djgreeb/XDJ-X/JOG VFL/VFL display description.pdf

### VFL display description

### Part Number: DEL1058-A Manufacturer: FUTABA Heater: V = 2,60-2,70Vrms or VDC Anode: V = 27,0V

### 135 sectors playing (C0-C134) 85 sectors cues (P0-P84) 3 sector vinyl sensor (V, M, S) Total: 223 segments

### 2 grids (left and right)

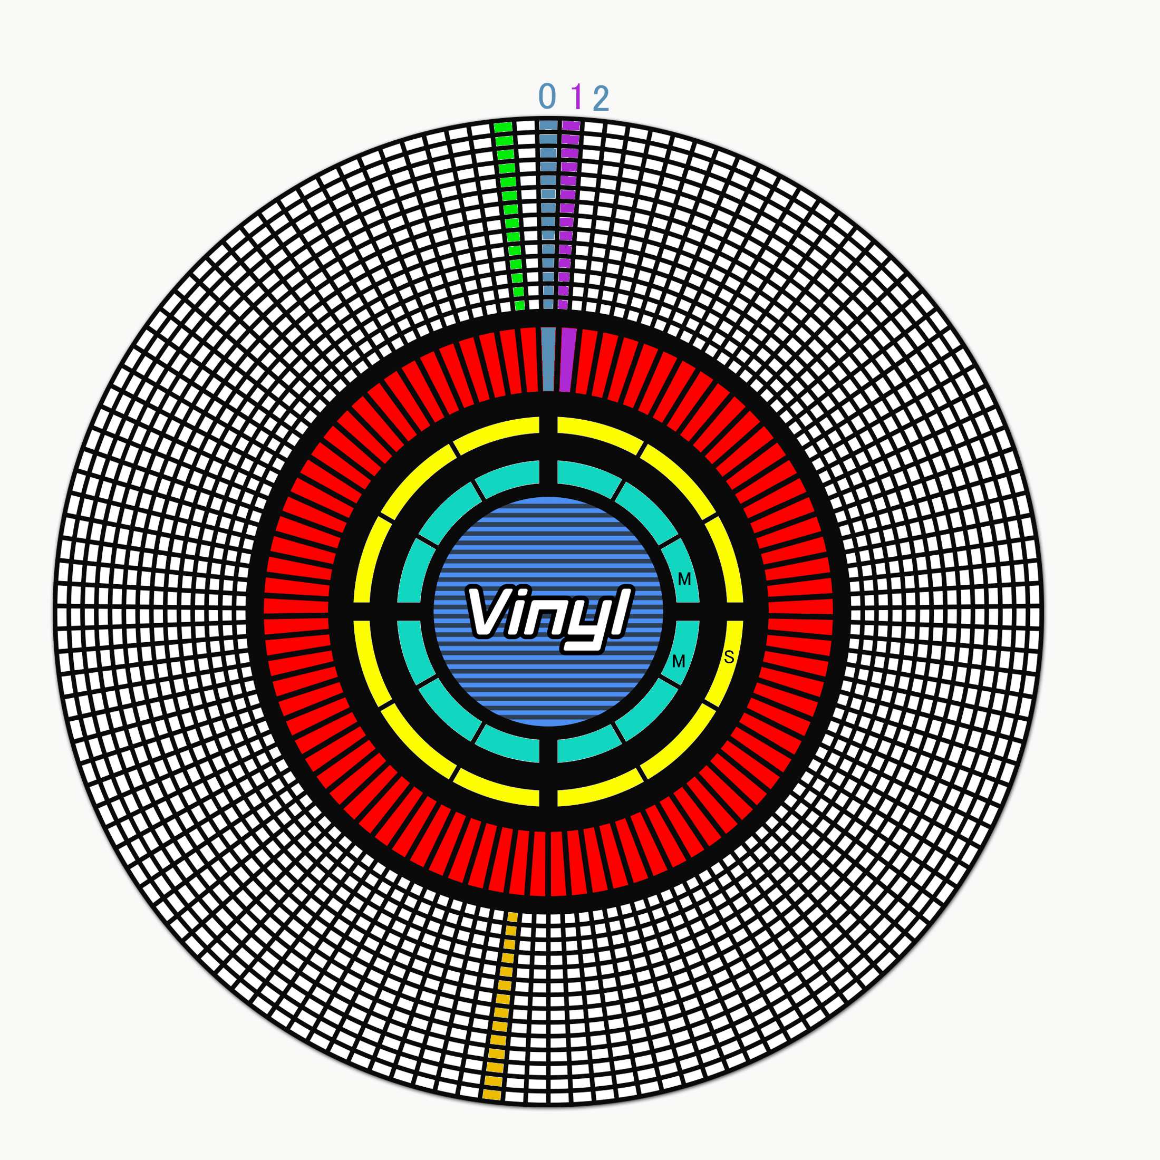
[picture p18: figure]

Num.byte | b7 | b6 | b5 | b4 | b3 | b2 | b1 | b0
0 | NC? | R grid | L grid | NC? | V | M | S | P70
1 | P69 | P68 | P67 | P66 | P65 | P64, P71 | P63, P72 | P62, P73
2 | P61, P74 | P60, P75 | P59, P76 | P58, P77 | P57, P78 | P56, P79 | P55, P80 | P54, P81
3 | C45 | C44 | C43 | P53, P82 | C42 | C41 | C40 | P52, P83
4 | C46, C39 | P51, P84 | C47, C38 | P50, P85 | C48, C37 | P49, P86 | C49, C36 | P48, P87
5 | C50, C35 | P47, P88 | C51, C34 | P46, P89 | C52, C33 | P45, P90 | C53, C32 | P44, P91
6 | C54, C31 | P43, P92 | C55, C30 | P42, P93 | C56, C29 | P41, P94 | C57, C28 | P40, P95
7 | C58, C27 | P39, P96 | C59, C26 | P38, P97 | C60, C25 | P37, P98 | C61, C24 | P36, P99
8 | C62, C23 | P35, P100 | C63, C22 | P34, P101 | C64, C21 | P33, P102 | C65, C20 | P32, P103
9 | C66, C19 | P31, P104 | C67, C18 | P30, P105 | C68, C17 | P29, P106 | C69, C16 | P28, P107
10 | C70, C15 | P27, P108 | C71, C14 | P26, P109 | C72, C13 | P25, P110 | C73, C12 | P24, P111
11 | C74, C11 | P23, P112 | C75, C10 | P22, P113 | C76, C9 | P21, P114 | C77, C8 | P20, P115
12 | C78, C7 | P19, P116 | C79, C6 | P18, P117 | C80, C5 | P17, P118 | C81, C4 | P16, P119
13 | C82, C3 | C2 | P15, P120 | C1 | C0 | P14, P121 | C84 | C83
14 | P13, P122 | P12, P123 | P11, P124 | P10, P125 | P9, P126 | P8, P127 | P7, P128 | P6, P129
15 | P5, P130 | P4, P131 | P3, P132 | P2 | P1 | P0 | P134 | P133

### Double grid

Num.byte | b7 | b6 | b5 | b4 | b3 | b2 | b1 | b0
| 0 | 1 | 2 | 3 | 4 | 5 | 6 | 7 0
| 0 | 1 | 1 | 0 | V | M | S | P70
| 8 | 9 | 10 | 11 | 12 | 13 | 14 | 15 1
| P69 | P68 | P67 | P66 | P65
| 16 | 17 | 18 | 19 | 29 | 21 | 22 | 23 2
24 | 25 | 26 | 27 | 28 | 29 | 30 | 31 3
C45 | C44 | C43 | | C42 | C41 | C40
32 | 33 | 34 | 35 | 36 | 37 | 38 | 39 4
40 | 41 | 42 | 43 | 44 | 45 | 46 | 47 5
48 | 49 | 50 | 51 | 52 | 53 | 54 | 55 6
56 | 57 | 58 | 59 | 60 | 61 | 62 | 63 7
64 | 65 | 66 | 67 | 68 | 69 | 70 | 71 8
72 | 73 | 74 | 75 | 76 | 77 | 78 | 79 9
80 | 81 | 82 | 83 | 84 | 85 | 86 | 87 10
88 | 89 | 90 | 91 | 92 | 93 | 94 | 95 11
96 | 97 | 98 | 99 | 100 | 101 | 102 | 103 12
104 | 105 | 106 | 107 | 108 | 109 | 110 | 111 13
| C2 | | C1 | C0 | | C84 | C83
112 | 113 | 114 | 115 | 116 | 117 | 118 | 119 14
120 | 121 | 122 | 123 | 124 | 125 | 126 | 127 15
| | | P2 | P1 | P0 | P134 | P133

### Left grid

Num.byte | b7 | b6 | b5 | b4 | b3 | b2 | b1 | b0
| 128 | 129 | 130 | 131 | 132 | 133 | 134 | 135 16
| 0 | 0 | 1 | 0
| 136 | 137 | 138 | 139 | 140 | 141 | 142 | 143 17
| | | | | | P71 | P72 | P73
| 144 | 145 | 146 | 147 | 148 | 149 | 150 | 151 18
P74 | P75 | P76 | P77 | P78 | P79 | P80 | P81
| 152 | 153 | 154 | 155 | 156 | 157 | 158 | 159 19
| | | | P82 | | | | P83
| 160 | 161 | 162 | 163 | 164 | 165 | 166 | 167 20
| C46 | P84 | C47 | P85 | C48 | P86 | C49 | P87
| 168 | 169 | 170 | 171 | 172 | 173 | 174 | 175 21
| C50 | P88 | C51 | P89 | C52 | P90 | C53 | P91
| 176 | 177 | 178 | 179 | 180 | 181 | 182 | 183 22
| C54 | P92 | C55 | P93 | C56 | P94 | C57 | P95
| 184 | 185 | 186 | 187 | 188 | 189 | 190 | 191 23
| C58 | P96 | C59 | P97 | C60 | P98 | C61 | P99
| 192 | 193 | 194 | 195 | 196 | 197 | 198 | 199 24
| C62 | P100 | C63 | P101 | C64 | P102 | C65 | P103
| 200 | 201 | 202 | 203 | 204 | 205 | 206 | 207 25
| C66 | P104 | C67 | P105 | C68 | P106 | C69 | P107
| 208 | 209 | 210 | 211 | 212 | 213 | 214 | 215 26
| C70 | P108 | C71 | P109 | C72 | P110 | C73 | P111
| 216 | 217 | 218 | 219 | 220 | 221 | 222 | 223 27
| C74 | P112 | C75 | P113 | C76 | P114 | C77 | P115
| 224 | 225 | 226 | 227 | 228 | 229 | 230 | 231 28
C78 | P116 | C79 | P117 | C80 | P118 | C81 | P119
| 232 | 233 | 234 | 235 | 236 | 237 | 238 | 239 29
| C82 | | P120 | | | P121
| 240 | 241 | 242 | 243 | 244 | 245 | 246 | 247 30
| P122 | P123 | P124 | P125 | P126 | P127 | P128 | P129
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
| 360 | 361 | 362 | 363 | 364 | 365 | 366 | 367 45
| C3 | | P15 | | | P14
| 368 | 369 | 370 | 371 | 372 | 373 | 374 | 375 46
P13 | P12 | P11 | P10 | P9 | P8 | P7 | P6
| 376 | 377 | 378 | 379 | 380 | 381 | 382 | 383 47
| P5 | P4 | P3

### Author: Andrei Anatska
