djgreeb/XDJ-X/Bluetooth/Ugreen TX/IMG_7054.JPG

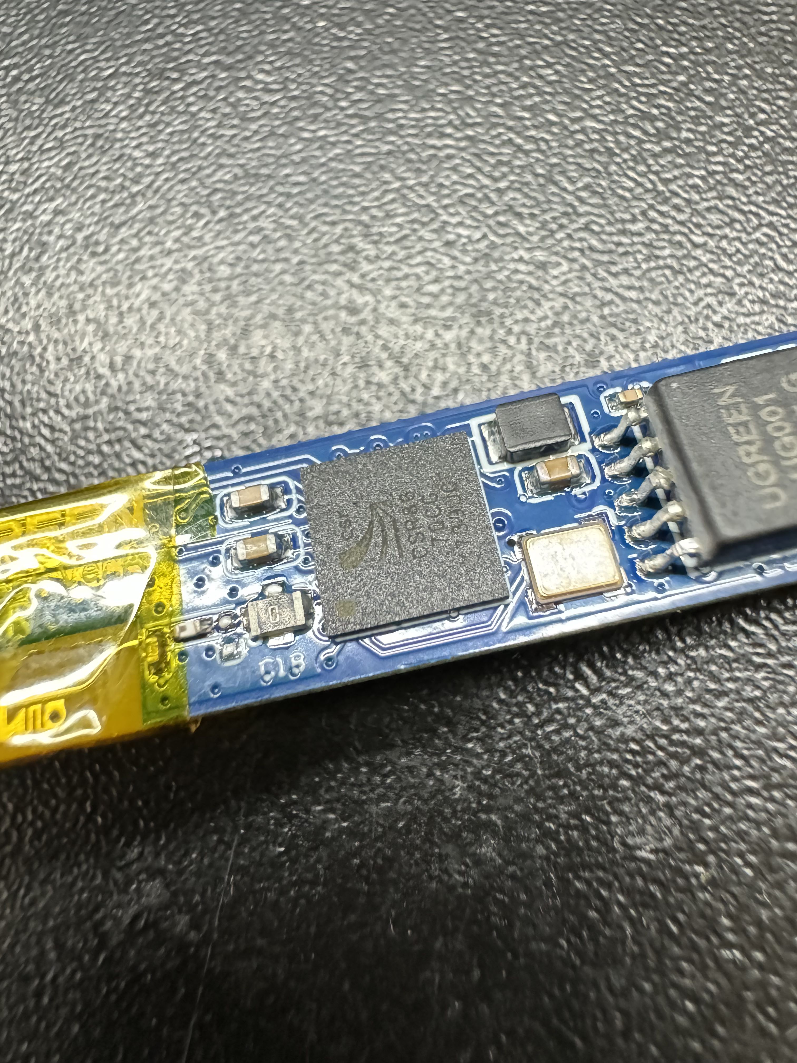
Bluetooth/Ugreen TX/IMG_7054.JPG
