djgreeb/XDJ-X/Bluetooth/Ugreen TX/IMG_7055.JPG

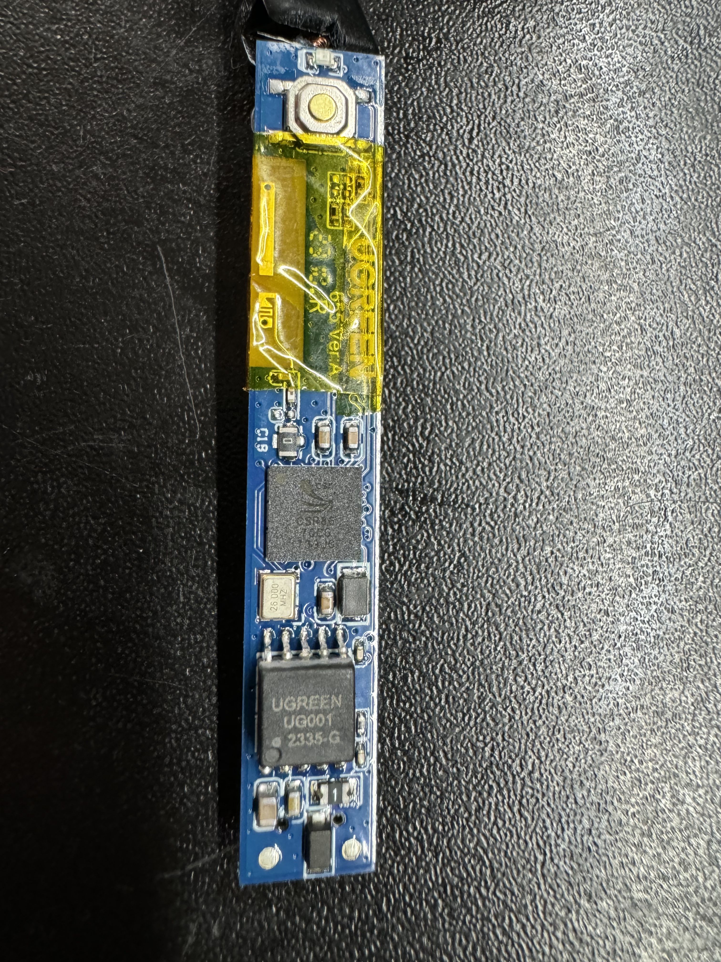
Bluetooth/Ugreen TX/IMG_7055.JPG
