djgreeb/XDJ-X/DECK_ASSY/FW_BACKUP/PINS sockets.png

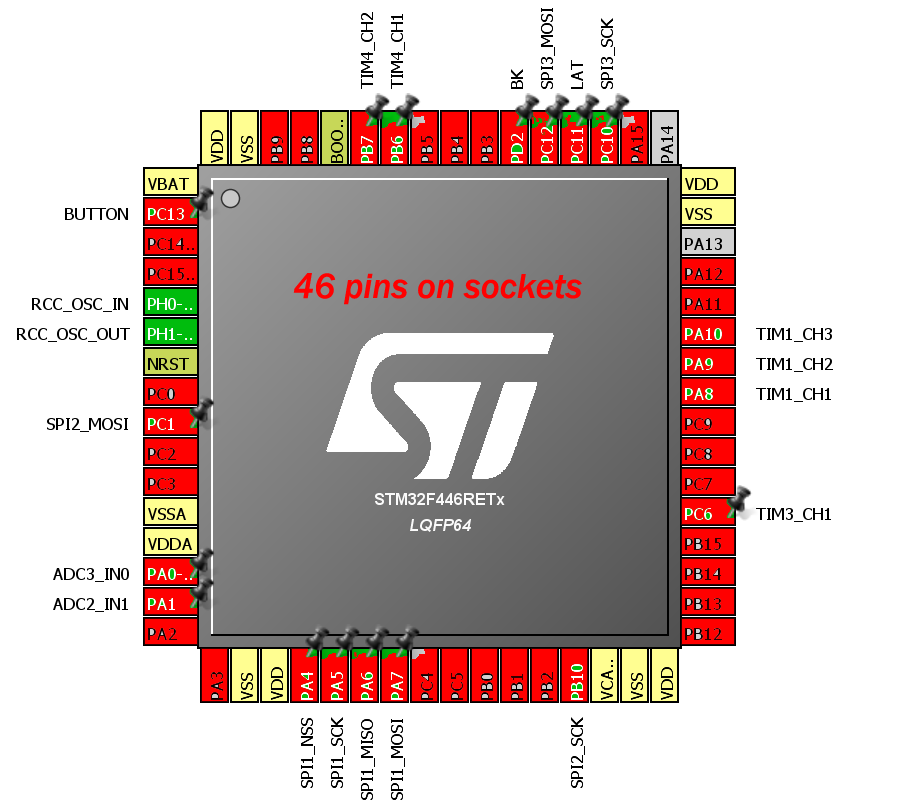
DECK_ASSY/FW_BACKUP/PINS sockets.png
