djgreeb/XDJ-X/DECK_ASSY/IMG_7581.JPG

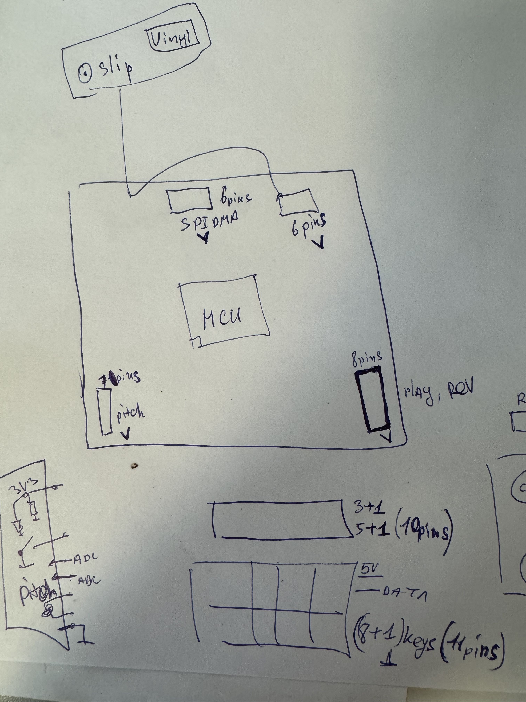
DECK_ASSY/IMG_7581.JPG
