djgreeb/XDJ-X/DECK_ASSY/IMG_7596.JPG

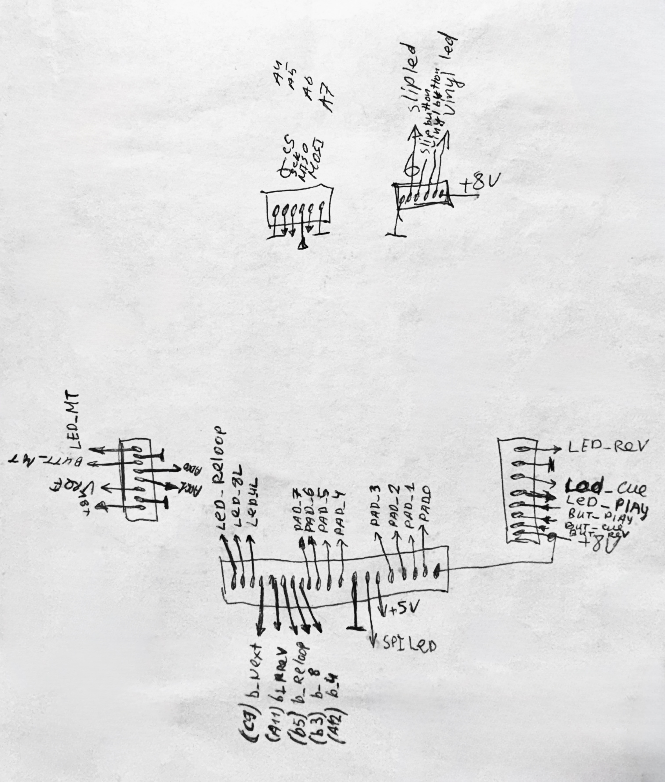
DECK_ASSY/IMG_7596.JPG
