djgreeb/XDJ-X/JOG VFL/CDJ-2000nxs/F1.png

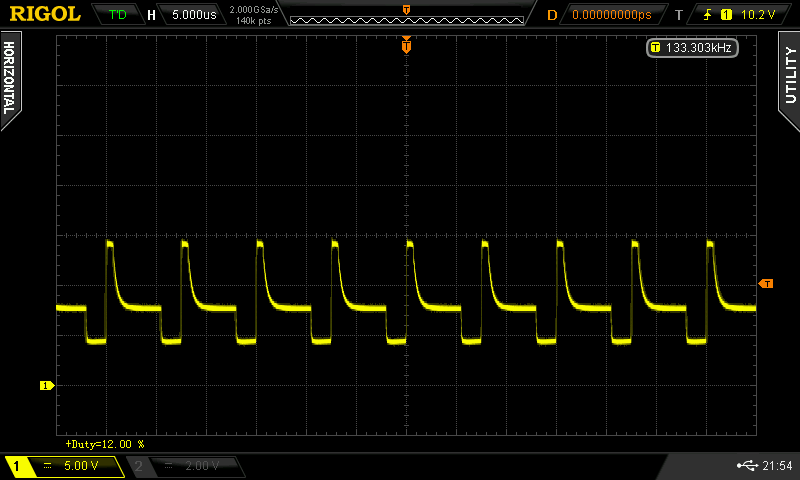
JOG VFL/CDJ-2000nxs/F1.png
