djgreeb/XDJ-X/JOG VFL/CDJ-2000nxs/F2.png

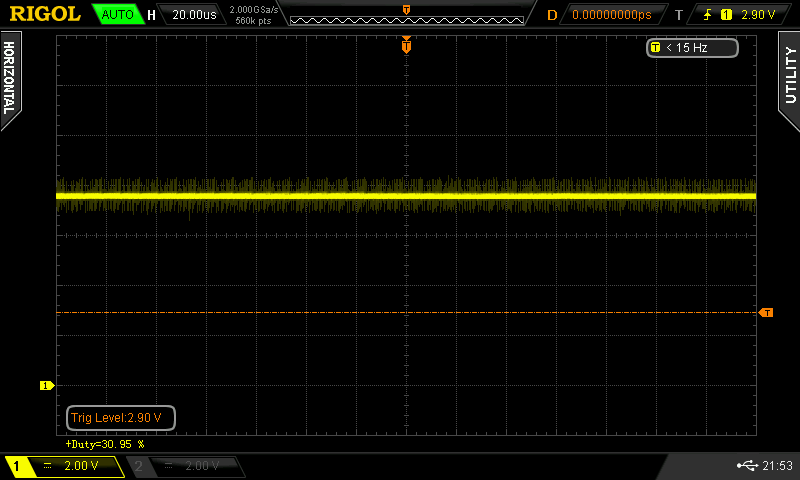
JOG VFL/CDJ-2000nxs/F2.png
