djgreeb/XDJ-X/JOG VFL/CDJ-2000nxs/tft spi clk.png

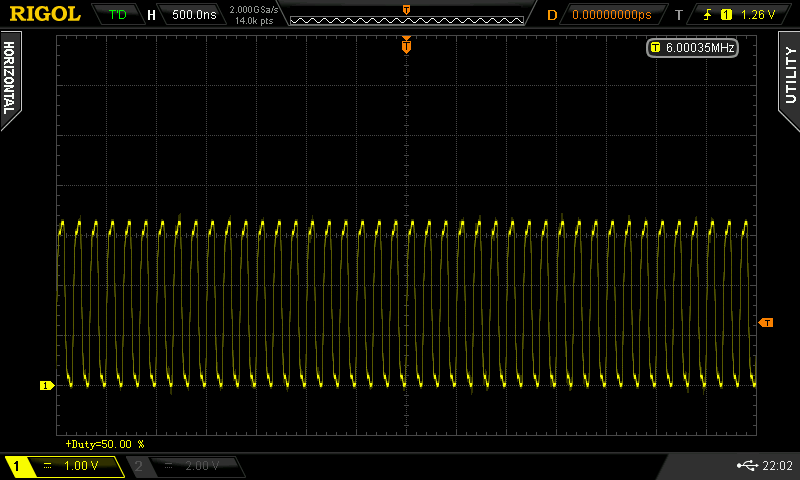
JOG VFL/CDJ-2000nxs/tft spi clk.png
