djgreeb/XDJ-X/JOG VFL/CDJ-2000nxs/tft spi cs.png

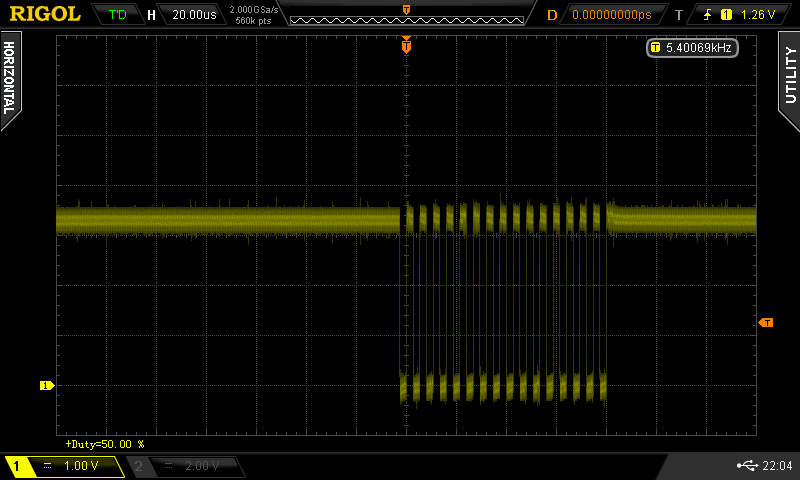
JOG VFL/CDJ-2000nxs/tft spi cs.png
