djgreeb/XDJ-X/JOG VFL/CDJ-2000nxs/tft spi data(1).png

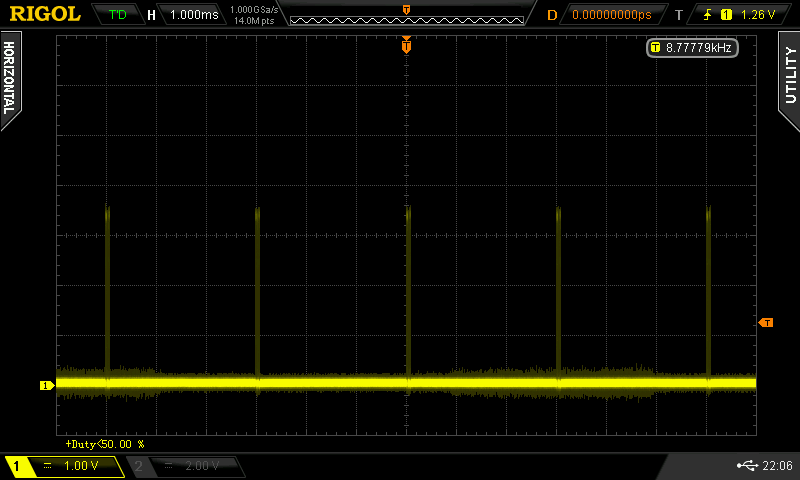
JOG VFL/CDJ-2000nxs/tft spi data(1).png
