djgreeb/XDJ-X/JOG VFL/CDJ-2000nxs/tft spi data.png

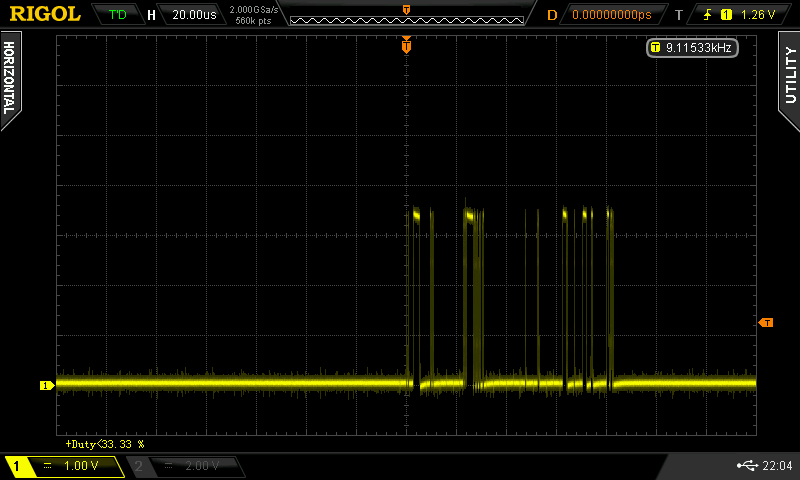
JOG VFL/CDJ-2000nxs/tft spi data.png
