djgreeb/XDJ-X/JOG VFL/CDJ-2000nxs/Transformer diode.png

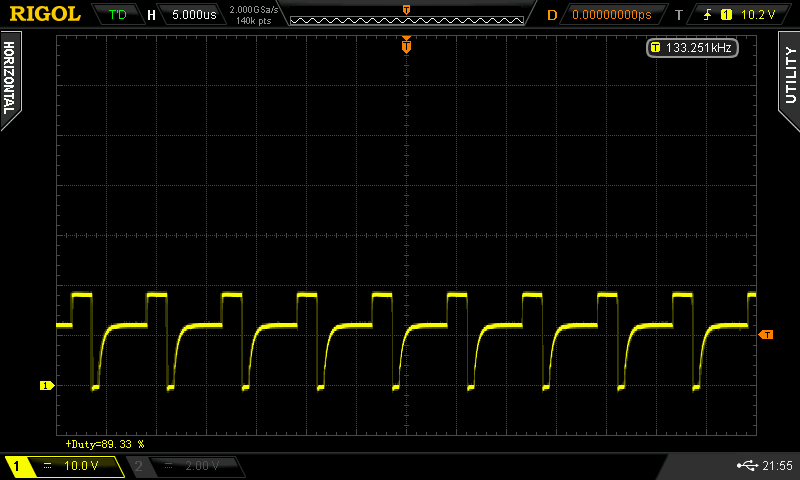
JOG VFL/CDJ-2000nxs/Transformer diode.png
