djgreeb/XDJ-X/JOG VFL/CDJ-2000nxs/Transformer input.png

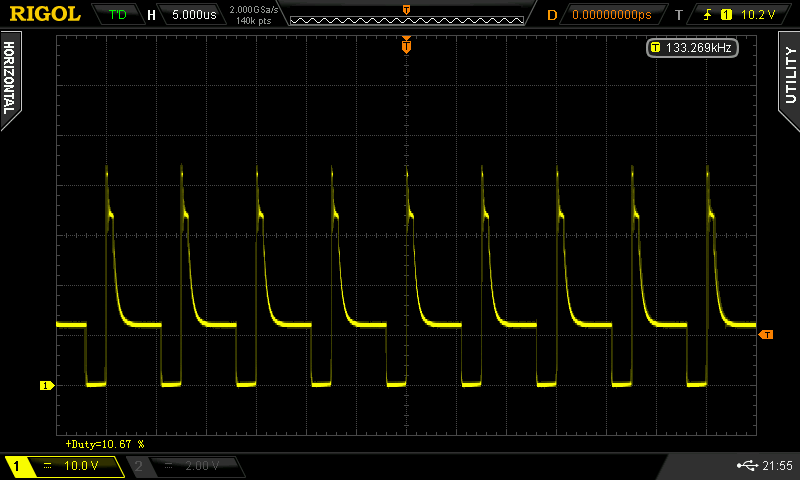
JOG VFL/CDJ-2000nxs/Transformer input.png
