djgreeb/XDJ-X/JOG VFL/Transformer charasteristics.JPG

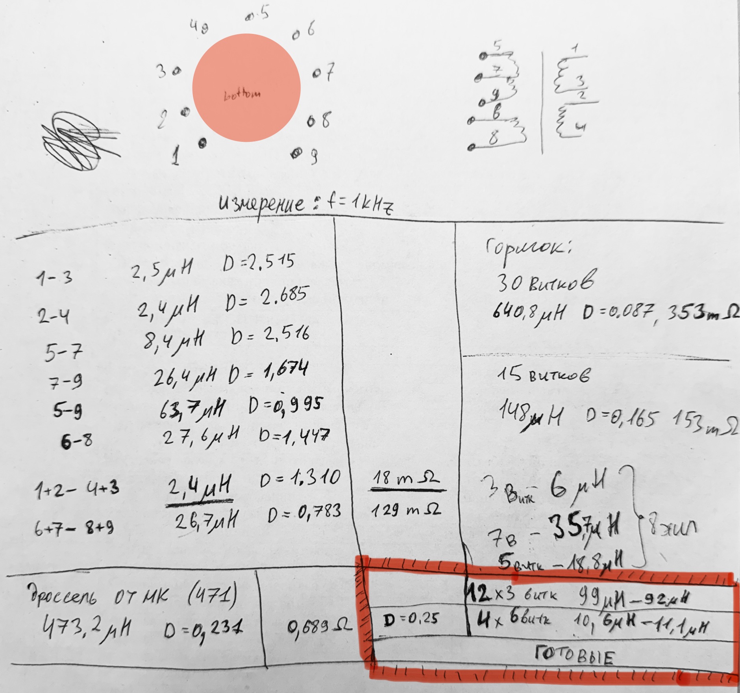
JOG VFL/Transformer charasteristics.JPG
