djgreeb/XDJ-X/Mixer assy/DSP block diagram.png

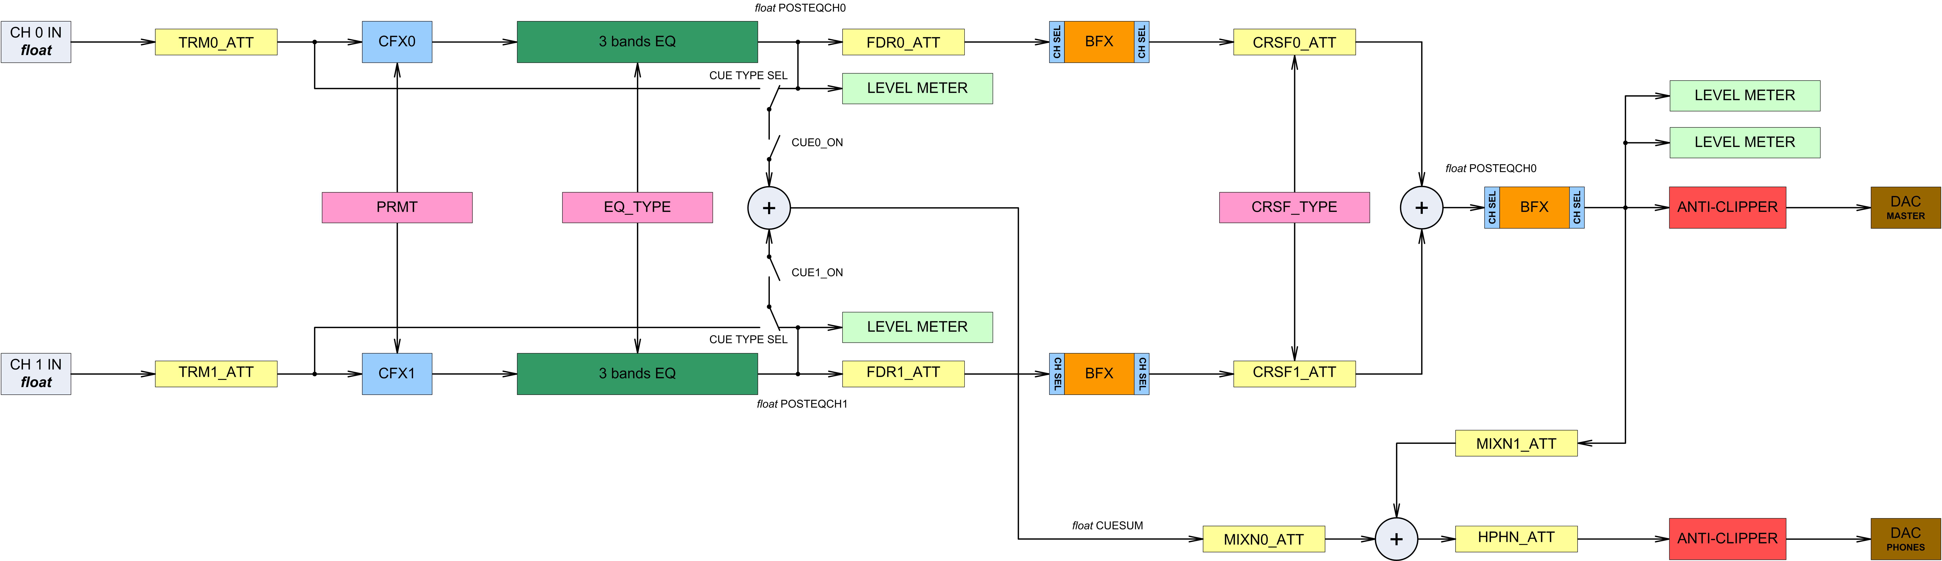
Mixer assy/DSP block diagram.png
