djgreeb/XDJ-X/Mixer assy/FX_display.bmp

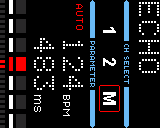
Mixer assy/FX_display.bmp
