djgreeb/XDJ-X/Mixer assy/Mixer assy laser.png

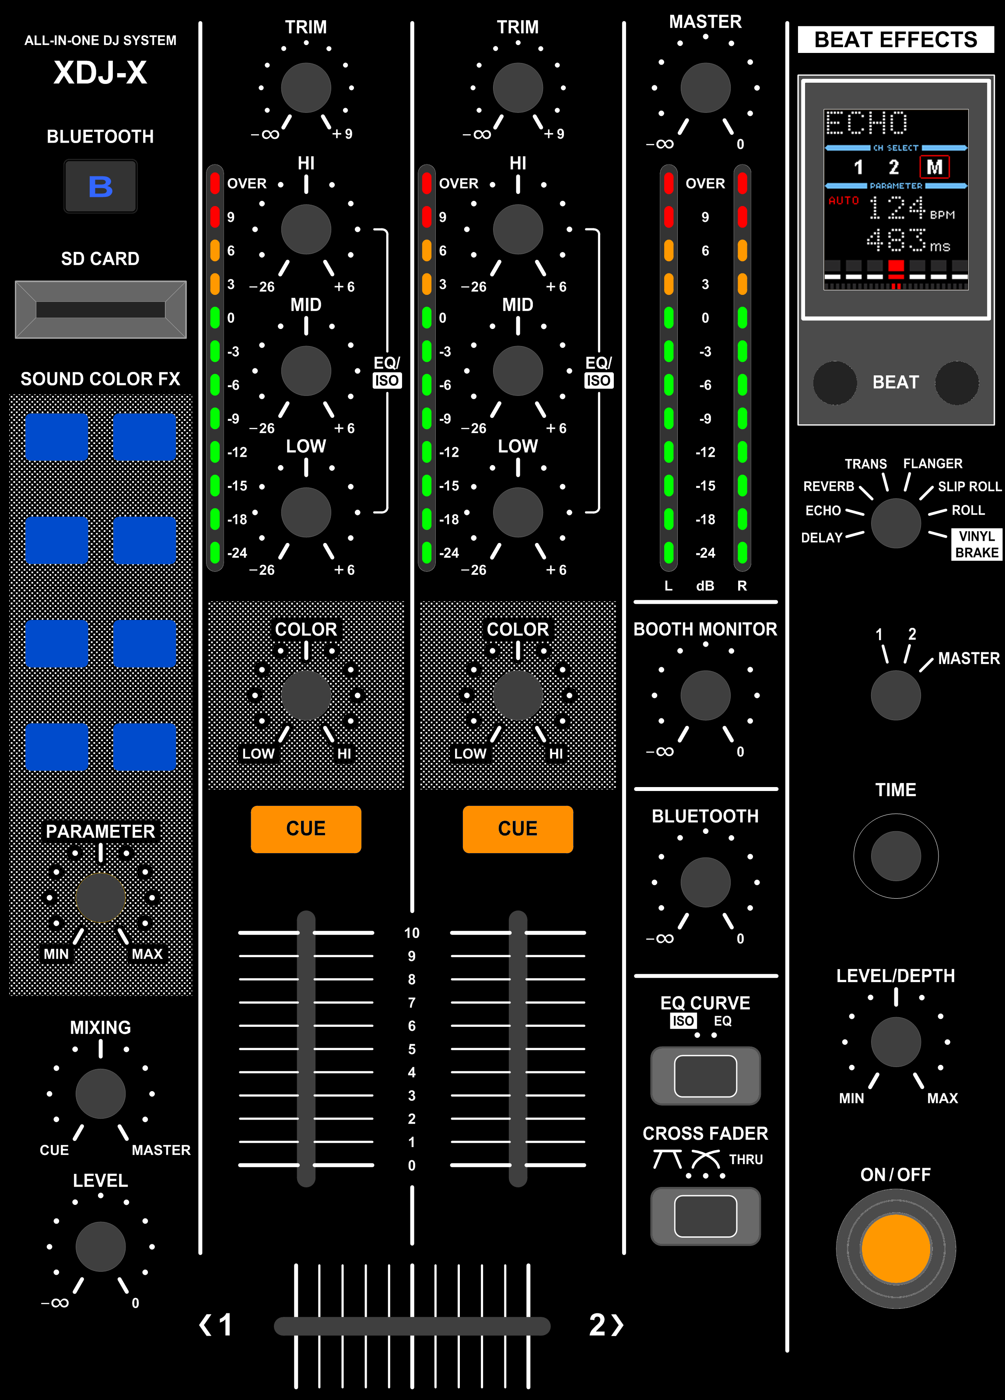
Mixer assy/Mixer assy laser.png
