djgreeb/XDJ-X/OVERALL BLOCK DIAGRAM.png

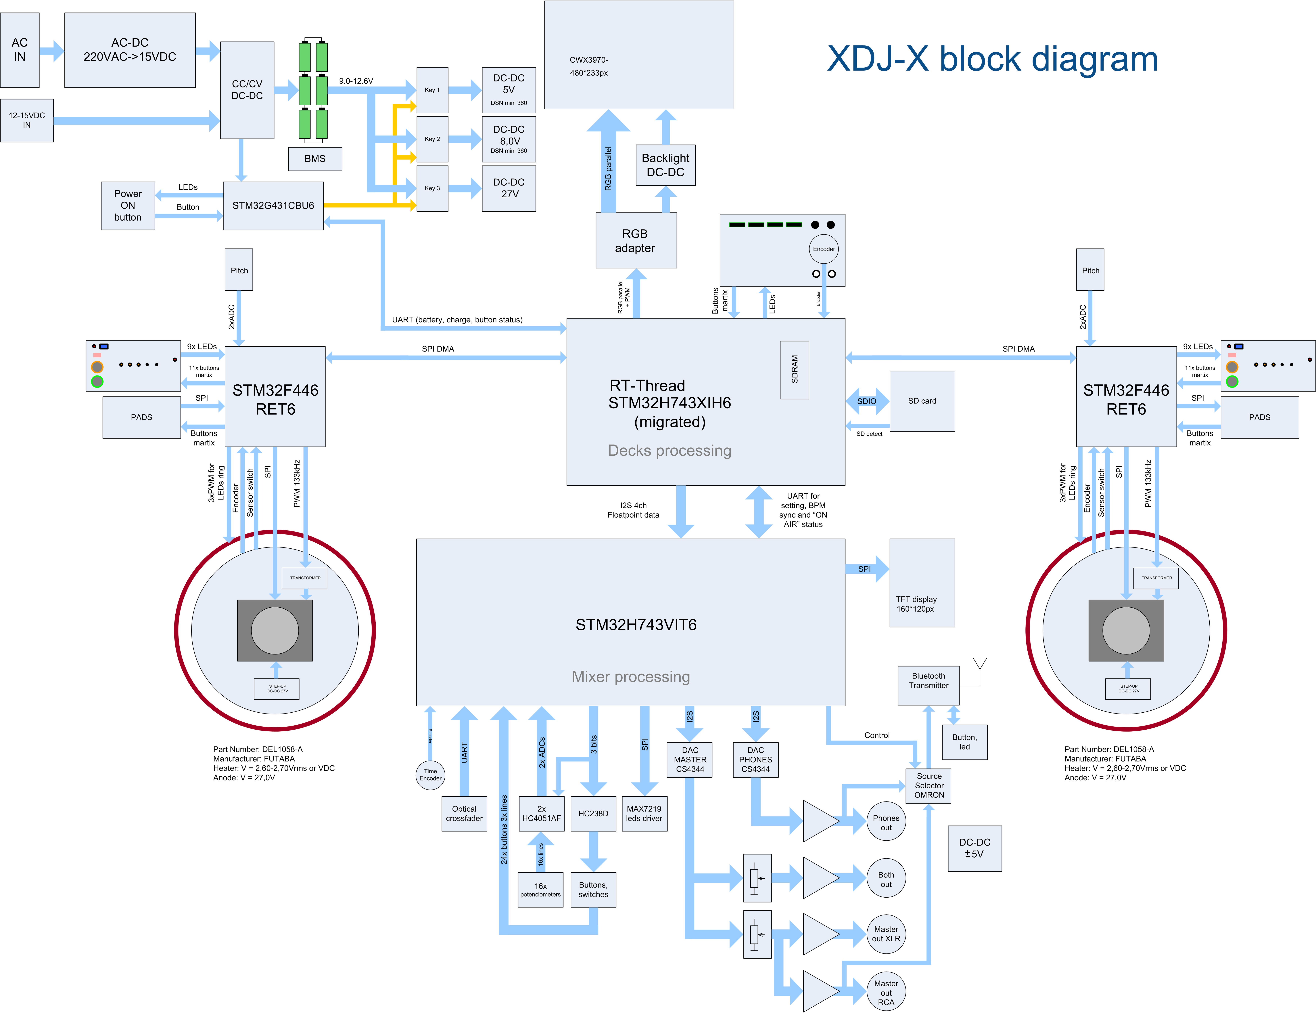
OVERALL BLOCK DIAGRAM.png
