djgreeb/XDJ-X/Photo/01.jpg

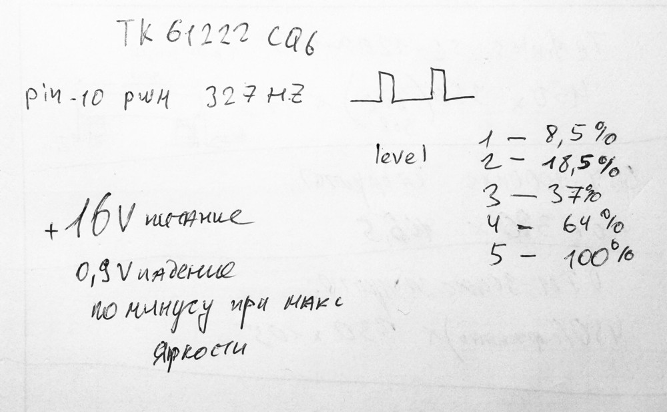
Photo/01.jpg
