djgreeb/XDJ-X/Photo/02.jpg

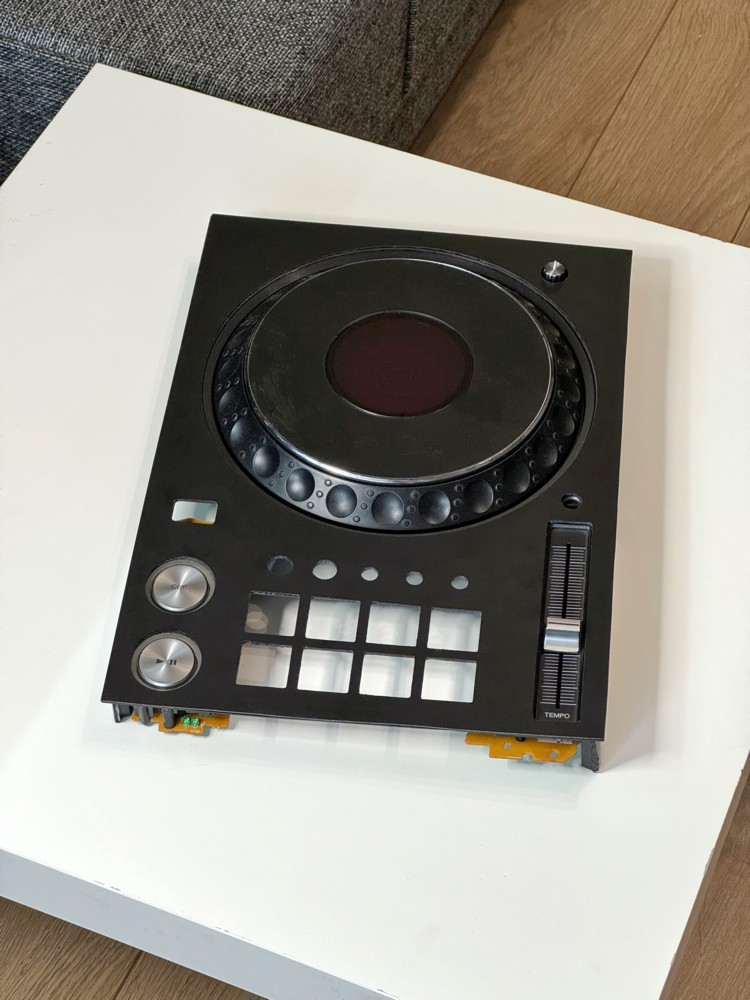
Photo/02.jpg
