djgreeb/XDJ-X/Photo/03.jpg

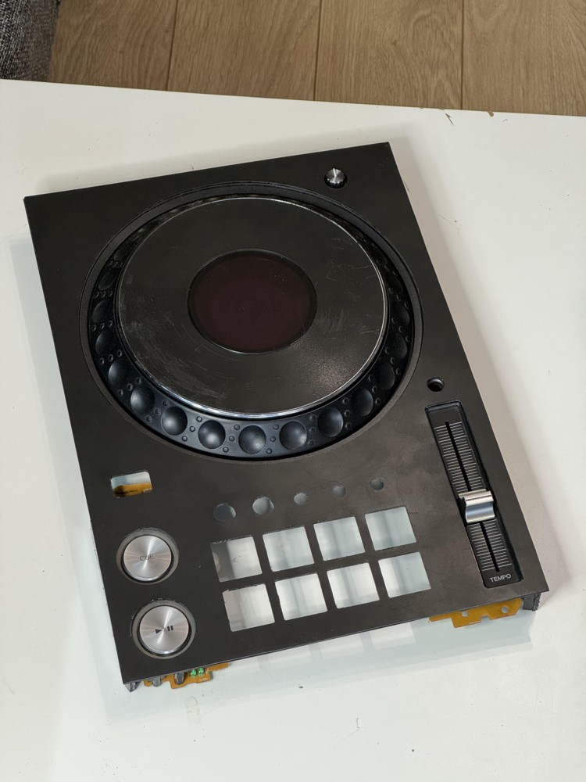
Photo/03.jpg
