djgreeb/XDJ-X/Photo/04.jpg

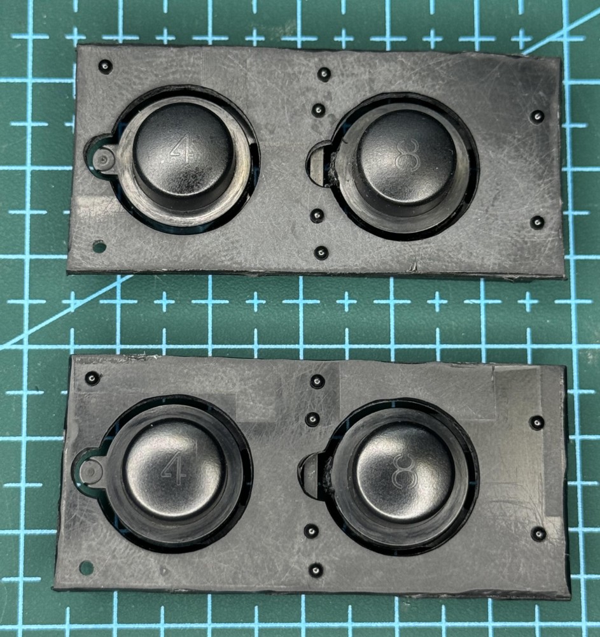
Photo/04.jpg
