djgreeb/XDJ-X/Photo/05.jpg

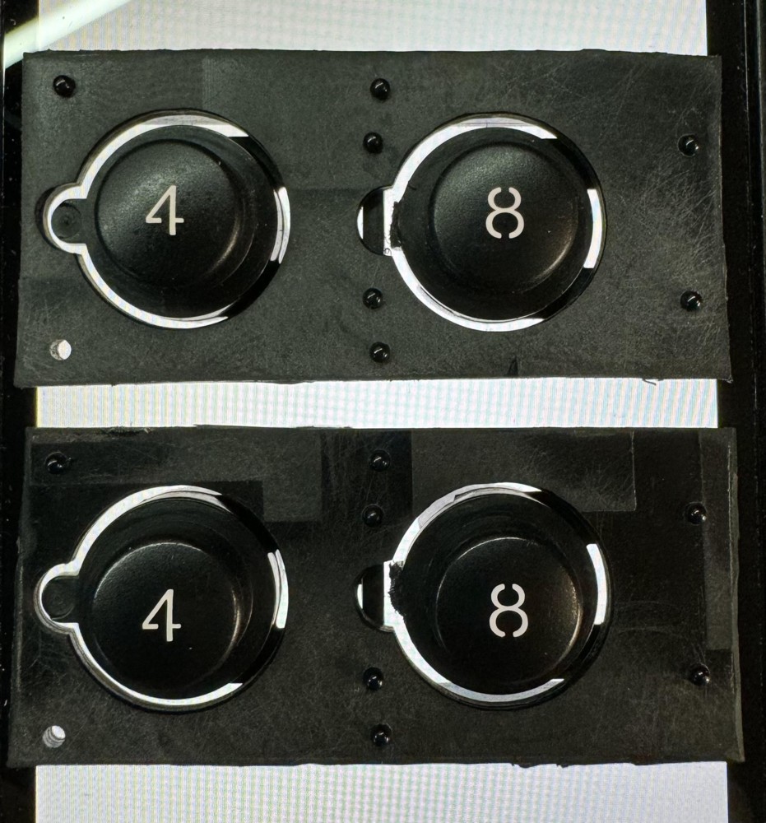
Photo/05.jpg
