djgreeb/XDJ-X/Photo/06.jpg

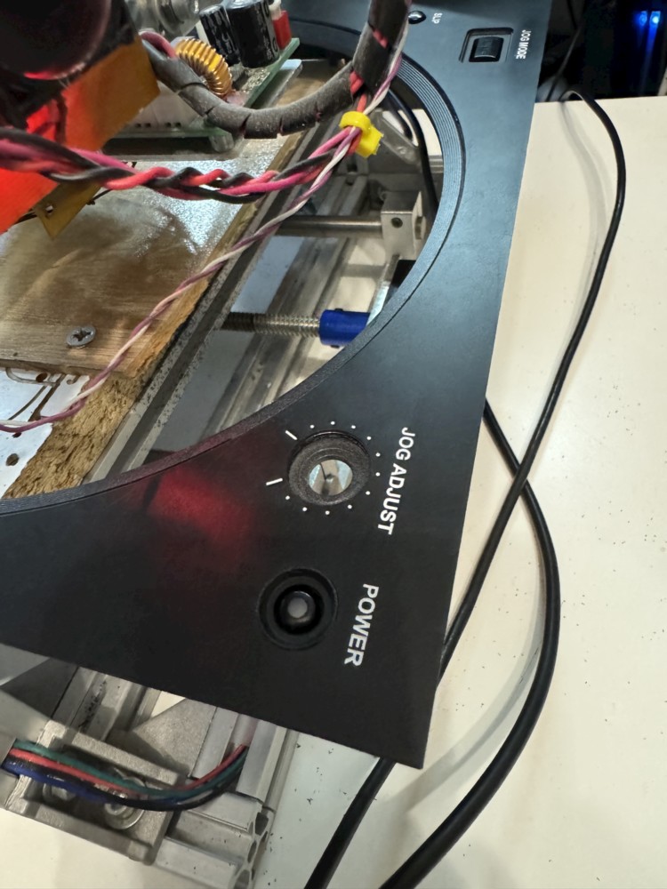
Photo/06.jpg
