djgreeb/XDJ-X/Photo/07.jpg

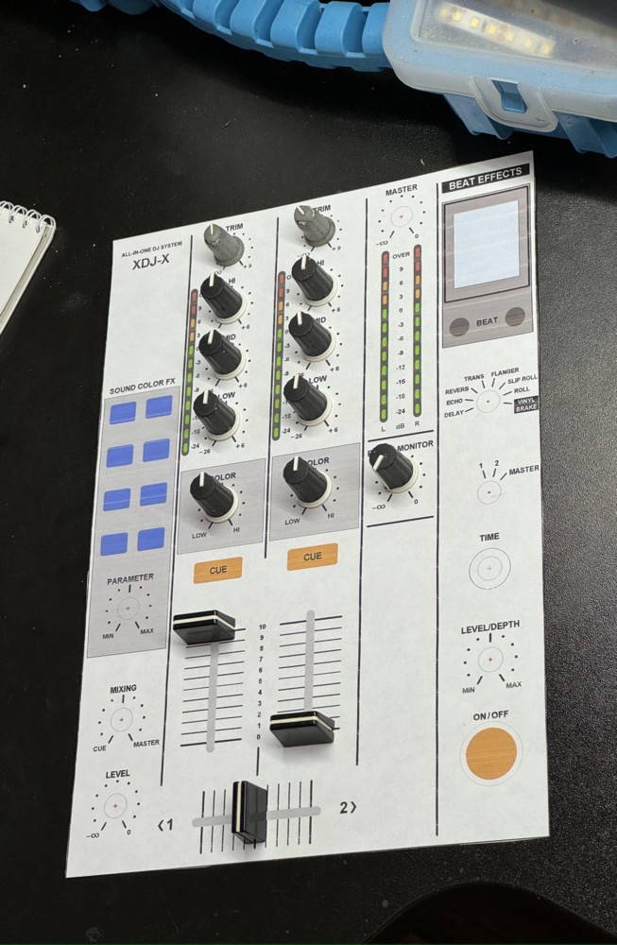
Photo/07.jpg
