djgreeb/XDJ-X/Photo/08.jpg

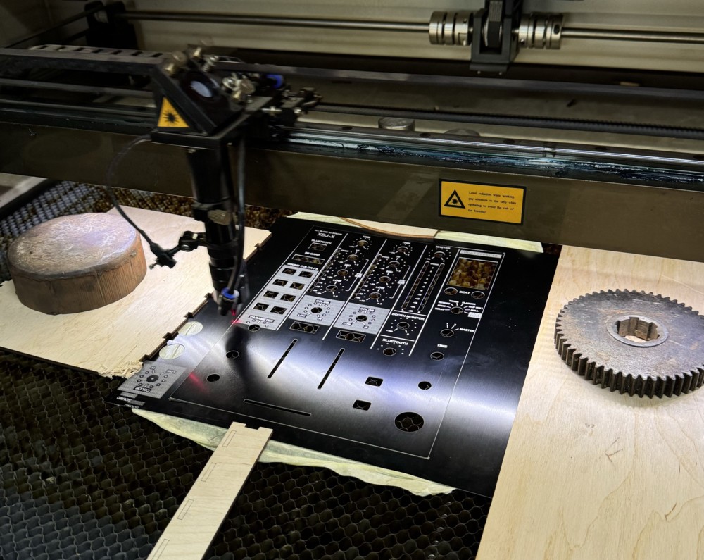
Photo/08.jpg
