djgreeb/XDJ-X/Photo/09.jpg

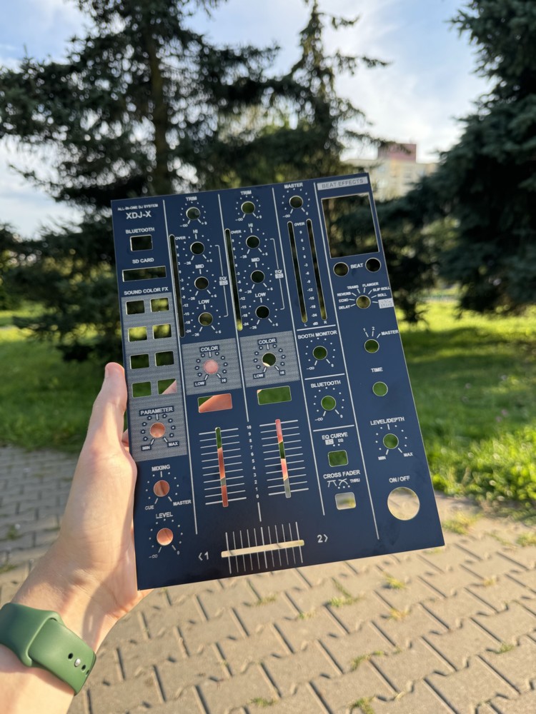
Photo/09.jpg
