djgreeb/XDJ-X/Photo/10.jpg

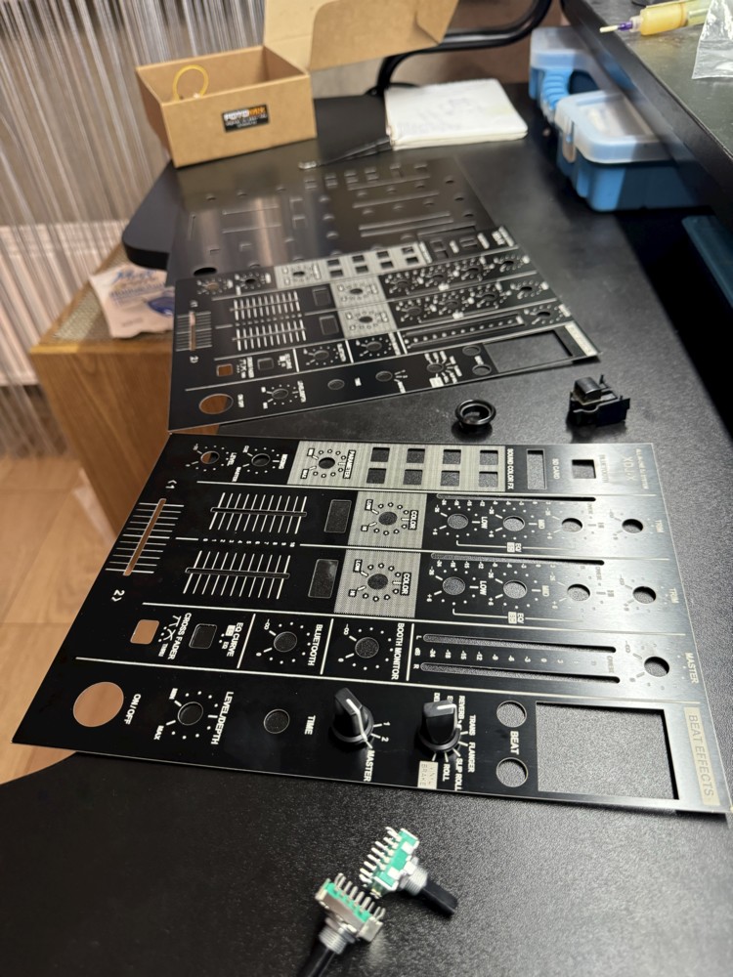
Photo/10.jpg
