djgreeb/XDJ-X/Photo/11.jpg

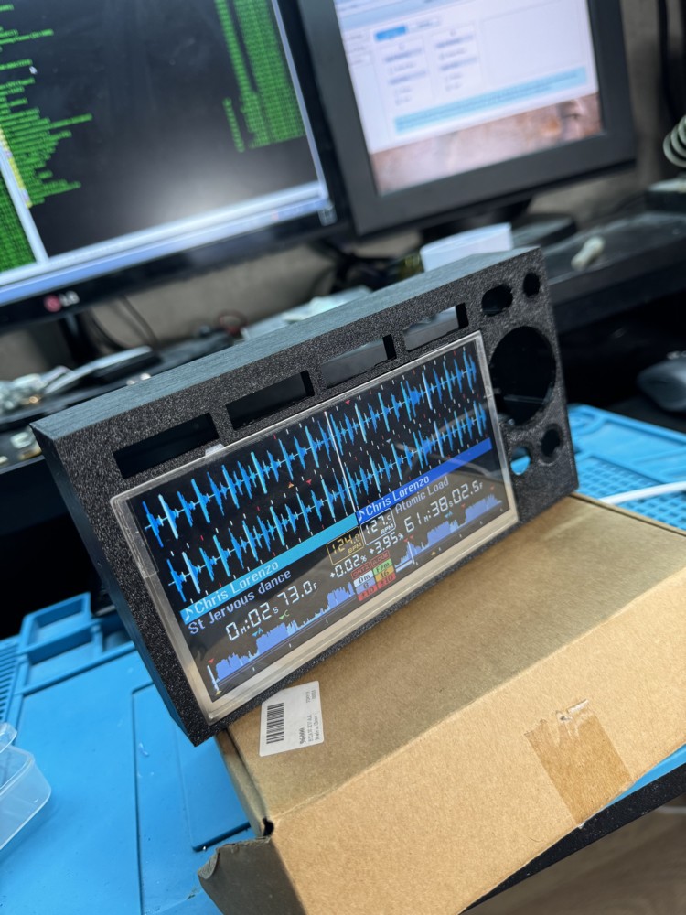
Photo/11.jpg
