djgreeb/XDJ-X/Photo/12.jpg

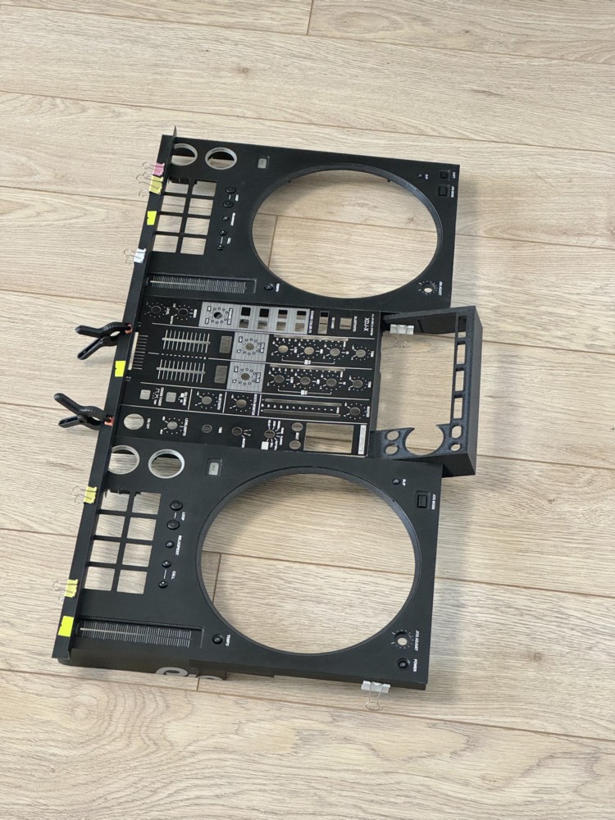
Photo/12.jpg
