djgreeb/XDJ-X/Photo/13.jpg

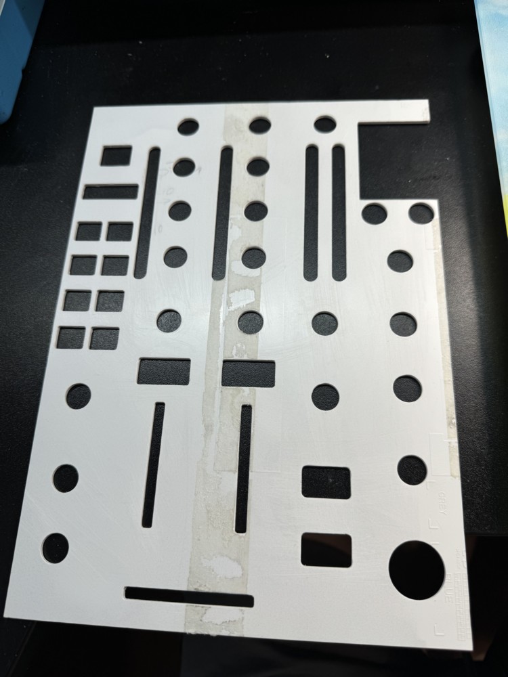
Photo/13.jpg
