djgreeb/XDJ-X/Photo/14.jpg

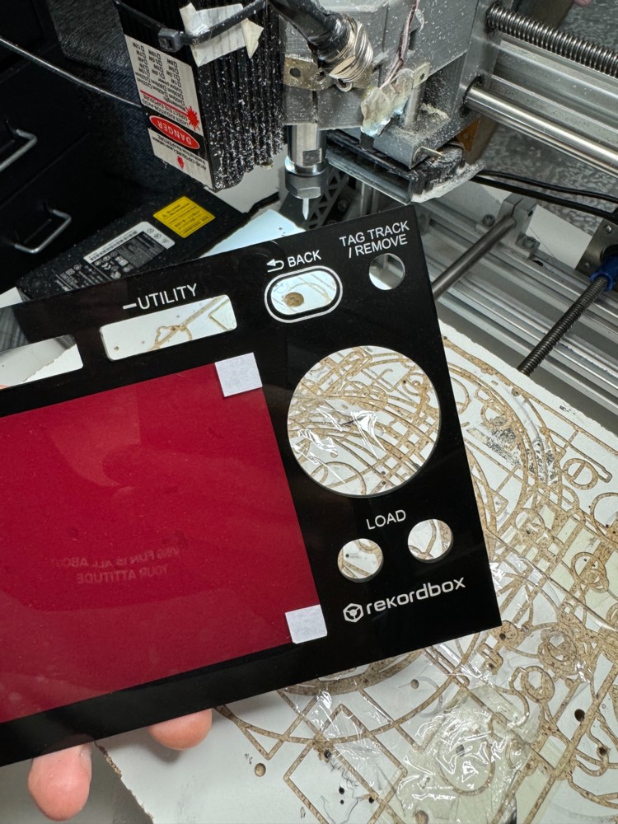
Photo/14.jpg
