djgreeb/XDJ-X/Photo/15.jpg

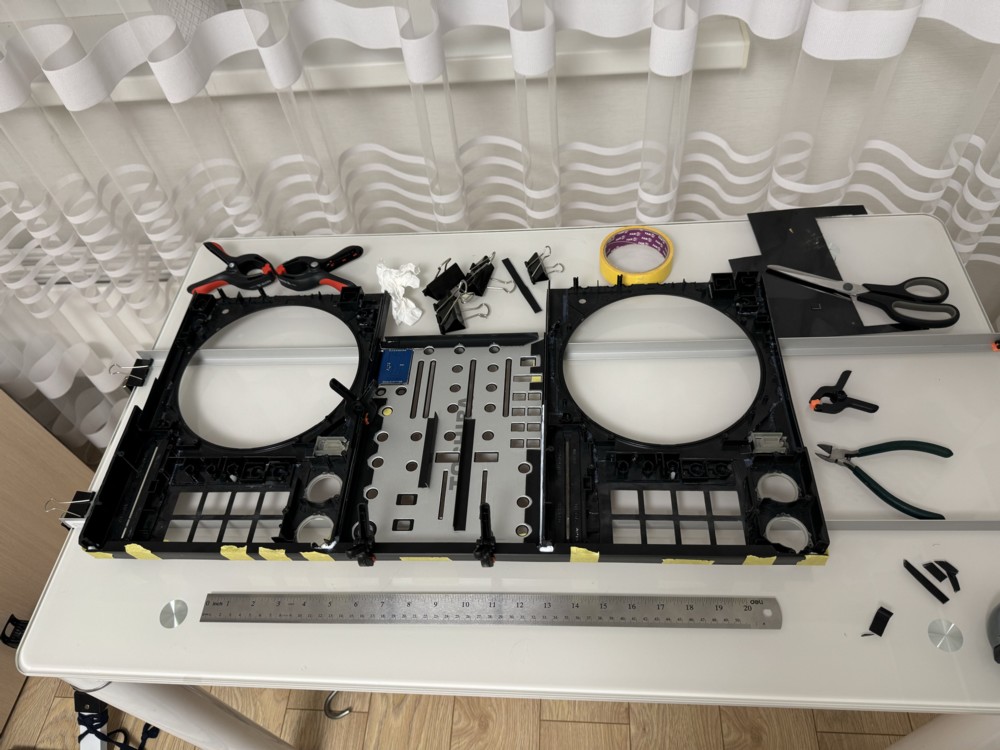
Photo/15.jpg
