djgreeb/XDJ-X/Photo/16.jpg

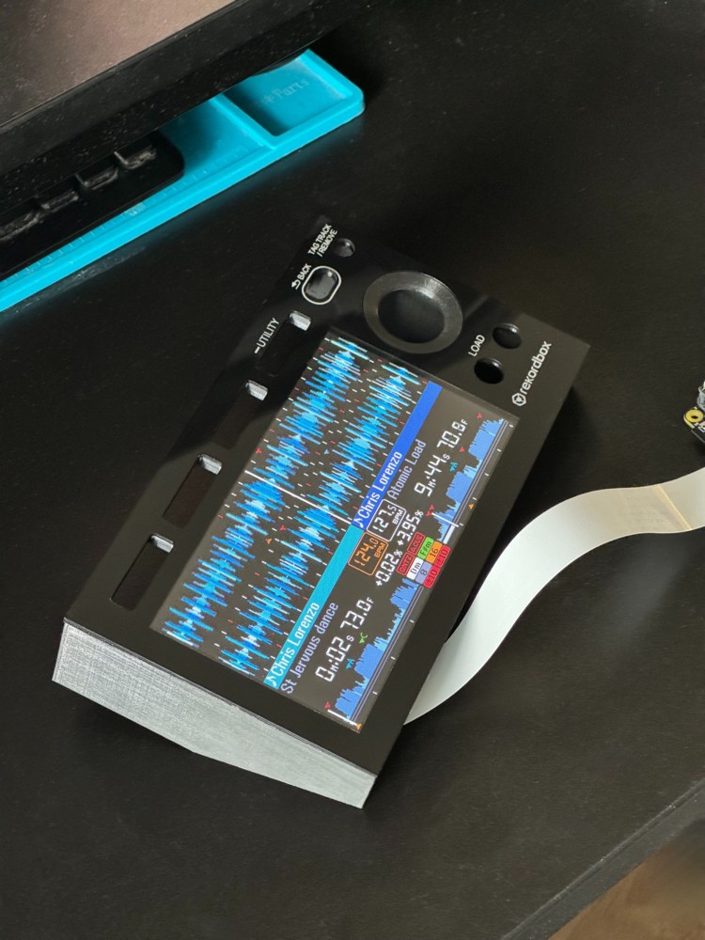
Photo/16.jpg
