djgreeb/XDJ-X/Photo/17.jpg

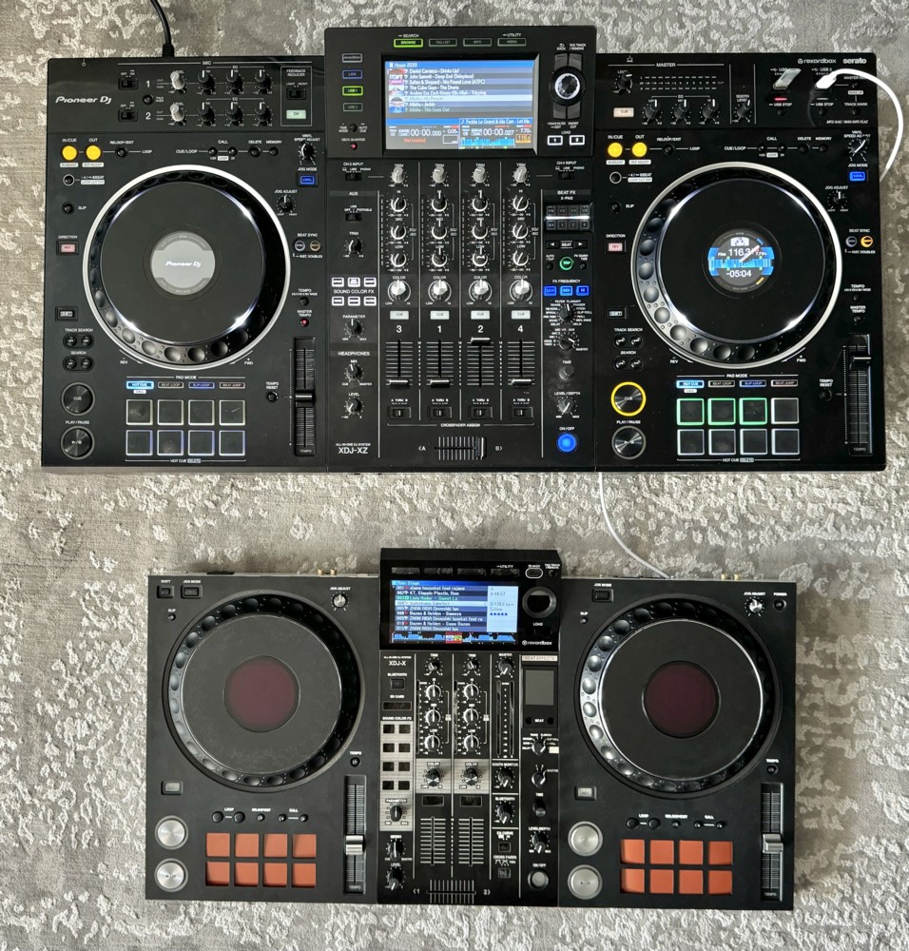
Photo/17.jpg
