djgreeb/XDJ-X/Photo/18.jpg

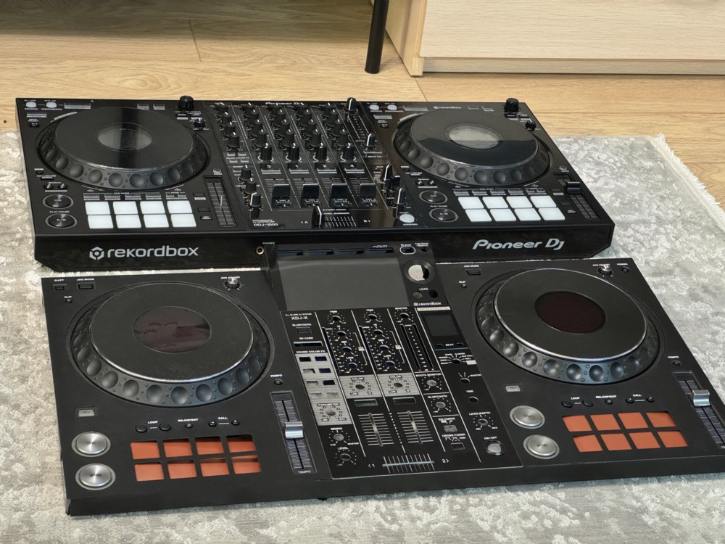
Photo/18.jpg
