djgreeb/XDJ-X/Photo/19.jpg

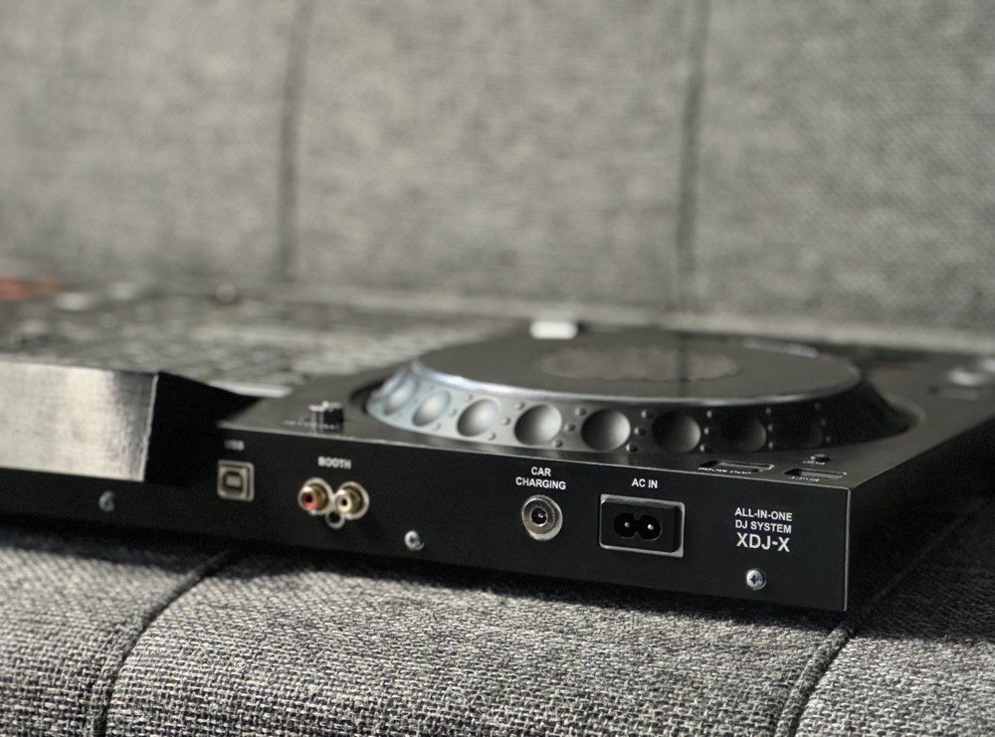
Photo/19.jpg
