djgreeb/XDJ-X/Photo/20.jpg

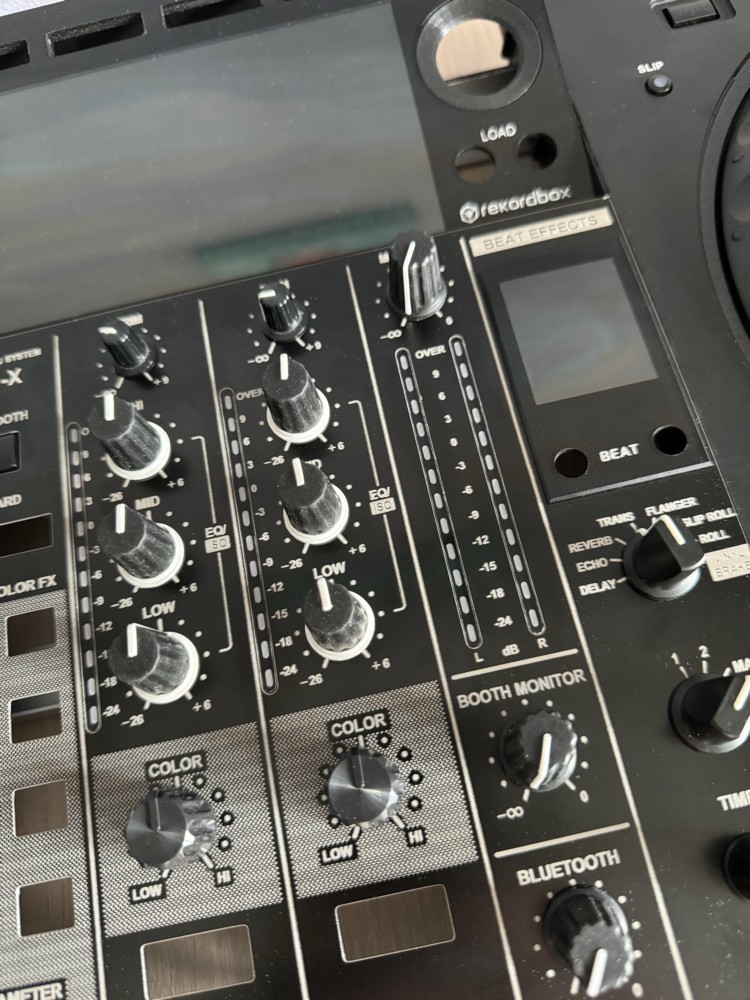
Photo/20.jpg
