djgreeb/XDJ-X/Photo/21.jpg

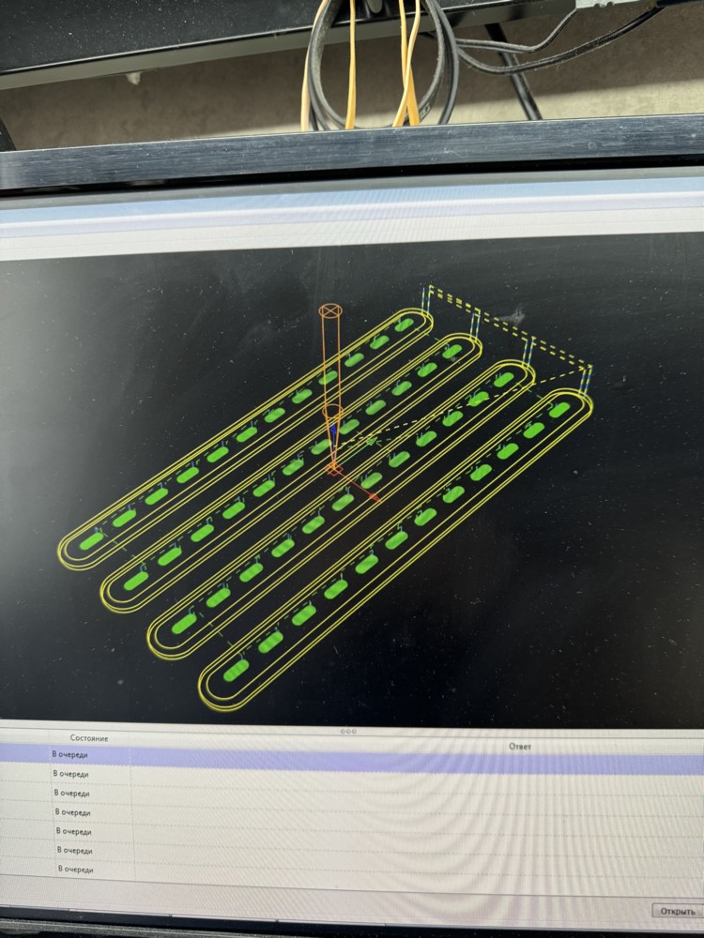
Photo/21.jpg
