djgreeb/XDJ-X/Photo/22.jpg

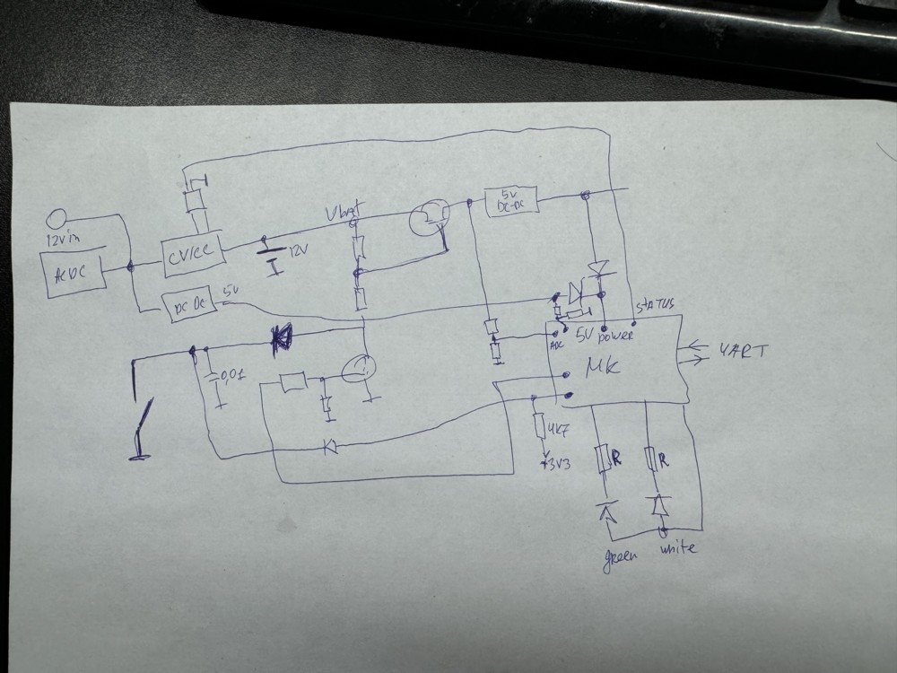
Photo/22.jpg
