djgreeb/XDJ-X/Photo/23.jpg

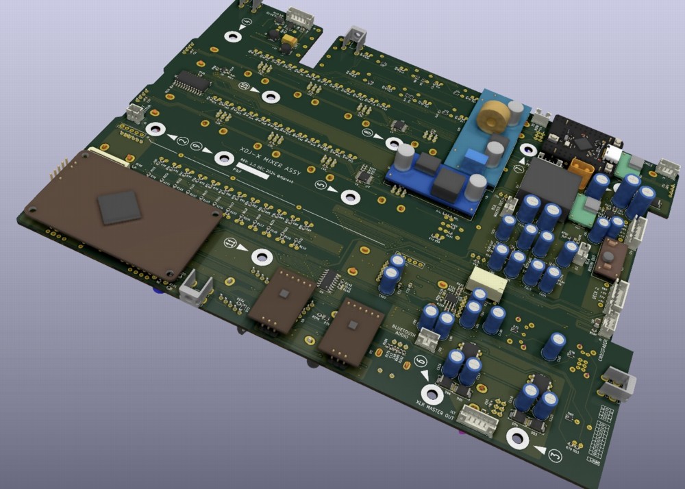
Photo/23.jpg
