djgreeb/XDJ-X/Photo/24.jpg

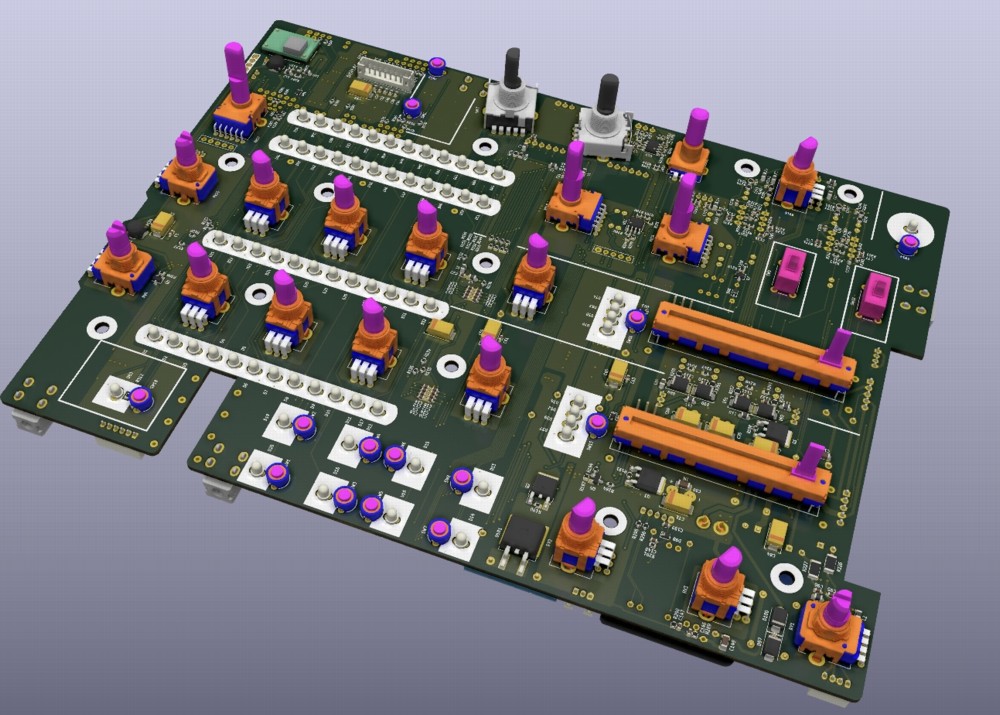
Photo/24.jpg
