djgreeb/XDJ-X/Photo/25.jpg

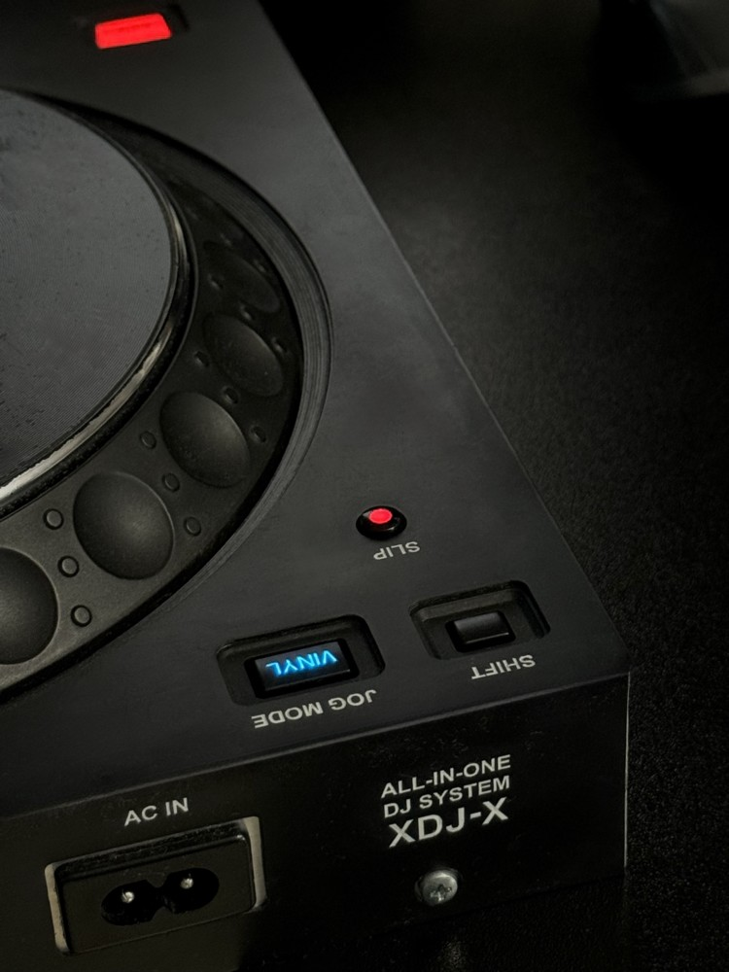
Photo/25.jpg
