djgreeb/XDJ-X/Photo/26.jpg

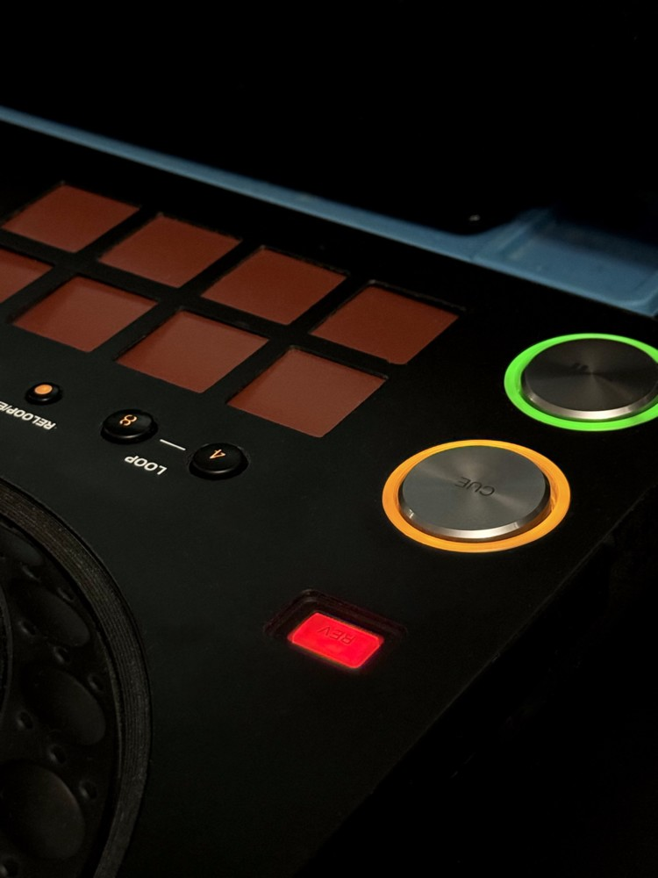
Photo/26.jpg
