djgreeb/XDJ-X/Photo/27.jpg

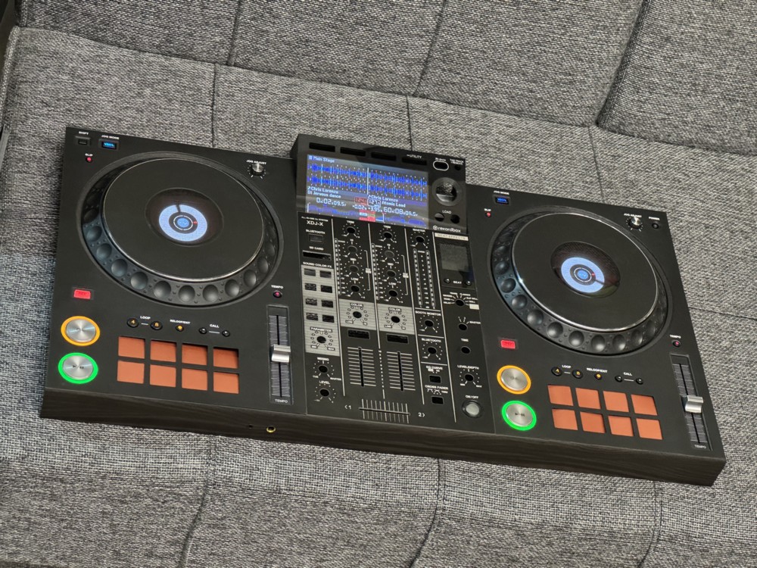
Photo/27.jpg
