djgreeb/XDJ-X/Photo/28.jpg

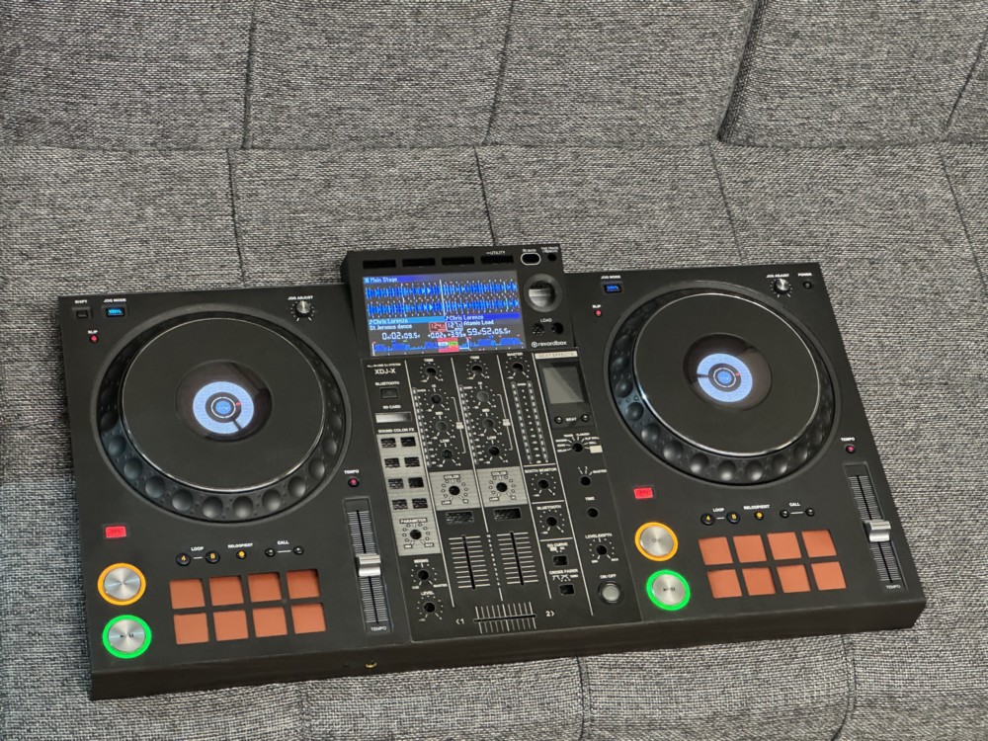
Photo/28.jpg
