djgreeb/XDJ-X/Photo/29.jpg

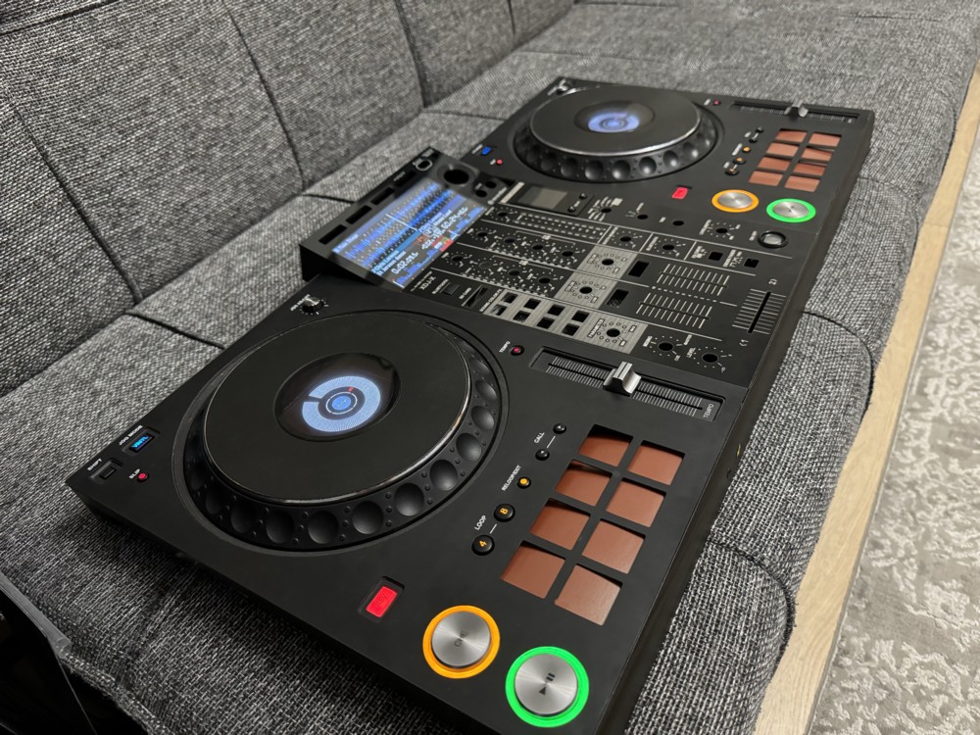
Photo/29.jpg
