djgreeb/XDJ-X/Photo/30.jpg

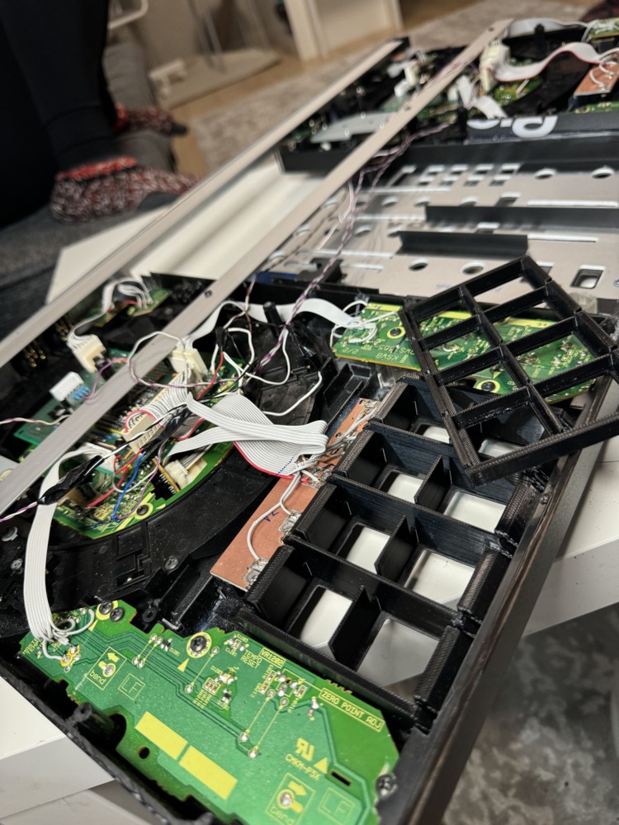
Photo/30.jpg
