djgreeb/XDJ-X/Photo/31.jpg

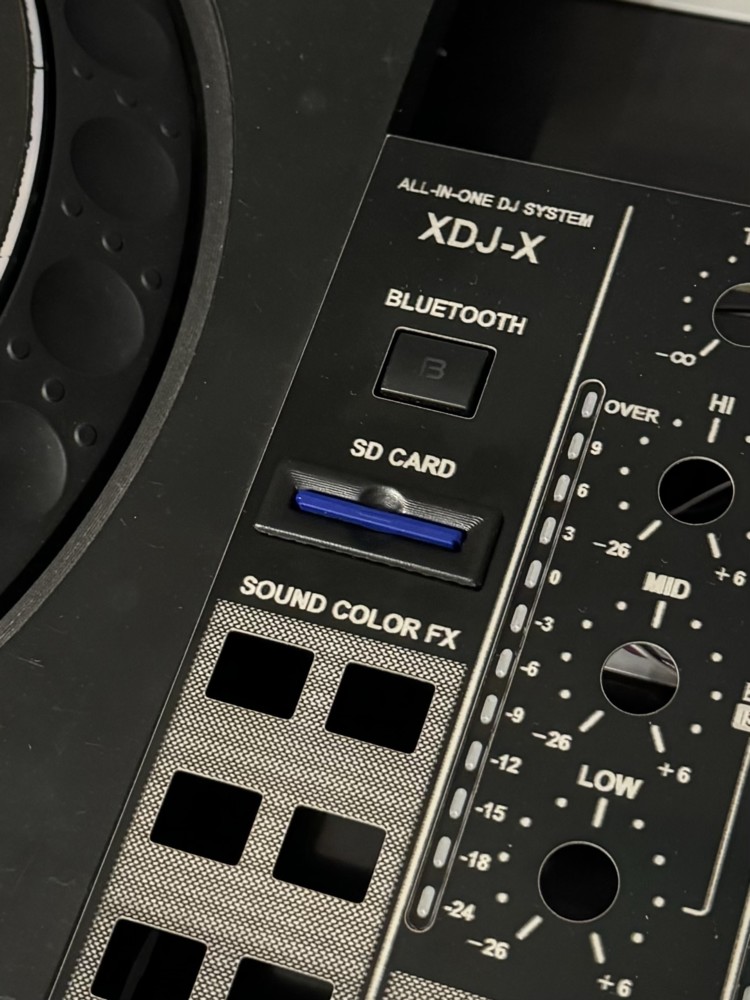
Photo/31.jpg
