djgreeb/XDJ-X/Photo/32.jpg

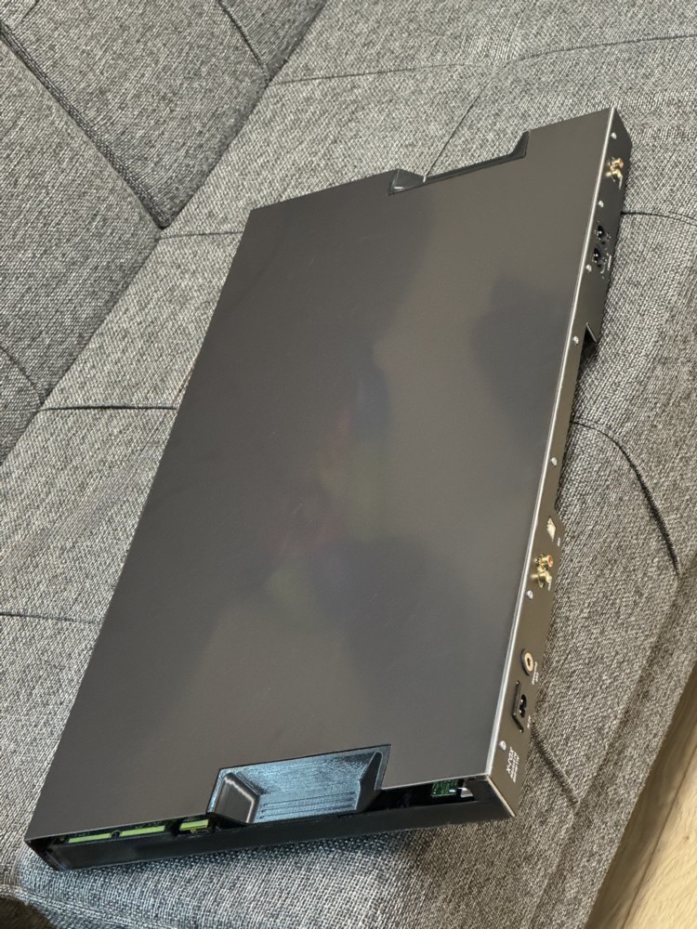
Photo/32.jpg
