djgreeb/XDJ-X/Photo/33.jpg

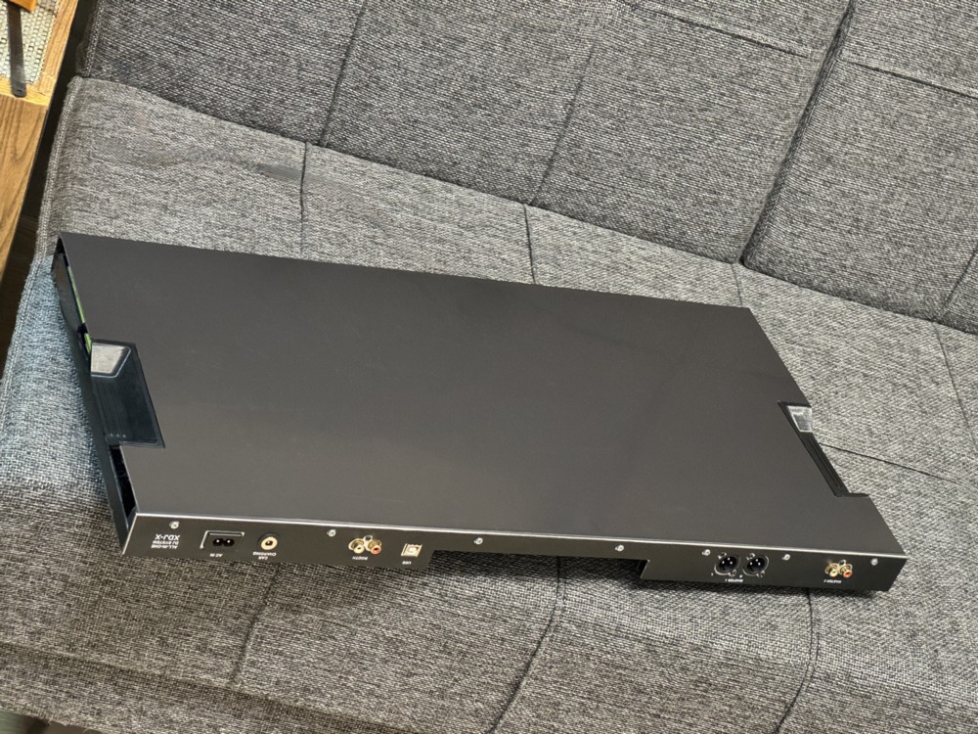
Photo/33.jpg
