djgreeb/XDJ-X/Photo/34.jpg

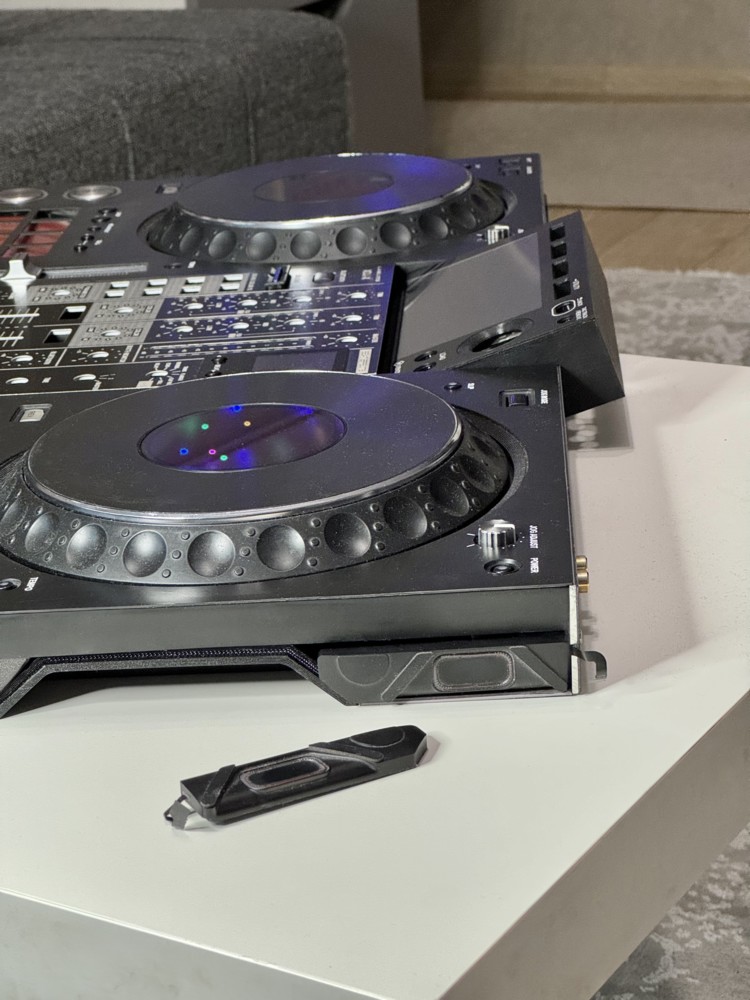
Photo/34.jpg
