djgreeb/XDJ-X/Photo/35.jpg

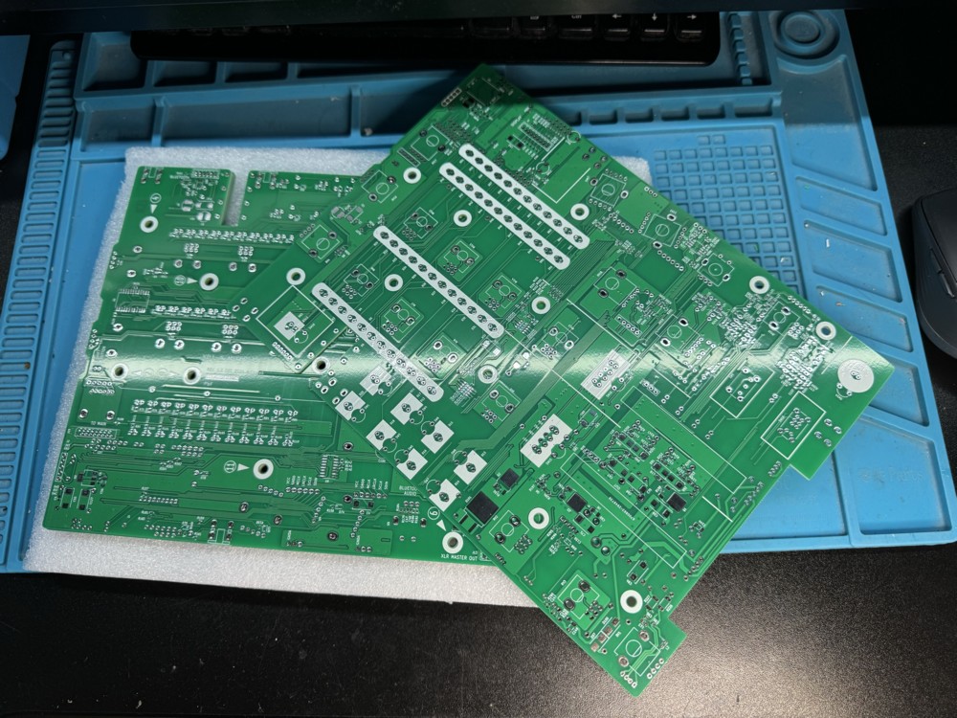
Photo/35.jpg
