djgreeb/XDJ-X/Photo/36.jpg

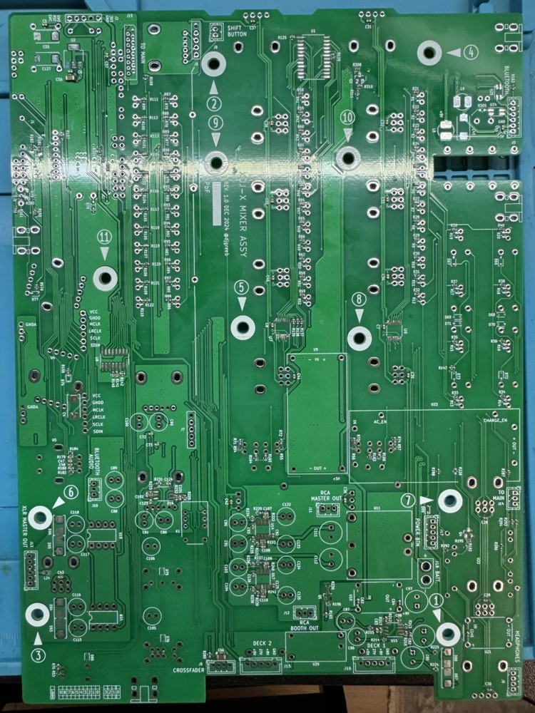
Photo/36.jpg
