djgreeb/XDJ-X/Photo/37.jpg

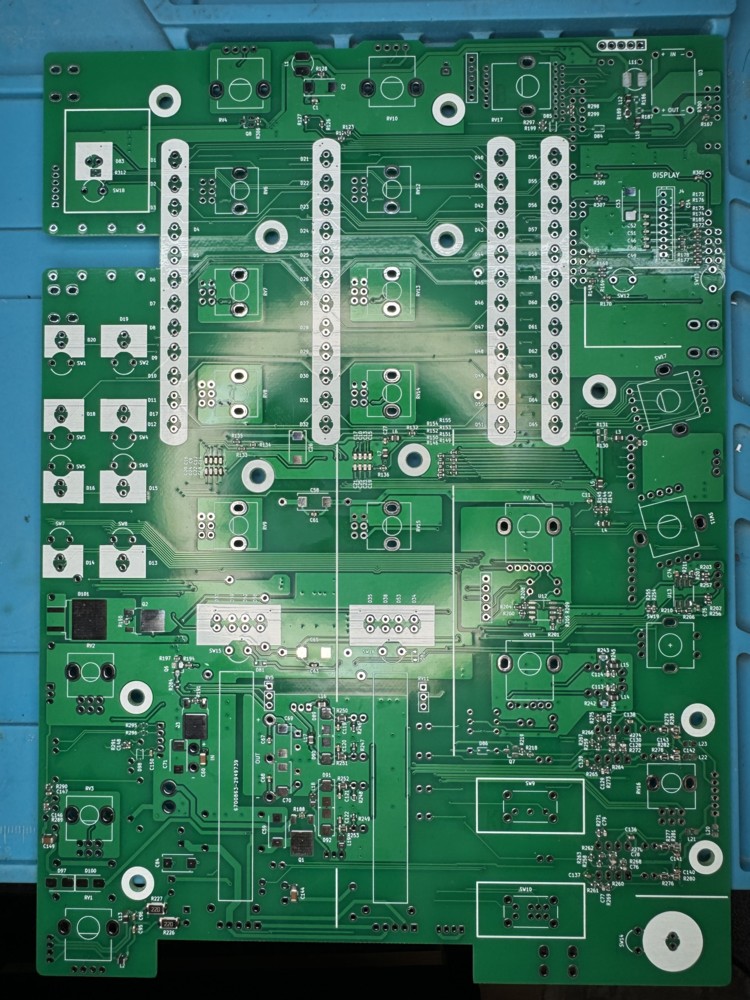
Photo/37.jpg
