djgreeb/XDJ-X/Photo/38.jpg

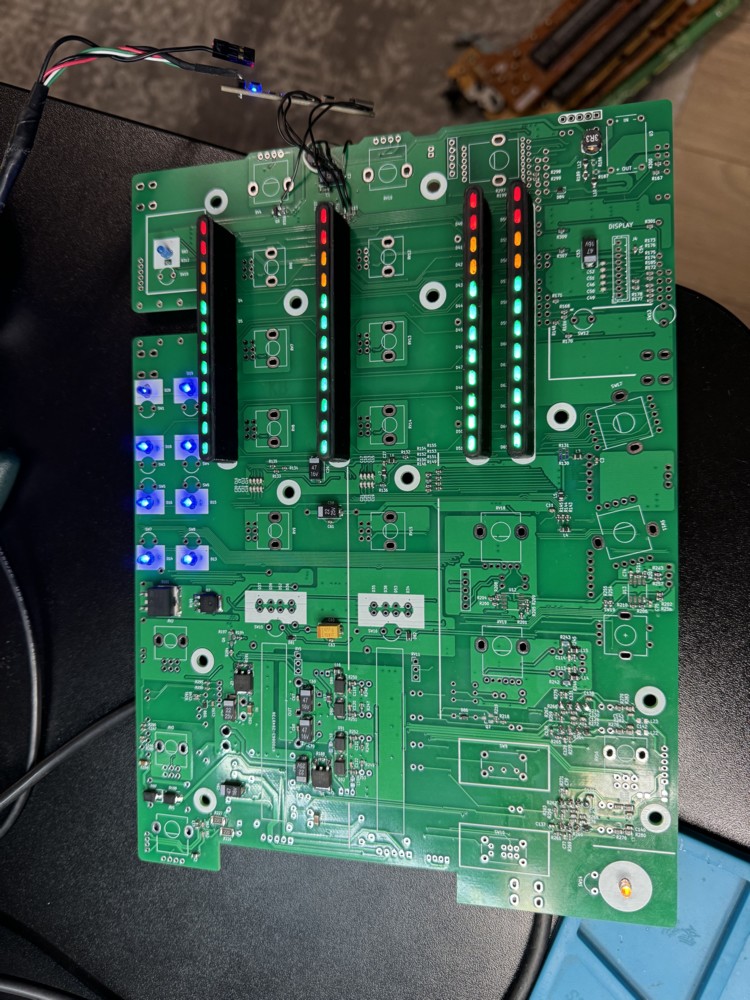
Photo/38.jpg
