djgreeb/XDJ-X/Photo/40.jpg

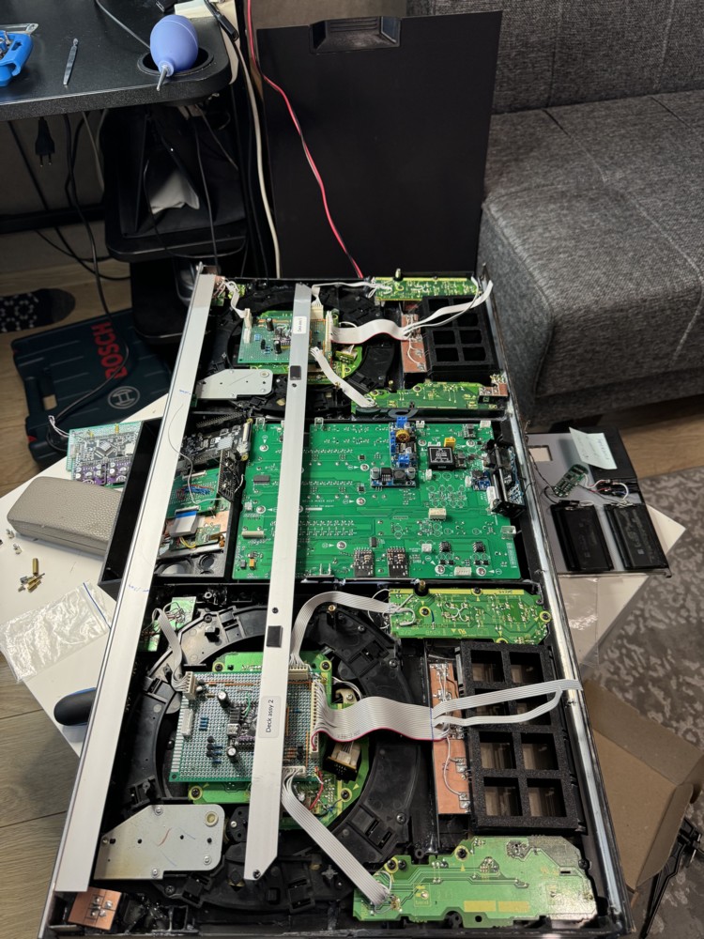
Photo/40.jpg
