djgreeb/XDJ-X/Photo/41.jpg

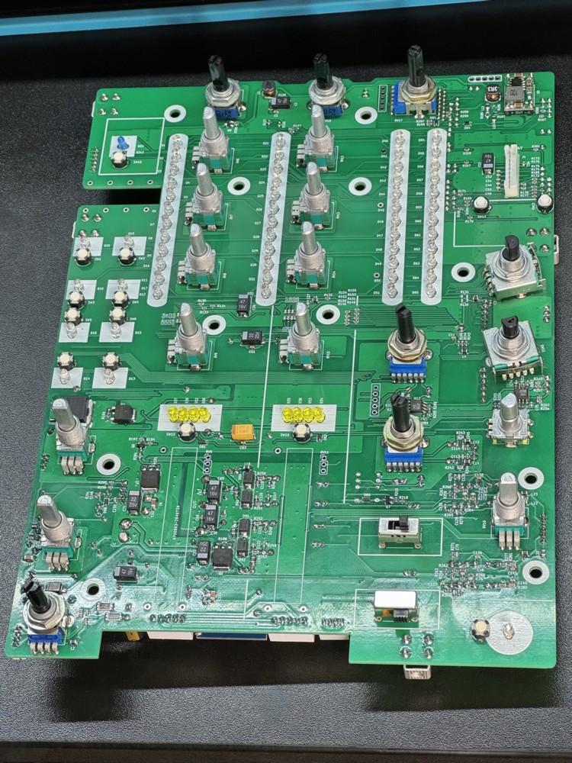
Photo/41.jpg
