djgreeb/XDJ-X/Photo/42.jpg

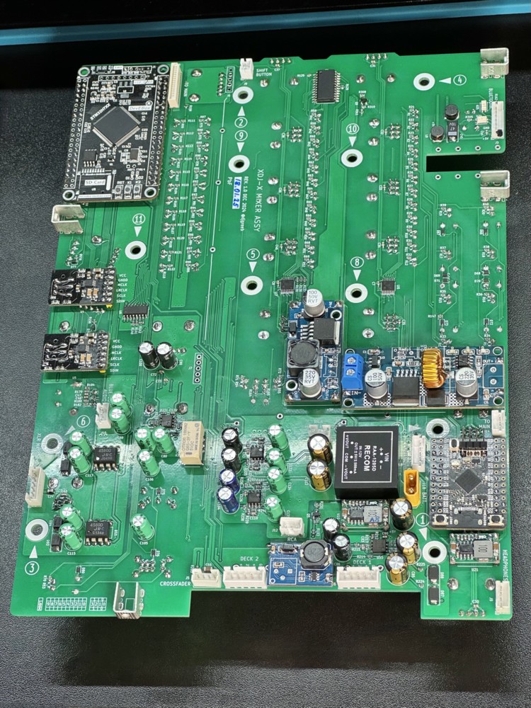
Photo/42.jpg
