djgreeb/XDJ-X/Photo/43.jpg

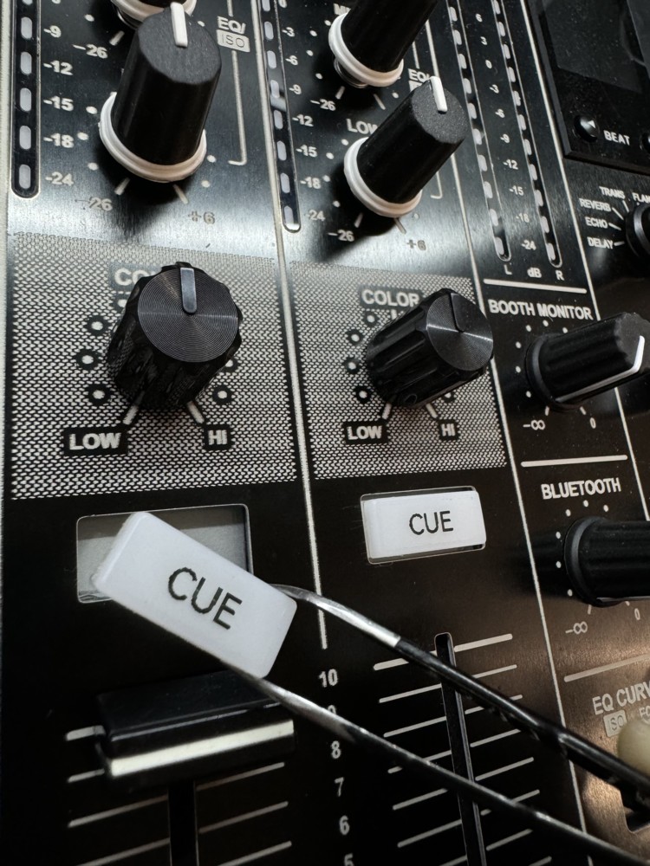
Photo/43.jpg
