djgreeb/XDJ-X/Photo/44.jpg

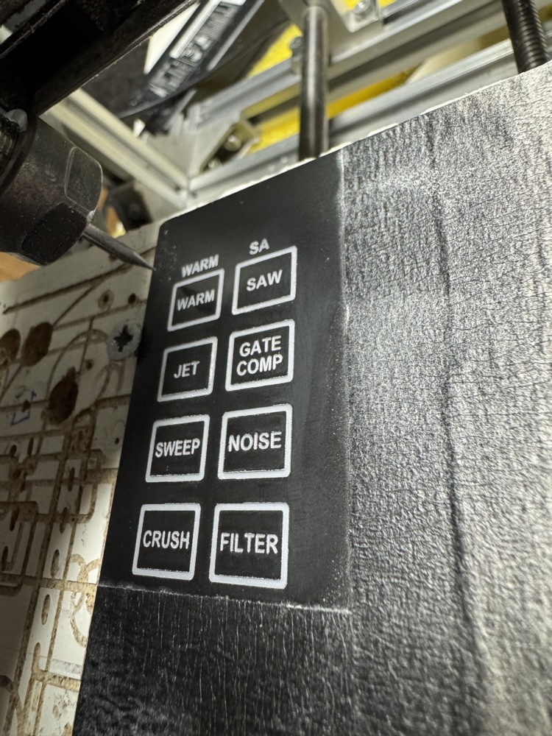
Photo/44.jpg
