djgreeb/XDJ-X/Photo/45.jpg

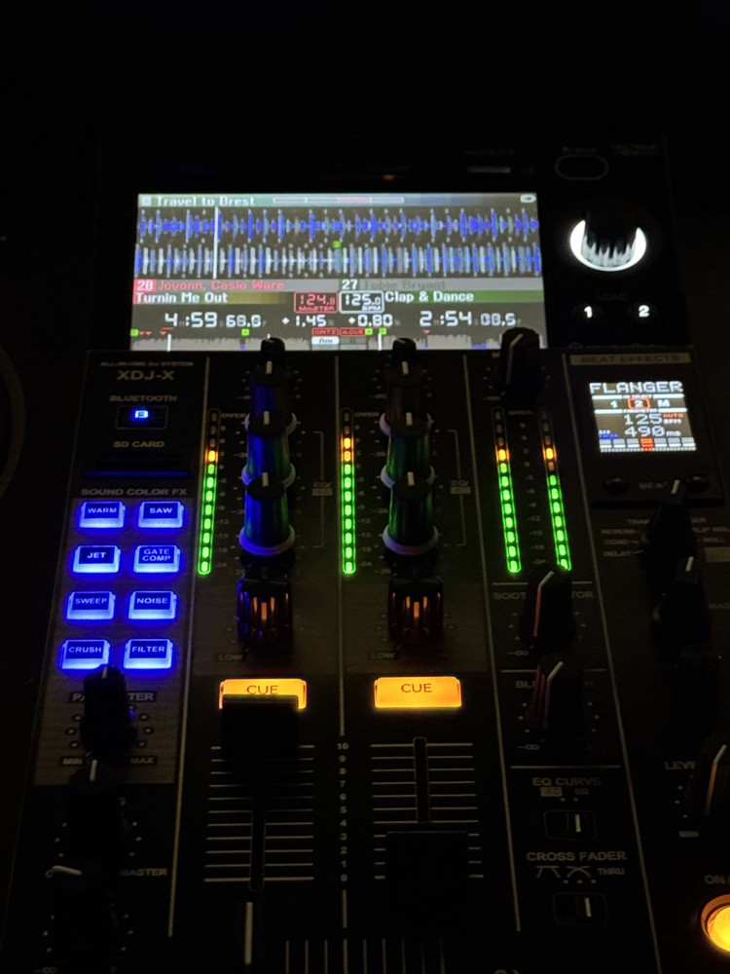
Photo/45.jpg
