djgreeb/XDJ-X/Photo/46.jpg

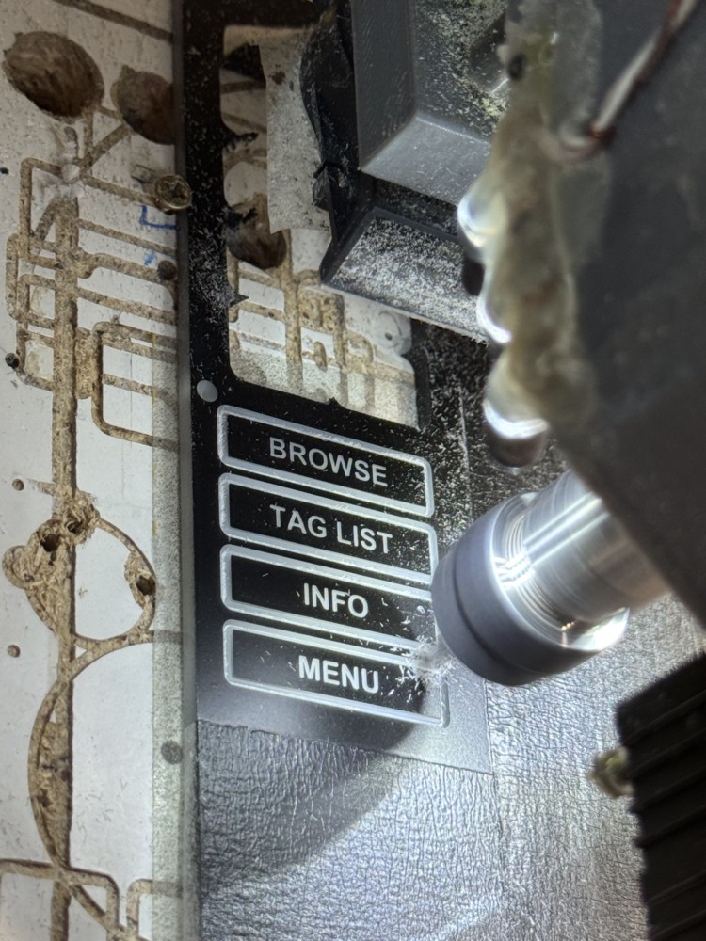
Photo/46.jpg
