djgreeb/XDJ-X/Photo/48.jpg

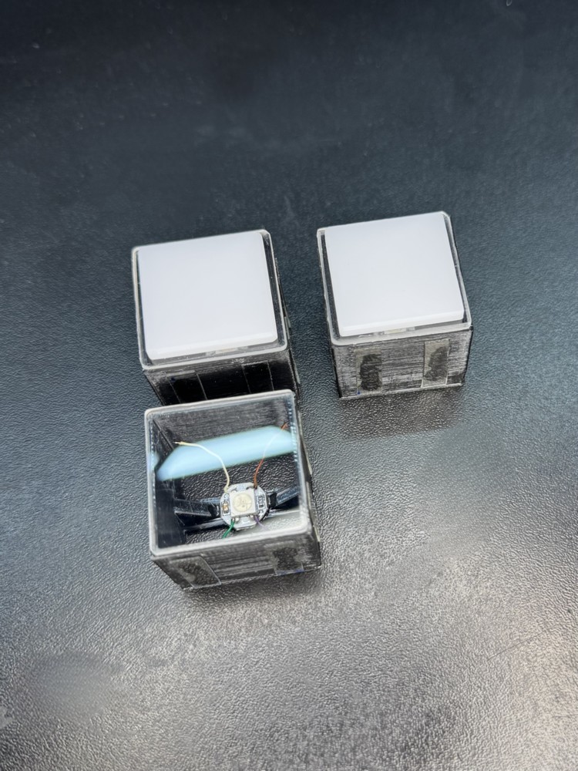
Photo/48.jpg
