djgreeb/XDJ-X/Photo/49.jpg

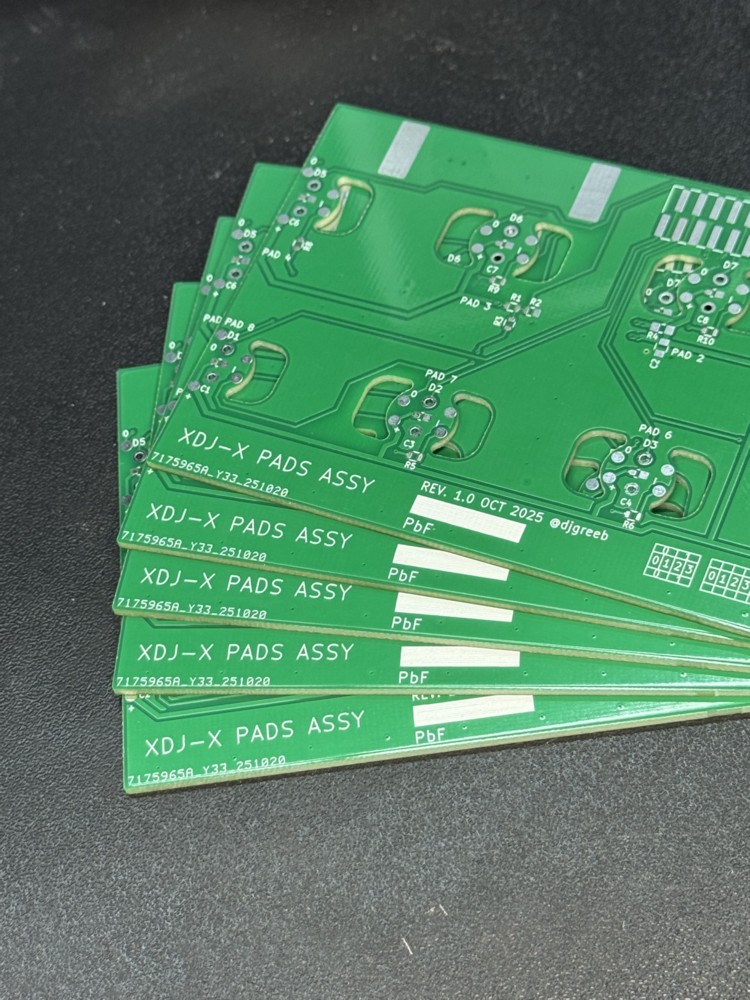
Photo/49.jpg
