djgreeb/XDJ-X/Photo/50.jpg

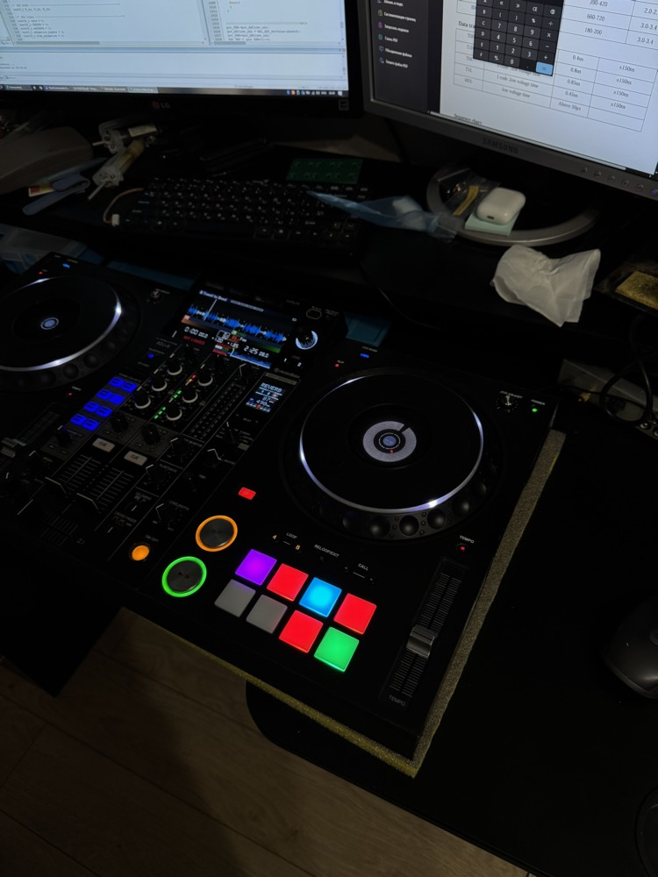
Photo/50.jpg
