djgreeb/XDJ-X/Photo/51.jpg

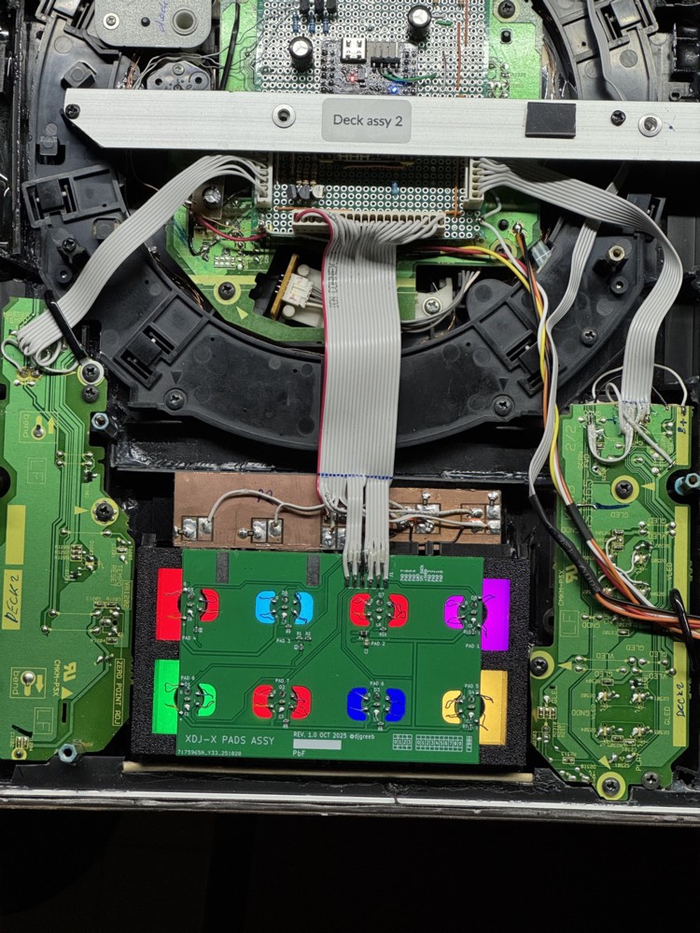
Photo/51.jpg
