djgreeb/XDJ-X/Photo/52.jpg

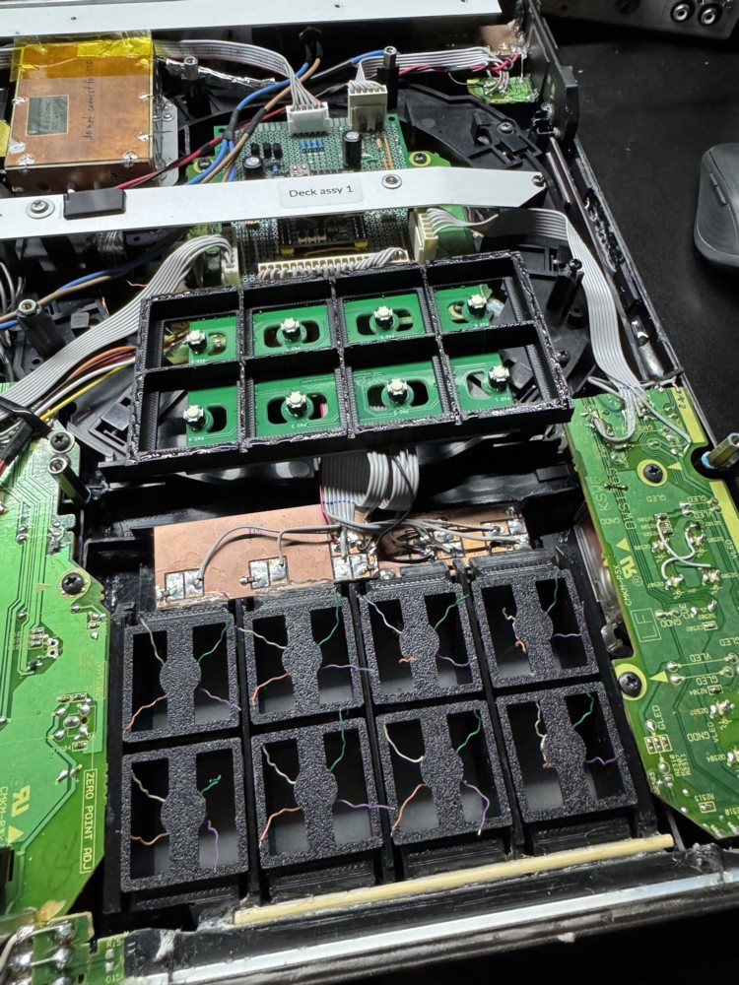
Photo/52.jpg
