djgreeb/XDJ-X/Photo/53.jpg

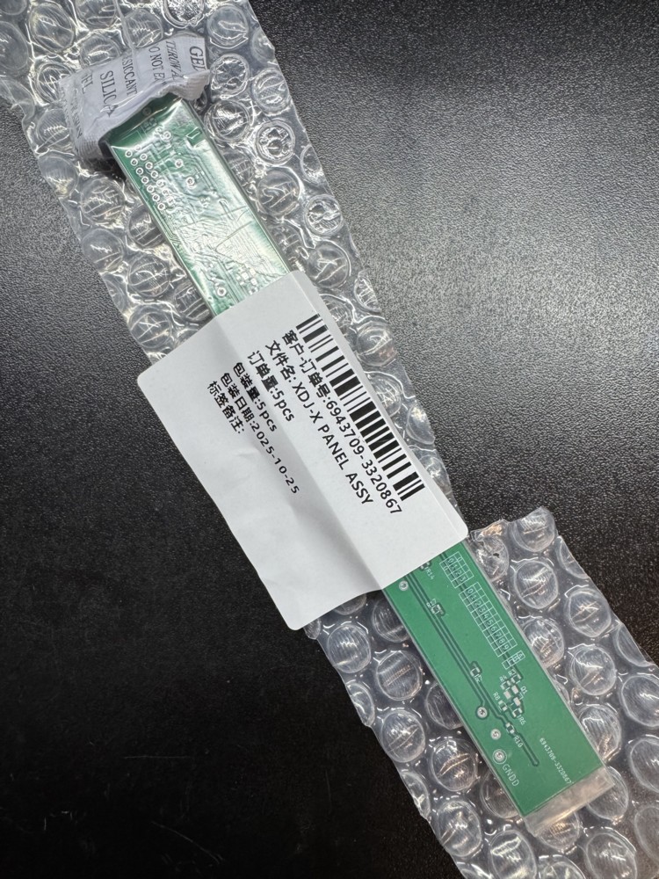
Photo/53.jpg
