djgreeb/XDJ-X/Photo/54.jpg

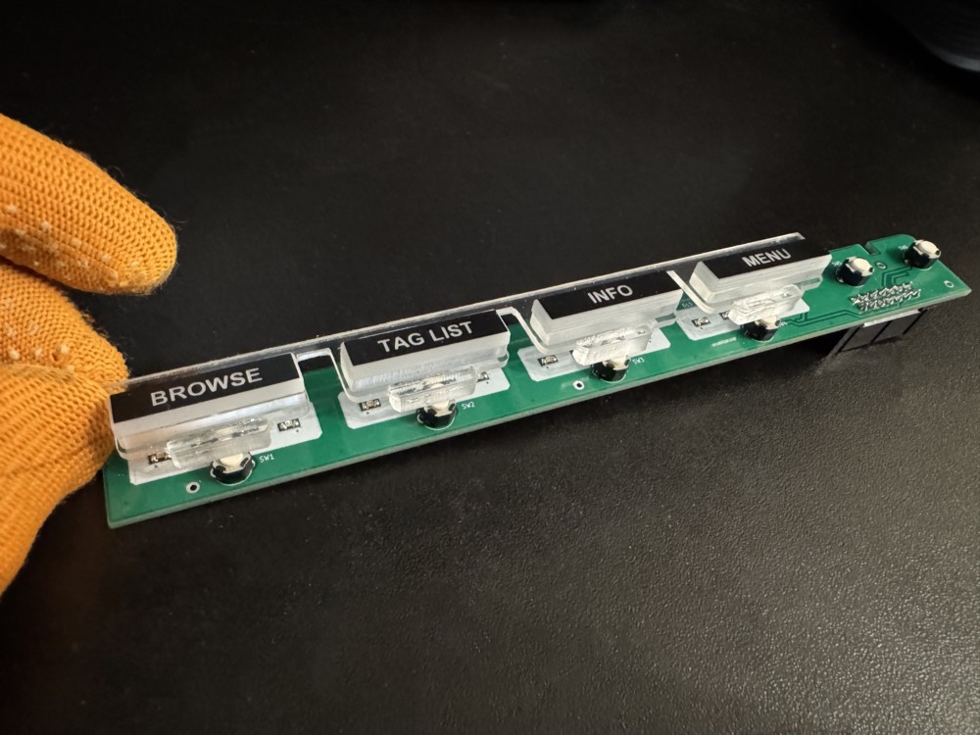
Photo/54.jpg
