djgreeb/XDJ-X/Photo/55.jpg

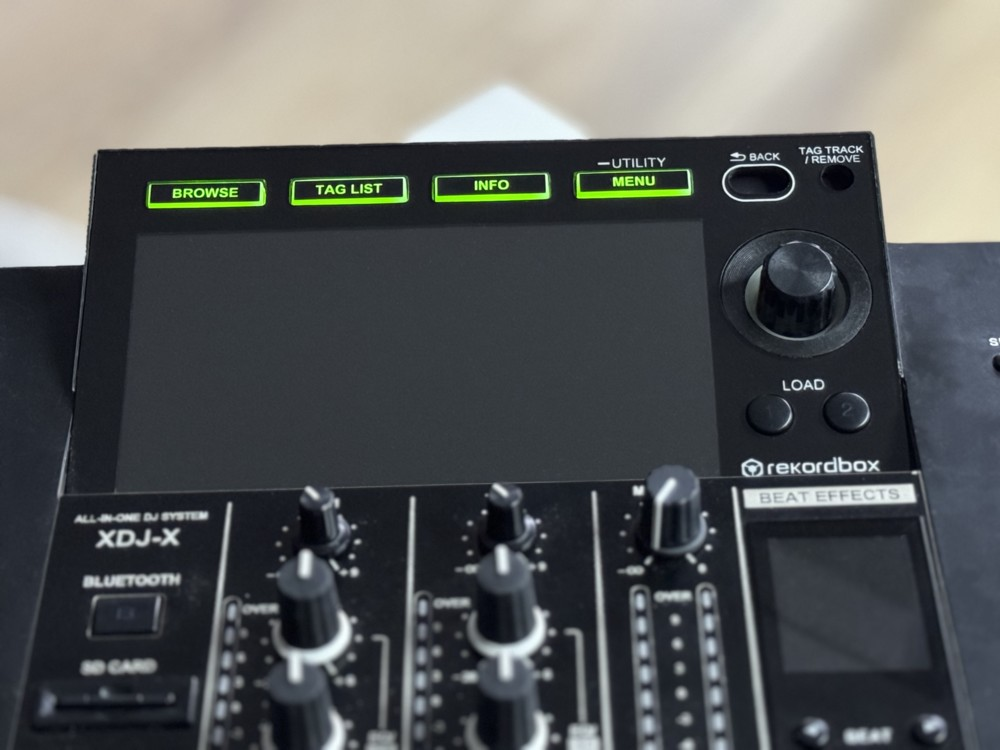
Photo/55.jpg
