djgreeb/XDJ-X/XDJ-X view.png

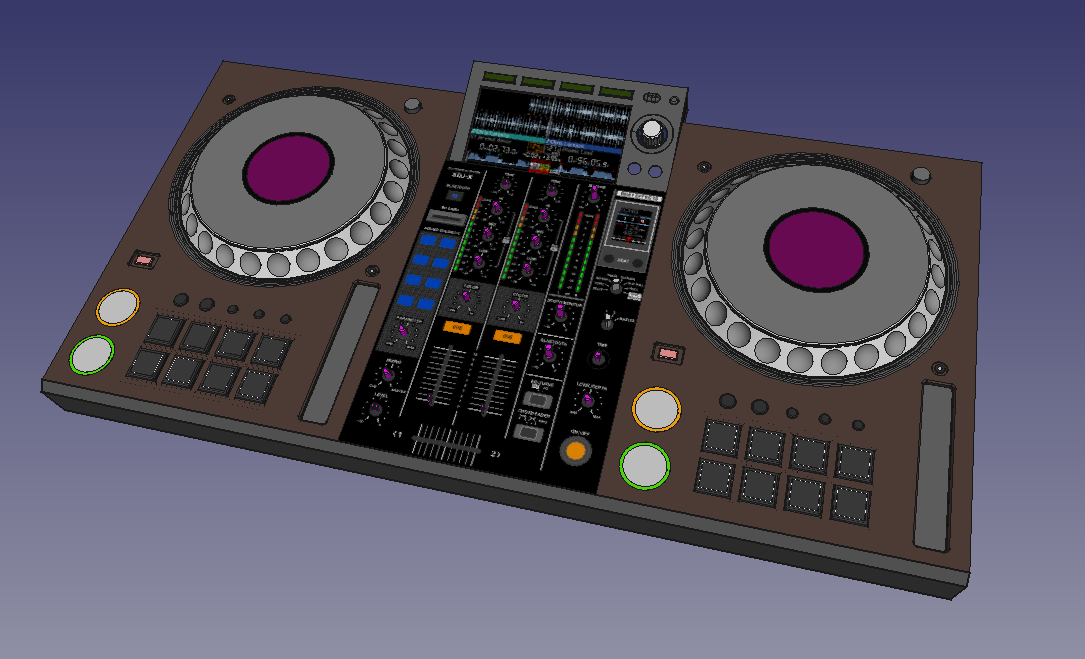
XDJ-X view.png
