djgreeb/XDJ-X/PADS 3D/PADS_DETAIL_2.stl

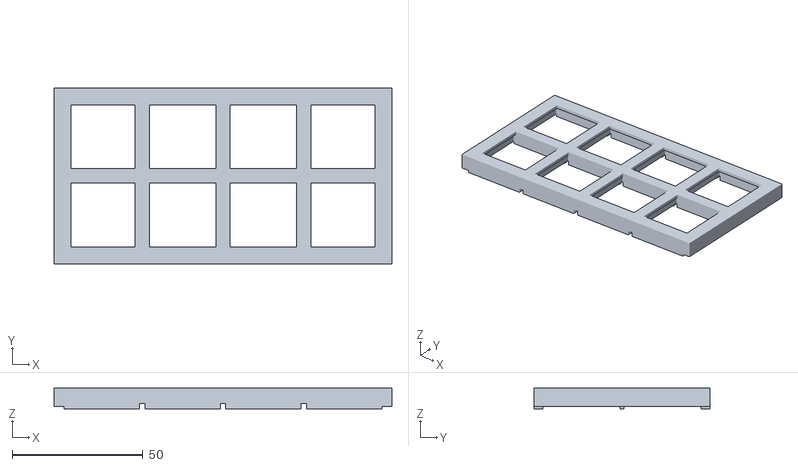
[picture p106: CAD file, 2025-03-18]
PADS 3D/PADS_DETAIL_2.stl
129.5 x 67.5 x 8.00
