djgreeb/XDJ-X/Mixer assy/3D/handler.FCStd

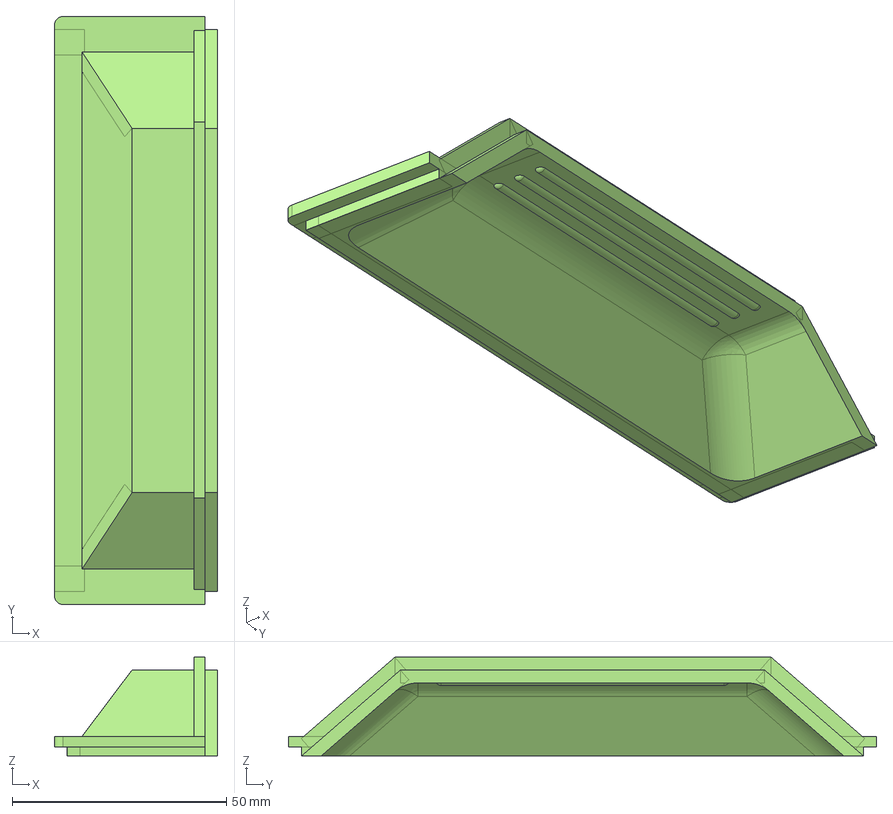
[picture p107: CAD file, 2025-03-18]
Mixer assy/3D/handler.FCStd
38.1 x 137.2 x 23.0 mm
