djgreeb/XDJ-X/Mixer assy/3D/pillar.FCStd

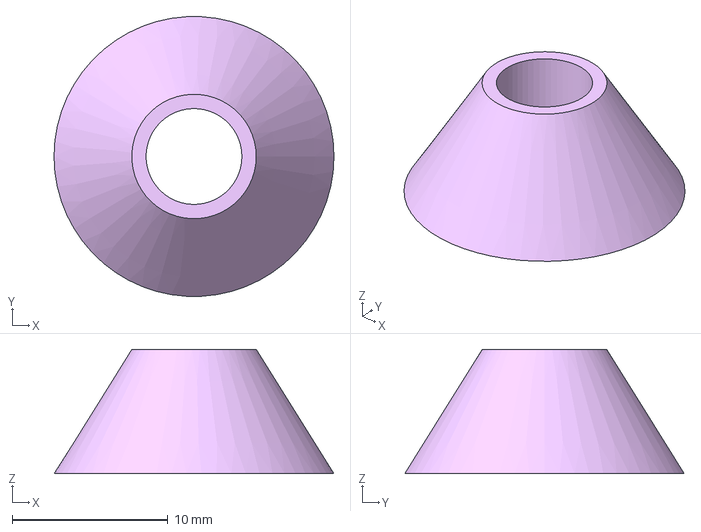
[picture p108: CAD file, 2025-03-18]
Mixer assy/3D/pillar.FCStd
18.0 x 18.0 x 8.00 mm
