djgreeb/XDJ-X/PADS 3D/PADS.FCStd

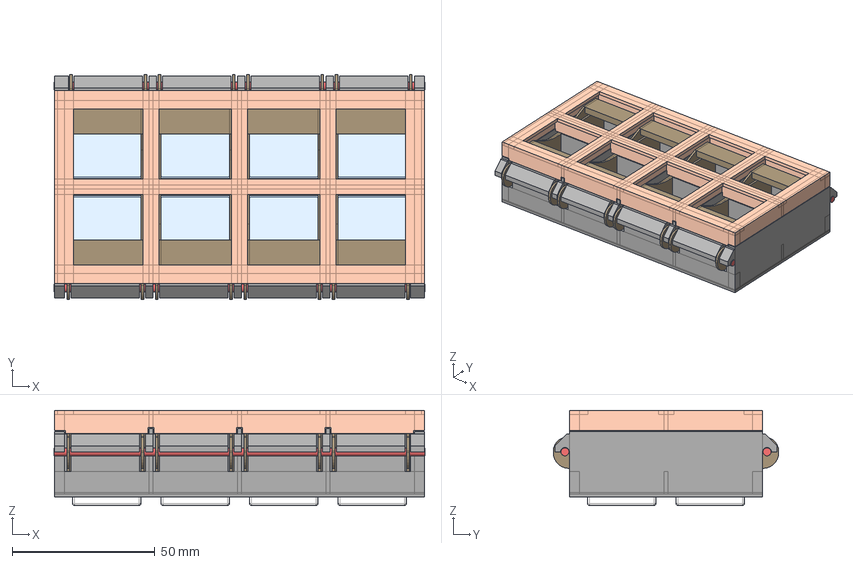
[picture p109: CAD file, 2025-03-18]
PADS 3D/PADS.FCStd
130.0 x 79.0 x 33.3 mm
plexipads_8
black_pads
detail_2
FDETAIL_1
Цилиндр004
Цилиндр005
hands-8
