djgreeb/XDJ-X/Mixer assy/FW_BACKUP/XDJX_MIXER_ASSY/Inc/encoder_handler.h

/////////////////////////////////////////////////////////////////////////////////////////////////
//	Encoder handler
//	product: XDJ-X mixer assy
//
//
//
//
//	Author: Anatska Andrei
//
/////////////////////////////////////////////////////////////////////////////////////////////////



//////////////////////////////////////////////////////////
//
//
//
void TIM8_UP_TIM13_IRQHandler(void)
	{

	
  HAL_TIM_IRQHandler(&htim8);
	}

	
	
////////////////////////////////////////////////////////////////////////////////////////////////////////////////////////
