djgreeb/XDJ-X/Power Manager/Src/main.c

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
/* Includes ------------------------------------------------------------------*/
#include "main.h"
#include "adc.h"
#include "usart.h"
#include "gpio.h"


/* USER CODE BEGIN PV */

////////////////////////////////////////////////////////////////////////////////////////
//
//
//
//
//		Generated with: STM32CubeMX 6.10.0
//		Firmware Package Name and Version STM32Cube FW_G4 V1.5.1
//
//
//
//
//
////////////////////////////////////////////////////////////////////////////////////////
//
//
//
//	ver. 0.17
//		- added all gpio
//		- added button and leds handler
//		-	added UART handler (need add UART interrupt and regenerate code)
//		-	added ADC process
//	ver. 0.18
//		- added gpio direct registers calling
//		-	improved USART1_IRQHandler
//	ver. 0.21
//		- fix quick blink period
//		- fix turn off after turn on bug
//	ver. 0.23
//		-	regenerate code
//		-	added UART IRQHandler
//	ver. 0.25
//		-	changed timings for button press and unpress
//	ver. 0.27
//		- uart speed up to 256000
//		-	main period changed 83,3Hz
//	ver. 0.29
//		- added % battery
//
//
//
////////////////////////////////////////////////////////////////////////////////////////

uint8_t fwver = 29;

#include "global_variables.h"

/* USER CODE END PV */

void SystemClock_Config(void);
/**
  * @brief  The application entry point.
  * @retval int
  */
int main(void)
{
  /* MCU Configuration--------------------------------------------------------*/

  /* Reset of all peripherals, Initializes the Flash interface and the Systick. */
  HAL_Init();

  /* Configure the system clock */
  SystemClock_Config();

  /* Initialize all configured peripherals */
  MX_GPIO_Init();
  MX_ADC1_Init();
  MX_USART1_UART_Init();
  /* USER CODE BEGIN 2 */
	HAL_GPIO_WritePin(GPIOB, LED_WHITE_Pin|LED_GREEN_Pin, GPIO_PIN_SET);
	USART1->CR1 |= USART_CR1_RXNEIE; //interrupt for a RX enable
	HAL_Delay(300);
	HAL_ADC_Start(&hadc1);
  /* USER CODE END 2 */

  /* Infinite loop */
  /* USER CODE BEGIN WHILE */
  while (1)
  {
	HAL_Delay(12);			//create 83,3Hz period			
		
	if(HAL_GPIO_ReadPin(BUTTON_IN_GPIO_Port, BUTTON_IN_Pin)==0 && BUTTON_pressed==0)
		{		
		LED_W_OFF;
		LED_G_OFF;		
		tim_button_press = 0;	
		TX_DATA[1] = B_PRESS;	
		HAL_UART_Transmit(&huart1, TX_DATA, 2, 5);		
		BUTTON_pressed = 1;	
		}	
	else if(HAL_GPIO_ReadPin(BUTTON_IN_GPIO_Port, BUTTON_IN_Pin)==0 && BUTTON_pressed==1)
		{
		if(tim_button_press<0xFFFF)
			{
			tim_button_press++;
			if(XDJ_POWER_ON==0)
				{
				if(tim_button_press==2)	// 0,024 sec pressed
					{	
					HAL_GPIO_WritePin(PON_GPIO_Port, PON_Pin, GPIO_PIN_SET);	
					LED_W_OFF;
					LED_G_ON;	
					need_change_status_power = 1;	
					}					
				}
			else
				{
				if(tim_button_press==250)	//3 sec pressed (send turn off command to main assy, waitig answer)
					{	
					TX_DATA[1] = T_OFF;	
					HAL_UART_Transmit(&huart1, TX_DATA, 2, 5);						
					LED_W_OFF;
					LED_G_OFF;
					quick_blink = 1;	
					timeout_power = 0;	
					}		
				}				
			}
		}		
	else if(HAL_GPIO_ReadPin(BUTTON_IN_GPIO_Port, BUTTON_IN_Pin)==1 && BUTTON_pressed==1)
		{
		timeout_unpress++;	
		if(timeout_unpress>3)
			{
			if(need_change_status_power>0)
				{
				XDJ_POWER_ON = 1;		
				need_change_status_power = 0;	
				}
			if(tim_button_press<83)  //short press
				{
				TX_DATA[1] = B_UNPRESS;	
				HAL_UART_Transmit(&huart1, TX_DATA, 2, 5);		
				}			
			tim_button_press = 0xFFFF;	
			timeout_unpress = 0;	
			BUTTON_pressed = 0;	
			}				
		}		
	
	if(quick_blink==0)
		{
		if(XDJ_POWER_ON==0 && BUTTON_pressed==0)
			{
			if(HAL_GPIO_ReadPin(GPIOB, ACIN_EN_Pin)==1)
				{
				if(HAL_GPIO_ReadPin(GPIOB, CHARGE_EN_Pin)==0)			//CHARGE enable	
					{
					TX_DATA[0] = AC_CHARGE;	
					blink_tim++;							
					if(blink_tim<64 || (blink_tim>128 && blink_tim<192))	
						{
						LED_W_OFF;
						LED_G_OFF;		
						}
					else
						{	
						LED_W_ON;
						LED_G_OFF;		
						}					
					}
				else			//charge disable - FULL
					{
					TX_DATA[0] = AC_FULL;	
					LED_W_ON;
					LED_G_OFF;	
					}
				}
			else
				{
				TX_DATA[0] = AC_DSBL;	
				LED_W_OFF;
				LED_G_OFF;	
				}			
			}
		else if(XDJ_POWER_ON==1 && BUTTON_pressed==0)
			{
			if(HAL_GPIO_ReadPin(GPIOB, ACIN_EN_Pin)==1)
				{
				if(HAL_GPIO_ReadPin(GPIOB, CHARGE_EN_Pin)==0)			//CHARGE enable	
					{
					TX_DATA[0] = AC_CHARGE;	
					blink_tim++;	
					if(blink_tim<64 || (blink_tim>128 && blink_tim<192))	
						{
						LED_W_OFF;
						LED_G_ON;		
						}
					else
						{	
						LED_W_ON;
						LED_G_OFF;		
						}					
					}
				else			//charge disable - FULL
					{
					TX_DATA[0] = AC_FULL;	
					LED_W_OFF;
					LED_G_ON;	
					}
				}
			else
				{
				TX_DATA[0] = AC_DSBL;	
				LED_W_OFF;
				LED_G_ON;		
				}		
			}	
		if(previous_status!=TX_DATA[0])
			{
			if(XDJ_POWER_ON==1)
				{
				TX_DATA[1] = batt_prcntg;		//battery precentage	
				HAL_UART_Transmit(&huart1, TX_DATA, 2, 5);		
				}	
			previous_status = TX_DATA[0];	
			}
		}
	else				//turn off sequence (waitig answer form main assy) 
		{
		if(timeout_power<1665)
			{
			timeout_power++;
			if(timeout_power==1664)			//20 sec pressed (hardware turn off)
				{
				quick_blink = 0;		
				HAL_GPIO_WritePin(PON_GPIO_Port, PON_Pin, GPIO_PIN_RESET);	
				LED_W_OFF;
				LED_G_OFF;
				XDJ_POWER_ON = 0;		
				timeout_power = 0xFFFF;	
				}				
			}			
		blink_tim++;
		LED_W_OFF;	
		if((blink_tim%8)==0)	
			{
			LED_G_ON;		
			}
		else if((blink_tim%8)==4)	
			{
			LED_G_OFF;		
			}
		}		

	if(usart_new_data)									////////////////////////usart data handler
		{
		HAL_Delay(2);	
		if((U_RX_DATA[0]==AC_DSBL) && (U_RX_DATA[1]==T_OFF))				//turn off command
			{							
			quick_blink = 0;
			HAL_GPIO_WritePin(PON_GPIO_Port, PON_Pin, GPIO_PIN_RESET);	
			LED_W_OFF;
			LED_G_OFF;
			XDJ_POWER_ON = 0;			
			}
		else if((U_RX_DATA[0]==AC_DSBL) && (U_RX_DATA[1]==BATT_RQ))				//ADC batt request
			{
			TX_DATA[1] = batt_prcntg;		//battery precentage	
			HAL_UART_Transmit(&huart1, TX_DATA, 2, 5);	
			}
		else if((U_RX_DATA[0]==AC_DSBL) && (U_RX_DATA[1]==FW_RQ))				//firmware version request
			{
			TX_DATA[1] = fwver & 0x80;
			HAL_UART_Transmit(&huart1, TX_DATA, 2, 5);	
			}
		usart_new_data = 0;		
		}
		
	/////////////////////////////ADC process
	//	12.392 - 2618
	//	11.498 - 2418
	//	9.898	 - 2070		- min	
	//	12.605 - 2658		- max
	ADC_TEMP = HAL_ADC_GetValue(&hadc1);
	DATAV_TEMP*=7;	
	DATAV_TEMP+=ADC_TEMP;	
	DATAV_TEMP+=4;	
	DATAV_TEMP>>=3;
	ADC_TEMP = DATAV_TEMP;	
	if(ADC_TEMP>2069)
		{
		ADC_TEMP-=2070;	
		ADC_TEMP*=11146;	
		ADC_TEMP>>=16;	
		batt_prcntg = ADC_TEMP;
		if(batt_prcntg>100)
			{
			batt_prcntg = 100;	
			}				
		}		
	else
		{
		batt_prcntg = 0;	
		}		
		
	if(previous_batt_prcntg!=batt_prcntg)			//forceble tx batt prcntg to main assy
		{	
		if((HAL_GetTick() - adc_timeout)>1000)
			{
			if(XDJ_POWER_ON==1)
				{
				TX_DATA[1] = batt_prcntg;		//battery precentage	
				HAL_UART_Transmit(&huart1, TX_DATA, 2, 5);				
				}				
			adc_timeout = HAL_GetTick();	
			previous_batt_prcntg = batt_prcntg;	
			}				
		}
	HAL_ADC_Start(&hadc1);
		
		
		
    /* USER CODE END WHILE */

    /* USER CODE BEGIN 3 */
  }
  /* USER CODE END 3 */
}

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
/* USER CODE BEGIN 4 */


/////////////////////////////////////////////////////
//
//		UART handler
//
//
void USART1_IRQHandler(void)
	{
	uint8_t USART_RX_B;	
	if(USART1->ISR & USART_ISR_RXNE)		//have a new data
		{
		USART_RX_B = (USART1->RDR);	
		if(((HAL_GetTick() - usart_timeout)>120))
			{	
			if(USART_RX_B==AC_DSBL)
				{
				usart_data_cnt = 0;
				U_RX_DATA[0] = USART_RX_B;					
				}
			else
				{
				usart_data_cnt = 0xFF;	
				}
			}
		else
			{
			if(usart_data_cnt<4)	
				{
				usart_data_cnt++;	
				U_RX_DATA[usart_data_cnt] = USART_RX_B;
				usart_new_data = 1;	
				}
			}
		usart_timeout = HAL_GetTick(); 			
		}
  HAL_UART_IRQHandler(&huart1);
	}		



/* USER CODE END 4 */
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
