djgreeb/XDJ-X/FW_BACKUP/XDJX/Drivers/LCD/CWX3970.c

//////////////////////////////////////////////////////////////////////////////////////
//
//	CWX3970 Display driver
//	
// 
//
//

/* Includes ------------------------------------------------------------------*/
#include "CWX3970.h"
#include "../../../Utilities/Fonts/fonts.h"
#include "../../../Utilities/Fonts/font15P.c"
#include "../../../Utilities/Fonts/fontBMP.c"
#include "../../../Utilities/Fonts/font14D.c"
#include "../../../Utilities/Fonts/font18D.c"
#include "../../../Utilities/Fonts/font9D.c"
#include "../../../Utilities/Fonts/font7W.c"
#include "main.h"

#define  CWX3970_WIDTH    ((uint16_t)480)          /* LCD PIXEL WIDTH            */
#define  CWX3970_HEIGHT   ((uint16_t)233)          /* LCD PIXEL HEIGHT           */
#define  CWX3970_HSYNC    ((uint16_t)94)   /* Horizontal synchronization */
#define  CWX3970_HBP      ((uint16_t)6)   /* Horizontal back porch      */
#define  CWX3970_HFP      ((uint16_t)41)   /* Horizontal front porch     */
#define  CWX3970_VSYNC    ((uint16_t)17)   /* Vertical synchronization   */
#define  CWX3970_VBP      ((uint16_t)2)    /* Vertical back porch        */
#define  CWX3970_VFP      ((uint16_t)3)    /* Vertical front porch       */

uint8_t TRANSPARENT_MODE_ENABLE = 0;

const uint8_t width15P[242]={
4,
2,
5,
10,
5,
11,
9,
2,
4,
4,
8,
5,
2,
4,
2,
10,
7,	
4,
7,
7,
7,
7,
7,
7,
7,
7,
2,
2,
12,
5,
13,
8,
10,
9,
9,
9,
9,
8,
8,
9,
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
0,	//none symbol
///////
9,			//A rus
9,
9,			//B rus
8,
10,
8,		//E rus
12,
9,
9,
8,
9,		//K rus
9,
10,
8,
9,
8,
9,
9,		//C rus
8,
8,
10,
9,		//X
9,
8,
10,
11,
11,
13,
9,
9,
13,
9,
7,	//a rus
7,
7,
6,
9,
7,
10,
7,
7,
7,
7,
7,
8,
7,
7,
7,
0,
0,
0,
0,
0,
0,
0,
0,
0,
0,
0,
0,
0,
0,
0,
0,
0,
0,
0,
0,
0,
0,
0,
0,
0,
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
7,		//p rus
7,
6,
7,
10,		//f rus
7,
8,
7,
10,
11,
9,
10,
7,
7,
10,
7,
7,
7,
0,
0,
0,
0,
0,
0,
0,
0,
0,
0,
0,
0,
0,
0,
0,
0,
0,
0,
0,
0,
0,
0,
0,
0,
0,
0,
0,
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


const uint8_t width7W[95]={
3,
2,
5,
5,		//#
6,
0,
0,
2,
3,
3,
0,
6,
2,
6,		//-
2,
4,
7,	//0
4,	//1
6,
7,
7,
7,
7,
7,
7,
7,
2,	//:
2,
0,
5,		//=
0,
0,
0,
6,	//A
6,	//B
6,
6,
5,
5,	//F
6,
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
}; 

#define POLY_X(Z)              ((int32_t)((Points + Z)->X))
#define POLY_Y(Z)              ((int32_t)((Points + Z)->Y))      

#define ABS(X)  ((X) > 0 ? (X) : -(X))      

static LTDC_HandleTypeDef  hLtdcHandler;
static DMA2D_HandleTypeDef hDma2dHandler;

/* Default LCD configuration with LCD Layer 1 */
//static uint32_t            ActiveLayer = 0;
static LCD_DrawPropTypeDef DrawProp[MAX_LAYER_NUMBER];

static void DrawChar(uint16_t Xpos, uint16_t Ypos, const uint8_t *c);
void FillTriangle(uint16_t x1, uint16_t x2, uint16_t x3, uint16_t y1, uint16_t y2, uint16_t y3);
static void LL_FillBuffer(uint32_t LayerIndex, void *pDst, uint32_t xSize, uint32_t ySize, uint32_t OffLine, uint16_t ColorIndex);


/**
  * @brief  Initializes the LCD.
  * @retval LCD state
  */
uint8_t BSP_LCD_Init(void)
{    
  /* Timing Configuration */
  hLtdcHandler.Init.HorizontalSync = (CWX3970_HSYNC - 1);
  hLtdcHandler.Init.VerticalSync = (CWX3970_VSYNC - 1);
  hLtdcHandler.Init.AccumulatedHBP = (CWX3970_HSYNC + CWX3970_HBP - 1);
  hLtdcHandler.Init.AccumulatedVBP = (CWX3970_VSYNC + CWX3970_VBP - 1);
  hLtdcHandler.Init.AccumulatedActiveH = (CWX3970_HEIGHT + CWX3970_VSYNC + CWX3970_VBP - 1);
  hLtdcHandler.Init.AccumulatedActiveW = (CWX3970_WIDTH + CWX3970_HSYNC + CWX3970_HBP - 1);
  hLtdcHandler.Init.TotalHeigh = (CWX3970_HEIGHT + CWX3970_VSYNC + CWX3970_VBP + CWX3970_VFP - 1);
  hLtdcHandler.Init.TotalWidth = (CWX3970_WIDTH + CWX3970_HSYNC + CWX3970_HBP + CWX3970_HFP - 1);
  
  /* LCD clock configuration */
  //BSP_LCD_ClockConfig(&hLtdcHandler, NULL);

  /* Initialize the LCD pixel width and pixel height */
  hLtdcHandler.LayerCfg->ImageWidth  = CWX3970_WIDTH;
  hLtdcHandler.LayerCfg->ImageHeight = CWX3970_HEIGHT;

  /* Background value */
  hLtdcHandler.Init.Backcolor.Blue = 0;
  hLtdcHandler.Init.Backcolor.Green = 0;
  hLtdcHandler.Init.Backcolor.Red = 0;
  
  /* Polarity */
  hLtdcHandler.Init.HSPolarity = LTDC_HSPOLARITY_AL;
  hLtdcHandler.Init.VSPolarity = LTDC_VSPOLARITY_AL; 
  hLtdcHandler.Init.DEPolarity = LTDC_DEPOLARITY_AL;  
  hLtdcHandler.Init.PCPolarity = LTDC_PCPOLARITY_IPC;		//LTDC_PCPOLARITY_IIPC;
  hLtdcHandler.Instance = LTDC;

  if(HAL_LTDC_GetState(&hLtdcHandler) == HAL_LTDC_STATE_RESET)
  {
    /* Initialize the LCD Msp: this __weak function can be rewritten by the application */
    BSP_LCD_MspInit(&hLtdcHandler, NULL);
  }
  HAL_LTDC_Init(&hLtdcHandler);
    
  /* Initialize the font */
  BSP_LCD_SetFont(&LCD_DEFAULT_FONT);
  return LCD_OK;
}

uint32_t BSP_LCD_GetXSize(void)
	{
  return hLtdcHandler.LayerCfg[ActiveLayer].ImageWidth;
	}

uint32_t BSP_LCD_GetYSize(void)
	{
  return hLtdcHandler.LayerCfg[ActiveLayer].ImageHeight;	
	}


void BSP_LCD_SetXSize(uint32_t imageWidthPixels)
	{
  hLtdcHandler.LayerCfg[ActiveLayer].ImageWidth = imageWidthPixels;
	}


void BSP_LCD_SetYSize(uint32_t imageHeightPixels)
	{
  hLtdcHandler.LayerCfg[ActiveLayer].ImageHeight = imageHeightPixels;
	}


void BSP_LCD_LayerDefaultInit(uint16_t LayerIndex, uint32_t FB_Address)
	{     
  LCD_LayerCfgTypeDef  layer_cfg;

  /* Layer Init */
  layer_cfg.WindowX0 = 0;
  layer_cfg.WindowX1 = 480;
  layer_cfg.WindowY0 = 0;
  layer_cfg.WindowY1 = 233; 
  layer_cfg.PixelFormat = LTDC_PIXEL_FORMAT_ARGB1555;
  layer_cfg.FBStartAdress = FB_Address;
  layer_cfg.Alpha = 255;
  layer_cfg.Alpha0 = 0;
  layer_cfg.Backcolor.Blue = 0;
  layer_cfg.Backcolor.Green = 0;
  layer_cfg.Backcolor.Red = 0;
  layer_cfg.BlendingFactor1 = LTDC_BLENDING_FACTOR1_PAxCA;
  layer_cfg.BlendingFactor2 = LTDC_BLENDING_FACTOR2_PAxCA;
  layer_cfg.ImageWidth = 480;
  layer_cfg.ImageHeight = 233;
  
  HAL_LTDC_ConfigLayer(&hLtdcHandler, &layer_cfg, LayerIndex); 

  DrawProp[LayerIndex].BackColor = LCD_COLOR_WHITE;
  DrawProp[LayerIndex].pFont     = &Font15P;
  DrawProp[LayerIndex].TextColor = LCD_COLOR_BLACK; 
	}


void BSP_LCD_SelectLayer(uint32_t LayerIndex)
	{
  ActiveLayer = LayerIndex;
	} 


void BSP_LCD_SetLayerVisible(uint32_t LayerIndex, FunctionalState State)
	{
  if(State == ENABLE)
		{
    __HAL_LTDC_LAYER_ENABLE(&hLtdcHandler, LayerIndex);
		}
  else
		{
    __HAL_LTDC_LAYER_DISABLE(&hLtdcHandler, LayerIndex);
		}
  __HAL_LTDC_RELOAD_CONFIG(&hLtdcHandler);
	} 


void BSP_LCD_SetTransparency(uint32_t LayerIndex, uint8_t Transparency)
	{    
  HAL_LTDC_SetAlpha(&hLtdcHandler, Transparency, LayerIndex);
	}


void BSP_LCD_SetLayerAddress(uint32_t LayerIndex, uint32_t Address)
	{
  HAL_LTDC_SetAddress(&hLtdcHandler, Address, LayerIndex);
	}

/**
  * @brief  Sets display window.
  * @param  LayerIndex: Layer index
  * @param  Xpos: LCD X position
  * @param  Ypos: LCD Y position
  * @param  Width: LCD window width
  * @param  Height: LCD window height  
  * @retval None
  */
void BSP_LCD_SetLayerWindow(uint16_t LayerIndex, uint16_t Xpos, uint16_t Ypos, uint16_t Width, uint16_t Height)
	{
  /* Reconfigure the layer size */
  HAL_LTDC_SetWindowSize(&hLtdcHandler, Width, Height, LayerIndex);
  /* Reconfigure the layer position */
  HAL_LTDC_SetWindowPosition(&hLtdcHandler, Xpos, Ypos, LayerIndex); 
	}

/**
  * @brief  Configures and sets the color keying.
  * @param  LayerIndex: Layer foreground or background
  * @param  RGBValue: Color reference
  * @retval None
  */
void BSP_LCD_SetColorKeying(uint32_t LayerIndex, uint32_t RGBValue)
	{  
  /* Configure and Enable the color Keying for LCD Layer */
  HAL_LTDC_ConfigColorKeying(&hLtdcHandler, RGBValue, LayerIndex);
  HAL_LTDC_EnableColorKeying(&hLtdcHandler, LayerIndex);
	}

/**
  * @brief  Disables the color keying.
  * @param  LayerIndex: Layer foreground or background
  * @retval None
  */
void BSP_LCD_ResetColorKeying(uint32_t LayerIndex)
	{   
  /* Disable the color Keying for LCD Layer */
  HAL_LTDC_DisableColorKeying(&hLtdcHandler, LayerIndex);
	}

void BSP_LCD_SetTextColor(uint16_t Color)
	{
  DrawProp[ActiveLayer].TextColor = Color;
	}

uint16_t BSP_LCD_GetTextColor(void)
	{
  return DrawProp[ActiveLayer].TextColor;
	}

void BSP_LCD_SetBackColor(uint16_t Color)
	{
  DrawProp[ActiveLayer].BackColor = Color;
	}

uint16_t BSP_LCD_GetBackColor(void)
	{
  return DrawProp[ActiveLayer].BackColor;
	}

void BSP_LCD_SetFont(sFONT *fonts)
	{
  DrawProp[ActiveLayer].pFont = fonts;
	}


sFONT *BSP_LCD_GetFont(void)
	{
  return DrawProp[ActiveLayer].pFont;
	}

/**
  * @brief  Reads an LCD pixel.
  * @param  Xpos: X position 
  * @param  Ypos: Y position 
  * @retval RGB pixel color
  */
uint32_t BSP_LCD_ReadPixel(uint16_t Xpos, uint16_t Ypos)
{
  uint32_t ret = 0;
  ret = *(__IO uint8_t*) (hLtdcHandler.LayerCfg[ActiveLayer].FBStartAdress + (2*(Ypos*480 + Xpos)));    
  return ret;
}

/**
  * @brief  Clears the hole LCD.
  * @param  Color: Color of the background
  * @retval None
  */
void BSP_LCD_Clear(uint16_t Color)
{ 
  /* Clear the LCD */ 
  LL_FillBuffer(ActiveLayer, (uint32_t *)(hLtdcHandler.LayerCfg[ActiveLayer].FBStartAdress), 480, BSP_LCD_GetYSize(), 0, Color);
}

/**
  * @brief  Clears the selected line.
  * @param  Line: Line to be cleared
  * @retval None
  */
void BSP_LCD_ClearStringLine(uint32_t Line)
{
  uint32_t color_backup = DrawProp[ActiveLayer].TextColor;
  DrawProp[ActiveLayer].TextColor = DrawProp[ActiveLayer].BackColor;
  
  /* Draw rectangle with background color */
  BSP_LCD_FillRect(0, (Line * DrawProp[ActiveLayer].pFont->Height), 480, DrawProp[ActiveLayer].pFont->Height);
  
  DrawProp[ActiveLayer].TextColor = color_backup;
  BSP_LCD_SetTextColor(DrawProp[ActiveLayer].TextColor);  
}

/**
  * @brief  Displays one character.
  * @param  Xpos: Start column address
  * @param  Ypos: Line where to display the character shape.
  * @param  Ascii: Character ascii code
  *           This parameter must be a number between Min_Data = 0x20 and Max_Data = 0x7E 
  * @retval None
  */
void BSP_LCD_DisplayChar(uint16_t Xpos, uint16_t Ypos, uint8_t Ascii)
{
  DrawChar(Xpos, Ypos, &DrawProp[ActiveLayer].pFont->table[(Ascii-' ') *\
    DrawProp[ActiveLayer].pFont->Height * ((DrawProp[ActiveLayer].pFont->Width + 7) / 8)]);
}

/**
  * @brief  Displays characters on the LCD.
  * @param  Xpos: X position (in pixel)
  * @param  Ypos: Y position (in pixel)   
  * @param  Text: Pointer to string to display on LCD
  * @param  Mode: Display mode
  *          This parameter can be one of the following values:
  *            @arg  CENTER_MODE
  *            @arg  RIGHT_MODE
  *            @arg  LEFT_MODE   
  * @retval None
  */
void BSP_LCD_DisplayStringAt(uint16_t Xpos, uint16_t Ypos, uint8_t *Text, Text_AlignModeTypdef Mode)
{
  uint16_t ref_column = 1, i = 0;
  uint32_t size = 0, xsize = 0; 
  uint8_t  *ptr = Text;
  uint16_t DisplayWidth = 480;
	
  /* Get the text size */
  while (*ptr++) size ++ ;
  
  /* Characters number per line */
  xsize = (480/DrawProp[ActiveLayer].pFont->Width);
  
  switch (Mode)
  {
  case LEFT_MODE:
    {
      ref_column = Xpos;
			TRANSPARENT_MODE_ENABLE = 0;
			DisplayWidth = 480;
      break;
    }
	case TRANSPARENT_MODE:
		{
		  ref_column = Xpos;
			TRANSPARENT_MODE_ENABLE = 1;
			DisplayWidth = 480;
      break;	
		}
	case INFO_MODE:
		{
		  ref_column = Xpos;
			TRANSPARENT_MODE_ENABLE = 1;
			DisplayWidth = 266;
      break;	
		}		
	case INFOTRACK_MODE:
		{
		  ref_column = Xpos;
			TRANSPARENT_MODE_ENABLE = 1;
			DisplayWidth = 357;
      break;	
		}		
  case RIGHT_MODE:
    {
      ref_column = - Xpos + ((xsize - size)*DrawProp[ActiveLayer].pFont->Width);
			TRANSPARENT_MODE_ENABLE = 0;
			DisplayWidth = 480;
      break;
    } 
  case CENTER_MODE:
    {
      ref_column = Xpos + ((xsize - size)* DrawProp[ActiveLayer].pFont->Width) / 2;
			TRANSPARENT_MODE_ENABLE = 0;
			DisplayWidth = 480;
      break;
    }		
  default:
    {
      ref_column = Xpos;
			TRANSPARENT_MODE_ENABLE = 0;
			DisplayWidth = 480;
      break;
    }
  }
  
  /* Check that the Start column is located in the screen */
  if ((ref_column < 1) || (ref_column >= 0x8000))
  {
    ref_column = 1;
  }

  /* Send the string character by character on LCD */
  //while ((*Text != 0) & (((BSP_LCD_GetXSize() - (i*DrawProp[ActiveLayer].pFont->Width)) & 0xFFFF) >= DrawProp[ActiveLayer].pFont->Width))
	
	
	while ((*Text != 0) & (((DisplayWidth - ref_column)) >= DrawProp[ActiveLayer].pFont->Width))
  {
    /* Display one character on LCD */
    BSP_LCD_DisplayChar(ref_column, Ypos, *Text);
    /* Decrement the column position by 16 */
		if(DrawProp[ActiveLayer].pFont==&Font15P)     //Dynamic width for Font15P 			
			{
			ref_column += (width15P[(*Text)-32]+2);	
			}
		else if(DrawProp[ActiveLayer].pFont==&Font7W)     //Dynamic width for Font7W 			
			{
			ref_column += (width7W[(*Text)-32]+1);	
			}
		else																					//Static width for other fonts
			{
			ref_column += DrawProp[ActiveLayer].pFont->Width;
			}
		/* Point on the next character */
    Text++;
    i++;
  }  
}

/**
  * @brief  Displays a maximum of 60 characters on the LCD.
  * @param  Line: Line where to display the character shape
  * @param  ptr: Pointer to string to display on LCD
  * @retval None
  */
void BSP_LCD_DisplayStringAtLine(uint16_t Line, uint8_t *ptr)
{  
  BSP_LCD_DisplayStringAt(0, LINE(Line), ptr, LEFT_MODE);
}

/**
  * @brief  Draws an horizontal line.
  * @param  Xpos: X position
  * @param  Ypos: Y position
  * @param  Length: Line length
  * @retval None
  */
void BSP_LCD_DrawHLine(uint16_t Xpos, uint16_t Ypos, uint16_t Length)
	{
  uint32_t  Xaddress = 0;
  Xaddress = (hLtdcHandler.LayerCfg[ActiveLayer].FBStartAdress) + 2*(480*Ypos + Xpos);
  LL_FillBuffer(ActiveLayer, (uint32_t *)Xaddress, Length, 1, 0, DrawProp[ActiveLayer].TextColor);
	}

/**
  * @brief  Draws a vertical line.
  * @param  Xpos: X position
  * @param  Ypos: Y position
  * @param  Length: Line length
  * @retval None
  */
void ForceDrawVLine(uint16_t Xpos, uint16_t Ypos, uint16_t Length, uint32_t color)
	{
  uint32_t  Xaddress = 0;
  Xaddress = (hLtdcHandler.LayerCfg[ActiveLayer].FBStartAdress) + 2*(480*Ypos + Xpos);	
  hDma2dHandler.Init.Mode         = DMA2D_R2M;
  hDma2dHandler.Init.ColorMode    = DMA2D_ARGB1555;
  hDma2dHandler.Init.OutputOffset = 479;      
  hDma2dHandler.Instance = DMA2D;
  if(HAL_DMA2D_Init(&hDma2dHandler) == HAL_OK) 
		{
		if(HAL_DMA2D_ConfigLayer(&hDma2dHandler, ActiveLayer) == HAL_OK) 
			{
			if (HAL_DMA2D_Start(&hDma2dHandler, color, Xaddress, 1, Length) == HAL_OK)
				{
        HAL_DMA2D_PollForTransfer(&hDma2dHandler, 10);
				}
			}
		} 
	}

/**
  * @brief  Draws a vertical line.
  * @param  Xpos: X position
  * @param  Ypos: Y position
  * @param  Length: Line length
  * @retval None
  */
void BSP_LCD_DrawVLine(uint16_t Xpos, uint8_t Ypos, uint8_t Length)
	{
  uint32_t  Xaddress = 0;
  Xaddress = (hLtdcHandler.LayerCfg[ActiveLayer].FBStartAdress) + 2*(480*Ypos + Xpos);
  /* Write line */
  LL_FillBuffer(ActiveLayer, (uint32_t *)Xaddress, 1, Length, 479, DrawProp[ActiveLayer].TextColor);
	}

/**
  * @brief  Draws an uni-line (between two points).
  * @param  x1: Point 1 X position
  * @param  y1: Point 1 Y position
  * @param  x2: Point 2 X position
  * @param  y2: Point 2 Y position
  * @retval None
  */
void BSP_LCD_DrawLine(uint16_t x1, uint16_t y1, uint16_t x2, uint16_t y2)
{
  int16_t deltax = 0, deltay = 0, x = 0, y = 0, xinc1 = 0, xinc2 = 0, 
  yinc1 = 0, yinc2 = 0, den = 0, num = 0, num_add = 0, num_pixels = 0, 
  curpixel = 0;
  
  deltax = ABS(x2 - x1);        /* The difference between the x's */
  deltay = ABS(y2 - y1);        /* The difference between the y's */
  x = x1;                       /* Start x off at the first pixel */
  y = y1;                       /* Start y off at the first pixel */
  
  if (x2 >= x1)                 /* The x-values are increasing */
  {
    xinc1 = 1;
    xinc2 = 1;
  }
  else                          /* The x-values are decreasing */
  {
    xinc1 = -1;
    xinc2 = -1;
  }
  
  if (y2 >= y1)                 /* The y-values are increasing */
  {
    yinc1 = 1;
    yinc2 = 1;
  }
  else                          /* The y-values are decreasing */
  {
    yinc1 = -1;
    yinc2 = -1;
  }
  
  if (deltax >= deltay)         /* There is at least one x-value for every y-value */
  {
    xinc1 = 0;                  /* Don't change the x when numerator >= denominator */
    yinc2 = 0;                  /* Don't change the y for every iteration */
    den = deltax;
    num = deltax / 2;
    num_add = deltay;
    num_pixels = deltax;         /* There are more x-values than y-values */
  }
  else                          /* There is at least one y-value for every x-value */
  {
    xinc2 = 0;                  /* Don't change the x for every iteration */
    yinc1 = 0;                  /* Don't change the y when numerator >= denominator */
    den = deltay;
    num = deltay / 2;
    num_add = deltax;
    num_pixels = deltay;         /* There are more y-values than x-values */
  }
  
  for (curpixel = 0; curpixel <= num_pixels; curpixel++)
  {
    BSP_LCD_DrawPixel(x, y, DrawProp[ActiveLayer].TextColor);   /* Draw the current pixel */
    num += num_add;                            /* Increase the numerator by the top of the fraction */
    if (num >= den)                           /* Check if numerator >= denominator */
    {
      num -= den;                             /* Calculate the new numerator value */
      x += xinc1;                             /* Change the x as appropriate */
      y += yinc1;                             /* Change the y as appropriate */
    }
    x += xinc2;                               /* Change the x as appropriate */
    y += yinc2;                               /* Change the y as appropriate */
  }
}

/**
  * @brief  Draws a rectangle.
  * @param  Xpos: X position
  * @param  Ypos: Y position
  * @param  Width: Rectangle width  
  * @param  Height: Rectangle height
  * @retval None
  */
void BSP_LCD_DrawRect(uint16_t Xpos, uint16_t Ypos, uint16_t Width, uint16_t Height)
{
  /* Draw horizontal lines */
  BSP_LCD_DrawHLine(Xpos, Ypos, Width);
  BSP_LCD_DrawHLine(Xpos, (Ypos + Height - 1), Width);
  
  /* Draw vertical lines */
  BSP_LCD_DrawVLine(Xpos, Ypos, Height);
  BSP_LCD_DrawVLine((Xpos + Width -1), Ypos, Height);
}

/**
  * @brief  Draws a circle.
  * @param  Xpos: X position
  * @param  Ypos: Y position
  * @param  Radius: Circle radius
  * @retval None
  */
void BSP_LCD_DrawCircle(uint16_t Xpos, uint16_t Ypos, uint16_t Radius)
{
  int32_t   decision;    /* Decision Variable */ 
  uint32_t  current_x;   /* Current X Value */
  uint32_t  current_y;   /* Current Y Value */
  
  decision = 3 - (Radius << 1);
  current_x = 0;
  current_y = Radius;
  
  while (current_x <= current_y)
  {
    BSP_LCD_DrawPixel((Xpos + current_x), (Ypos - current_y), DrawProp[ActiveLayer].TextColor);
    BSP_LCD_DrawPixel((Xpos - current_x), (Ypos - current_y), DrawProp[ActiveLayer].TextColor);
    BSP_LCD_DrawPixel((Xpos + current_y), (Ypos - current_x), DrawProp[ActiveLayer].TextColor);
    BSP_LCD_DrawPixel((Xpos - current_y), (Ypos - current_x), DrawProp[ActiveLayer].TextColor);
    BSP_LCD_DrawPixel((Xpos + current_x), (Ypos + current_y), DrawProp[ActiveLayer].TextColor);
    BSP_LCD_DrawPixel((Xpos - current_x), (Ypos + current_y), DrawProp[ActiveLayer].TextColor);
    BSP_LCD_DrawPixel((Xpos + current_y), (Ypos + current_x), DrawProp[ActiveLayer].TextColor);
    BSP_LCD_DrawPixel((Xpos - current_y), (Ypos + current_x), DrawProp[ActiveLayer].TextColor);
    
    if (decision < 0)
    { 
      decision += (current_x << 2) + 6;
    }
    else
    {
      decision += ((current_x - current_y) << 2) + 10;
      current_y--;
    }
    current_x++;
  } 
}


void BSP_LCD_DrawPolygon(pPoint Points, uint16_t PointCount)
{
  int16_t x = 0, y = 0;
  
  if(PointCount < 2)
  {
    return;
  }
  
  BSP_LCD_DrawLine(Points->X, Points->Y, (Points+PointCount-1)->X, (Points+PointCount-1)->Y);
  
  while(--PointCount)
  {
    x = Points->X;
    y = Points->Y;
    Points++;
    BSP_LCD_DrawLine(x, y, Points->X, Points->Y);
  }
}


void BSP_LCD_DrawEllipse(int Xpos, int Ypos, int XRadius, int YRadius)
{
  int x = 0, y = -YRadius, err = 2-2*XRadius, e2;
  float k = 0, rad1 = 0, rad2 = 0;
  
  rad1 = XRadius;
  rad2 = YRadius;
  
  k = (float)(rad2/rad1);  
  
  do { 
    BSP_LCD_DrawPixel((Xpos-(uint16_t)(x/k)), (Ypos+y), DrawProp[ActiveLayer].TextColor);
    BSP_LCD_DrawPixel((Xpos+(uint16_t)(x/k)), (Ypos+y), DrawProp[ActiveLayer].TextColor);
    BSP_LCD_DrawPixel((Xpos+(uint16_t)(x/k)), (Ypos-y), DrawProp[ActiveLayer].TextColor);
    BSP_LCD_DrawPixel((Xpos-(uint16_t)(x/k)), (Ypos-y), DrawProp[ActiveLayer].TextColor);      
    
    e2 = err;
    if (e2 <= x) {
      err += ++x*2+1;
      if (-y == x && e2 <= y) e2 = 0;
    }
    if (e2 > y) err += ++y*2+1;     
  }
  while (y <= 0);
}


void BSP_LCD_DrawPixel(uint16_t Xpos, uint16_t Ypos, uint16_t RGB_Code)
	{
   *(__IO uint16_t*) (hLtdcHandler.LayerCfg[ActiveLayer].FBStartAdress + (2*(Ypos*480 + Xpos))) = RGB_Code;
	}



void BSP_LCD_FillRect(uint16_t Xpos, uint16_t Ypos, uint16_t Width, uint16_t Height)
	{
  uint32_t  x_address = 0;  
  x_address = (hLtdcHandler.LayerCfg[ActiveLayer].FBStartAdress) + 2*(480*Ypos + Xpos);
  LL_FillBuffer(ActiveLayer, (uint32_t *)x_address, Width, Height, (480-Width), DrawProp[ActiveLayer].TextColor);	
	}


void BSP_LCD_FillCircle(uint16_t Xpos, uint16_t Ypos, uint16_t Radius)
{
  int32_t  decision;     /* Decision Variable */ 
  uint32_t  current_x;   /* Current X Value */
  uint32_t  current_y;   /* Current Y Value */
  
  decision = 3 - (Radius << 1);
  
  current_x = 0;
  current_y = Radius;
  
  BSP_LCD_SetTextColor(DrawProp[ActiveLayer].TextColor);
  
  while (current_x <= current_y)
  {
    if(current_y > 0) 
    {
      BSP_LCD_DrawHLine(Xpos - current_y, Ypos + current_x, 2*current_y);
      BSP_LCD_DrawHLine(Xpos - current_y, Ypos - current_x, 2*current_y);
    }
    
    if(current_x > 0) 
    {
      BSP_LCD_DrawHLine(Xpos - current_x, Ypos - current_y, 2*current_x);
      BSP_LCD_DrawHLine(Xpos - current_x, Ypos + current_y, 2*current_x);
    }
    if (decision < 0)
    { 
      decision += (current_x << 2) + 6;
    }
    else
    {
      decision += ((current_x - current_y) << 2) + 10;
      current_y--;
    }
    current_x++;
  }
  
  BSP_LCD_SetTextColor(DrawProp[ActiveLayer].TextColor);
  BSP_LCD_DrawCircle(Xpos, Ypos, Radius);
}

/**
  * @brief  Draws a full poly-line (between many points).
  * @param  Points: Pointer to the points array
  * @param  PointCount: Number of points
  * @retval None
  */
void BSP_LCD_FillPolygon(pPoint Points, uint16_t PointCount)
{
  int16_t X = 0, Y = 0, X2 = 0, Y2 = 0, X_center = 0, Y_center = 0, X_first = 0, Y_first = 0, pixelX = 0, pixelY = 0, counter = 0;
  uint16_t  image_left = 0, image_right = 0, image_top = 0, image_bottom = 0;
  
  image_left = image_right = Points->X;
  image_top= image_bottom = Points->Y;
  
  for(counter = 1; counter < PointCount; counter++)
  {
    pixelX = POLY_X(counter);
    if(pixelX < image_left)
    {
      image_left = pixelX;
    }
    if(pixelX > image_right)
    {
      image_right = pixelX;
    }
    
    pixelY = POLY_Y(counter);
    if(pixelY < image_top)
    { 
      image_top = pixelY;
    }
    if(pixelY > image_bottom)
    {
      image_bottom = pixelY;
    }
  }  
  
  if(PointCount < 2)
  {
    return;
  }
  
  X_center = (image_left + image_right)/2;
  Y_center = (image_bottom + image_top)/2;
  
  X_first = Points->X;
  Y_first = Points->Y;
  
  while(--PointCount)
  {
    X = Points->X;
    Y = Points->Y;
    Points++;
    X2 = Points->X;
    Y2 = Points->Y;    
    
    FillTriangle(X, X2, X_center, Y, Y2, Y_center);
    FillTriangle(X, X_center, X2, Y, Y_center, Y2);
    FillTriangle(X_center, X2, X, Y_center, Y2, Y);   
  }
  
  FillTriangle(X_first, X2, X_center, Y_first, Y2, Y_center);
  FillTriangle(X_first, X_center, X2, Y_first, Y_center, Y2);
  FillTriangle(X_center, X2, X_first, Y_center, Y2, Y_first);   
}

/**
  * @brief  Draws a full ellipse.
  * @param  Xpos: X position
  * @param  Ypos: Y position
  * @param  XRadius: Ellipse X radius
  * @param  YRadius: Ellipse Y radius  
  * @retval None
  */
void BSP_LCD_FillEllipse(int Xpos, int Ypos, int XRadius, int YRadius)
{
  int x = 0, y = -YRadius, err = 2-2*XRadius, e2;
  float k = 0, rad1 = 0, rad2 = 0;
  
  rad1 = XRadius;
  rad2 = YRadius;
  
  k = (float)(rad2/rad1);
  
  do 
  {       
    BSP_LCD_DrawHLine((Xpos-(uint16_t)(x/k)), (Ypos+y), (2*(uint16_t)(x/k) + 1));
    BSP_LCD_DrawHLine((Xpos-(uint16_t)(x/k)), (Ypos-y), (2*(uint16_t)(x/k) + 1));
    
    e2 = err;
    if (e2 <= x) 
    {
      err += ++x*2+1;
      if (-y == x && e2 <= y) e2 = 0;
    }
    if (e2 > y) err += ++y*2+1;
  }
  while (y <= 0);
}



/**
  * @brief  Initializes the LTDC MSP.
  * @param  hltdc: LTDC handle
  * @param  Params
  * @retval None
  */
__weak void BSP_LCD_MspInit(LTDC_HandleTypeDef *hltdc, void *Params)
{

  /* Enable the LTDC and DMA2D clocks */
  __HAL_RCC_LTDC_CLK_ENABLE();
  __HAL_RCC_DMA2D_CLK_ENABLE();

}


/*******************************************************************************
                            Static Functions
*******************************************************************************/

/**
  * @brief  Draws a character on LCD.
  * @param  Xpos: Line where to display the character shape
  * @param  Ypos: Start column address
  * @param  c: Pointer to the character data
  * @retval None
  */
static void DrawChar(uint16_t Xpos, uint16_t Ypos, const uint8_t *c)
{
  uint32_t i = 0, j = 0;
  uint16_t height, width;
  uint8_t  offset;
  uint8_t  *pchar;
  uint32_t line;
  
  height = DrawProp[ActiveLayer].pFont->Height;
  width  = DrawProp[ActiveLayer].pFont->Width;
  
  offset =  8 *((width + 7)/8) -  width ;
  
  for(i = 0; i < height; i++)
  {
    pchar = ((uint8_t *)c + (width + 7)/8 * i);
    
    switch(((width + 7)/8))
    {
      
    case 1:
      line =  pchar[0];      
      break;
      
    case 2:
      line =  (pchar[0]<< 8) | pchar[1];      
      break;
      
    case 3:
    default:
      line =  (pchar[0]<< 16) | (pchar[1]<< 8) | pchar[2];      
      break;
    } 
    
    for (j = 0; j < width; j++)
    {
      if(line & (1 << (width- j + offset- 1))) 
      {
        BSP_LCD_DrawPixel((Xpos + j), Ypos, DrawProp[ActiveLayer].TextColor);						
      }
			else if(TRANSPARENT_MODE_ENABLE==0)
      {
       BSP_LCD_DrawPixel((Xpos + j), Ypos, DrawProp[ActiveLayer].BackColor);
      } 
    }
    Ypos++;
  }
}

/**
  * @brief  Fills a triangle (between 3 points).
  * @param  x1: Point 1 X position
  * @param  y1: Point 1 Y position
  * @param  x2: Point 2 X position
  * @param  y2: Point 2 Y position
  * @param  x3: Point 3 X position
  * @param  y3: Point 3 Y position
  * @retval None
  */
void FillTriangle(uint16_t x1, uint16_t x2, uint16_t x3, uint16_t y1, uint16_t y2, uint16_t y3)
{ 
  int16_t deltax = 0, deltay = 0, x = 0, y = 0, xinc1 = 0, xinc2 = 0, 
  yinc1 = 0, yinc2 = 0, den = 0, num = 0, num_add = 0, num_pixels = 0,
  curpixel = 0;
  
  deltax = ABS(x2 - x1);        /* The difference between the x's */
  deltay = ABS(y2 - y1);        /* The difference between the y's */
  x = x1;                       /* Start x off at the first pixel */
  y = y1;                       /* Start y off at the first pixel */
  
  if (x2 >= x1)                 /* The x-values are increasing */
  {
    xinc1 = 1;
    xinc2 = 1;
  }
  else                          /* The x-values are decreasing */
  {
    xinc1 = -1;
    xinc2 = -1;
  }
  
  if (y2 >= y1)                 /* The y-values are increasing */
  {
    yinc1 = 1;
    yinc2 = 1;
  }
  else                          /* The y-values are decreasing */
  {
    yinc1 = -1;
    yinc2 = -1;
  }
  
  if (deltax >= deltay)         /* There is at least one x-value for every y-value */
  {
    xinc1 = 0;                  /* Don't change the x when numerator >= denominator */
    yinc2 = 0;                  /* Don't change the y for every iteration */
    den = deltax;
    num = deltax / 2;
    num_add = deltay;
    num_pixels = deltax;         /* There are more x-values than y-values */
  }
  else                          /* There is at least one y-value for every x-value */
  {
    xinc2 = 0;                  /* Don't change the x for every iteration */
    yinc1 = 0;                  /* Don't change the y when numerator >= denominator */
    den = deltay;
    num = deltay / 2;
    num_add = deltax;
    num_pixels = deltay;         /* There are more y-values than x-values */
  }
  
  for (curpixel = 0; curpixel <= num_pixels; curpixel++)
  {
    BSP_LCD_DrawLine(x, y, x3, y3);
    
    num += num_add;              /* Increase the numerator by the top of the fraction */
    if (num >= den)             /* Check if numerator >= denominator */
    {
      num -= den;               /* Calculate the new numerator value */
      x += xinc1;               /* Change the x as appropriate */
      y += yinc1;               /* Change the y as appropriate */
    }
    x += xinc2;                 /* Change the x as appropriate */
    y += yinc2;                 /* Change the y as appropriate */
  } 
}

/**
  * @brief  Fills a buffer.
  * @param  LayerIndex: Layer index
  * @param  pDst: Pointer to destination buffer
  * @param  xSize: Buffer width
  * @param  ySize: Buffer height
  * @param  OffLine: Offset
  * @param  ColorIndex: Color index
  * @retval None
  */
static void LL_FillBuffer(uint32_t LayerIndex, void *pDst, uint32_t xSize, uint32_t ySize, uint32_t OffLine, uint16_t ColorIndex) 
	{
  hDma2dHandler.Init.Mode         = DMA2D_R2M;
  hDma2dHandler.Init.ColorMode    = DMA2D_ARGB1555;
  hDma2dHandler.Init.OutputOffset = OffLine;      
  hDma2dHandler.Instance = DMA2D;	

  if(HAL_DMA2D_Init(&hDma2dHandler) == HAL_OK) 
		{
    if(HAL_DMA2D_ConfigLayer(&hDma2dHandler, LayerIndex) == HAL_OK) 
			{
      if (HAL_DMA2D_Start(&hDma2dHandler, ColorIndex, (uint32_t)pDst, xSize, ySize) == HAL_OK)
				{
				HAL_DMA2D_PollForTransfer(&hDma2dHandler, 10);					
				}			
			}			
		} 		
	}

    

/********************END OF FILE****/
