djgreeb/XDJ-X/FW_BACKUP/XDJX/Src/quadspi.c

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
/* Includes ------------------------------------------------------------------*/
#include "quadspi.h"

/* USER CODE BEGIN 0 */
static uint8_t QSPI_WriteEnable(void);
uint8_t QSPI_AutoPollingMemReady(void);
static uint8_t QSPI_Configuration(void);
static uint8_t QSPI_ResetChip(void);

/* USER CODE END 0 */

QSPI_HandleTypeDef hqspi;

/* QUADSPI init function */
void MX_QUADSPI_Init(void)
{

  hqspi.Instance = QUADSPI;
  hqspi.Init.ClockPrescaler = 1;
  hqspi.Init.FifoThreshold = 4;
  hqspi.Init.SampleShifting = QSPI_SAMPLE_SHIFTING_HALFCYCLE;
  hqspi.Init.FlashSize = 22;
  hqspi.Init.ChipSelectHighTime = QSPI_CS_HIGH_TIME_5_CYCLE;
  hqspi.Init.ClockMode = QSPI_CLOCK_MODE_0;
  hqspi.Init.FlashID = QSPI_FLASH_ID_1;
  hqspi.Init.DualFlash = QSPI_DUALFLASH_DISABLE;
  if (HAL_QSPI_Init(&hqspi) != HAL_OK)
  {
    Error_Handler();
  }
}

void HAL_QSPI_MspInit(QSPI_HandleTypeDef* qspiHandle)
{

  GPIO_InitTypeDef GPIO_InitStruct = {0};
  RCC_PeriphCLKInitTypeDef PeriphClkInitStruct = {0};
  if(qspiHandle->Instance==QUADSPI)
  {
  /** Initializes the peripherals clock
  */
    PeriphClkInitStruct.PeriphClockSelection = RCC_PERIPHCLK_QSPI;
    PeriphClkInitStruct.QspiClockSelection = RCC_QSPICLKSOURCE_D1HCLK;
    if (HAL_RCCEx_PeriphCLKConfig(&PeriphClkInitStruct) != HAL_OK)
    {
      Error_Handler();
    }

    /* QUADSPI clock enable */
    __HAL_RCC_QSPI_CLK_ENABLE();

    __HAL_RCC_GPIOG_CLK_ENABLE();
    __HAL_RCC_GPIOF_CLK_ENABLE();
    /**QUADSPI GPIO Configuration
    PG6     ------> QUADSPI_BK1_NCS
    PF6     ------> QUADSPI_BK1_IO3
    PF7     ------> QUADSPI_BK1_IO2
    PF8     ------> QUADSPI_BK1_IO0
    PF10     ------> QUADSPI_CLK
    PF9     ------> QUADSPI_BK1_IO1
    */
    GPIO_InitStruct.Pin = GPIO_PIN_6;
    GPIO_InitStruct.Mode = GPIO_MODE_AF_PP;
    GPIO_InitStruct.Pull = GPIO_NOPULL;
    GPIO_InitStruct.Speed = GPIO_SPEED_FREQ_HIGH;
    GPIO_InitStruct.Alternate = GPIO_AF10_QUADSPI;
    HAL_GPIO_Init(GPIOG, &GPIO_InitStruct);

    GPIO_InitStruct.Pin = GPIO_PIN_6|GPIO_PIN_7|GPIO_PIN_10;
    GPIO_InitStruct.Mode = GPIO_MODE_AF_PP;
    GPIO_InitStruct.Pull = GPIO_NOPULL;
    GPIO_InitStruct.Speed = GPIO_SPEED_FREQ_HIGH;
    GPIO_InitStruct.Alternate = GPIO_AF9_QUADSPI;
    HAL_GPIO_Init(GPIOF, &GPIO_InitStruct);

    GPIO_InitStruct.Pin = GPIO_PIN_8|GPIO_PIN_9;
    GPIO_InitStruct.Mode = GPIO_MODE_AF_PP;
    GPIO_InitStruct.Pull = GPIO_NOPULL;
    GPIO_InitStruct.Speed = GPIO_SPEED_FREQ_HIGH;
    GPIO_InitStruct.Alternate = GPIO_AF10_QUADSPI;
    HAL_GPIO_Init(GPIOF, &GPIO_InitStruct);

  }
}

void HAL_QSPI_MspDeInit(QSPI_HandleTypeDef* qspiHandle)
{

  if(qspiHandle->Instance==QUADSPI)
  {
    /* Peripheral clock disable */
    __HAL_RCC_QSPI_CLK_DISABLE();

    /**QUADSPI GPIO Configuration
    PG6     ------> QUADSPI_BK1_NCS
    PF6     ------> QUADSPI_BK1_IO3
    PF7     ------> QUADSPI_BK1_IO2
    PF8     ------> QUADSPI_BK1_IO0
    PF10     ------> QUADSPI_CLK
    PF9     ------> QUADSPI_BK1_IO1
    */
    HAL_GPIO_DeInit(GPIOG, GPIO_PIN_6);

    HAL_GPIO_DeInit(GPIOF, GPIO_PIN_6|GPIO_PIN_7|GPIO_PIN_8|GPIO_PIN_10
                          |GPIO_PIN_9);

  }
}

/* USER CODE BEGIN 1 */

/* QUADSPI init function */
uint8_t CSP_QUADSPI_Init(void) {

	//prepare QSPI peripheral for ST-Link Utility operations
	hqspi.Instance = QUADSPI;
	if (HAL_QSPI_DeInit(&hqspi) != HAL_OK) {
		return HAL_ERROR;
	}

	MX_QUADSPI_Init();

	if (QSPI_ResetChip() != HAL_OK) {
		return HAL_ERROR;
	}

	HAL_Delay(3);

	if (QSPI_AutoPollingMemReady() != HAL_OK) {
		return HAL_ERROR;
	}

	if (QSPI_WriteEnable() != HAL_OK) {

		return HAL_ERROR;
	}

	if (QSPI_Configuration() != HAL_OK) {
		return HAL_ERROR;
	}

	HAL_Delay(100);

	return HAL_OK;

}

uint8_t CSP_QSPI_Erase_Chip(void) {

	QSPI_CommandTypeDef sCommand;

	if (QSPI_WriteEnable() != HAL_OK) {
		return HAL_ERROR;
	}

	/* Erasing Sequence --------------------------------- */
	sCommand.InstructionMode = QSPI_INSTRUCTION_1_LINE;
	sCommand.Instruction = CHIP_ERASE_CMD;
	sCommand.AddressMode = QSPI_ADDRESS_NONE;
	sCommand.AlternateByteMode = QSPI_ALTERNATE_BYTES_NONE;
	sCommand.DataMode = QSPI_DATA_NONE;
	sCommand.DummyCycles = 0;
	sCommand.DdrMode = QSPI_DDR_MODE_DISABLE;
	sCommand.DdrHoldHalfCycle = QSPI_DDR_HHC_ANALOG_DELAY;
	sCommand.SIOOMode = QSPI_SIOO_INST_EVERY_CMD;

	if (HAL_QSPI_Command(&hqspi, &sCommand, HAL_MAX_DELAY) != HAL_OK) {
		return HAL_ERROR;
	}

	if (QSPI_AutoPollingMemReady() != HAL_OK) {
		return HAL_ERROR;
	}

	return HAL_OK;

}

uint8_t QSPI_AutoPollingMemReady(void) {

	QSPI_CommandTypeDef sCommand = { 0 };
	QSPI_AutoPollingTypeDef sConfig = { 0 };
	HAL_StatusTypeDef ret;

	/* Configure automatic polling mode to wait for memory ready ------ */
	sCommand.InstructionMode = QSPI_INSTRUCTION_1_LINE;
	sCommand.Instruction = READ_STATUS_REG_CMD;
	sCommand.AddressMode = QSPI_ADDRESS_NONE;
	sCommand.AlternateByteMode = QSPI_ALTERNATE_BYTES_NONE;
	sCommand.DataMode = QSPI_DATA_1_LINE;
	sCommand.DummyCycles = 0;
	sCommand.DdrMode = QSPI_DDR_MODE_DISABLE;
	sCommand.DdrHoldHalfCycle = QSPI_DDR_HHC_ANALOG_DELAY;
	sCommand.SIOOMode = QSPI_SIOO_INST_EVERY_CMD;

	sConfig.Match = 0x00;
	sConfig.Mask = 0x01;
	sConfig.MatchMode = QSPI_MATCH_MODE_AND;
	sConfig.StatusBytesSize = 1;
	sConfig.Interval = 0x10;
	sConfig.AutomaticStop = QSPI_AUTOMATIC_STOP_ENABLE;
	if ((ret = HAL_QSPI_AutoPolling(&hqspi, &sCommand, &sConfig,
			HAL_MAX_DELAY)) != HAL_OK) {
		return ret;
	}
	return HAL_OK;
}

static uint8_t QSPI_WriteEnable(void) {
	QSPI_CommandTypeDef sCommand = { 0 };
	QSPI_AutoPollingTypeDef sConfig = { 0 };
	HAL_StatusTypeDef ret;

	/* Enable write operations ------------------------------------------ */
	sCommand.InstructionMode = QSPI_INSTRUCTION_1_LINE;
	sCommand.Instruction = WRITE_ENABLE_CMD;
	sCommand.AddressMode = QSPI_ADDRESS_NONE;
	sCommand.AlternateByteMode = QSPI_ALTERNATE_BYTES_NONE;
	sCommand.DataMode = QSPI_DATA_NONE;
	sCommand.DummyCycles = 0;
	sCommand.DdrMode = QSPI_DDR_MODE_DISABLE;
	sCommand.DdrHoldHalfCycle = QSPI_DDR_HHC_ANALOG_DELAY;
	sCommand.SIOOMode = QSPI_SIOO_INST_EVERY_CMD;

	if ((ret = HAL_QSPI_Command(&hqspi, &sCommand,
			HAL_QPSI_TIMEOUT_DEFAULT_VALUE)) != HAL_OK) {
		return ret;
	}

	/* Configure automatic polling mode to wait for write enabling ---- */
	sConfig.Match = 0x02;
	sConfig.Mask = 0x02;
	sConfig.MatchMode = QSPI_MATCH_MODE_AND;
	sConfig.StatusBytesSize = 1;
	sConfig.Interval = 0x10;
	sConfig.AutomaticStop = QSPI_AUTOMATIC_STOP_ENABLE;

	sCommand.Instruction = READ_STATUS_REG_CMD;
	sCommand.DataMode = QSPI_DATA_1_LINE;

	if ((ret = HAL_QSPI_AutoPolling(&hqspi, &sCommand, &sConfig,
			HAL_QPSI_TIMEOUT_DEFAULT_VALUE)) != HAL_OK) {
		return ret;
	}
	return HAL_OK;
}
/*Enable quad mode*/
/* Las versiones acabadas en IQ lo llevan activado por defecto, como en mi caso. */

uint8_t QSPI_Configuration(void) {

	QSPI_CommandTypeDef sCommand = { 0 };
	uint8_t reg;
	HAL_StatusTypeDef ret;

	/* Read Volatile Configuration register 2 --------------------------- */
	sCommand.InstructionMode = QSPI_INSTRUCTION_1_LINE;
	sCommand.Instruction = READ_STATUS_REG2_CMD;
	sCommand.AddressMode = QSPI_ADDRESS_NONE;
	sCommand.AlternateByteMode = QSPI_ALTERNATE_BYTES_NONE;
	sCommand.DataMode = QSPI_DATA_1_LINE;
	sCommand.DummyCycles = 0;
	sCommand.DdrMode = QSPI_DDR_MODE_DISABLE;
	sCommand.DdrHoldHalfCycle = QSPI_DDR_HHC_ANALOG_DELAY;
	sCommand.SIOOMode = QSPI_SIOO_INST_EVERY_CMD;
	sCommand.NbData = 1;

	if ((ret = HAL_QSPI_Command(&hqspi, &sCommand,
			HAL_QPSI_TIMEOUT_DEFAULT_VALUE)) != HAL_OK) {
		return ret;
	}

	if ((ret = HAL_QSPI_Receive(&hqspi, &reg, HAL_QPSI_TIMEOUT_DEFAULT_VALUE))
			!= HAL_OK) {
		return ret;
	}

	/* Enable Volatile Write operations ---------------------------------------- */
	sCommand.DataMode = QSPI_DATA_NONE;
	sCommand.Instruction = VOLATILE_SR_WRITE_ENABLE;

	if (HAL_QSPI_Command(&hqspi, &sCommand, HAL_QPSI_TIMEOUT_DEFAULT_VALUE)
			!= HAL_OK) {
		return ret;
	}

	/* Write Volatile Configuration register 2 (QE = 1) -- */
	sCommand.DataMode = QSPI_DATA_1_LINE;
	sCommand.Instruction = WRITE_STATUS_REG2_CMD;
	reg |= 2; // QE bit

	if (HAL_QSPI_Command(&hqspi, &sCommand, HAL_QPSI_TIMEOUT_DEFAULT_VALUE)
			!= HAL_OK) {
		return ret;
	}

	if (HAL_QSPI_Transmit(&hqspi, &reg, HAL_QPSI_TIMEOUT_DEFAULT_VALUE)
			!= HAL_OK) {
		return ret;
	}

	/* Read Volatile Configuration register 3 --------------------------- */
	sCommand.InstructionMode = QSPI_INSTRUCTION_1_LINE;
	sCommand.Instruction = READ_STATUS_REG3_CMD;
	sCommand.AddressMode = QSPI_ADDRESS_NONE;
	sCommand.AlternateByteMode = QSPI_ALTERNATE_BYTES_NONE;
	sCommand.DataMode = QSPI_DATA_1_LINE;
	sCommand.DummyCycles = 0;
	sCommand.DdrMode = QSPI_DDR_MODE_DISABLE;
	sCommand.DdrHoldHalfCycle = QSPI_DDR_HHC_ANALOG_DELAY;
	sCommand.SIOOMode = QSPI_SIOO_INST_EVERY_CMD;
	sCommand.NbData = 1;

	if ((ret = HAL_QSPI_Command(&hqspi, &sCommand,
			HAL_QPSI_TIMEOUT_DEFAULT_VALUE)) != HAL_OK) {
		return ret;
	}

	if ((ret = HAL_QSPI_Receive(&hqspi, &reg, HAL_QPSI_TIMEOUT_DEFAULT_VALUE))
			!= HAL_OK) {
		return ret;
	}

	/* Write Volatile Configuration register 2 (DRV1:2 = 00) -- */
	sCommand.Instruction = WRITE_STATUS_REG3_CMD;
	reg &= 0x9f; // DRV1:2 bit

	if (HAL_QSPI_Command(&hqspi, &sCommand, HAL_QPSI_TIMEOUT_DEFAULT_VALUE)
			!= HAL_OK) {
		return ret;
	}

	if (HAL_QSPI_Transmit(&hqspi, &reg, HAL_QPSI_TIMEOUT_DEFAULT_VALUE)
			!= HAL_OK) {
		return ret;
	}

	return HAL_OK;
}

uint8_t CSP_QSPI_EraseBlock(uint32_t flash_address) {
	QSPI_CommandTypeDef sCommand = { 0 };
	HAL_StatusTypeDef ret;

	sCommand.InstructionMode = QSPI_INSTRUCTION_1_LINE;
	sCommand.AddressSize = QSPI_ADDRESS_24_BITS;
	sCommand.AlternateByteMode = QSPI_ALTERNATE_BYTES_NONE;
	sCommand.DdrMode = QSPI_DDR_MODE_DISABLE;
	sCommand.DdrHoldHalfCycle = QSPI_DDR_HHC_ANALOG_DELAY;
	sCommand.SIOOMode = QSPI_SIOO_INST_EVERY_CMD;

	/* Enable write operations ------------------------------------------- */
	if ((ret = QSPI_WriteEnable()) != HAL_OK) {
		return ret;
	}

	/* Erasing Sequence -------------------------------------------------- */
	sCommand.Instruction = BLOCK_ERASE_CMD;
	sCommand.AddressMode = QSPI_ADDRESS_1_LINE;
	sCommand.Address = flash_address;
	sCommand.DataMode = QSPI_DATA_NONE;
	sCommand.DummyCycles = 0;

	if ((ret = HAL_QSPI_Command(&hqspi, &sCommand,
			HAL_QPSI_TIMEOUT_DEFAULT_VALUE)) != HAL_OK) {
		return ret;
	}
	return HAL_OK;
}

uint8_t CSP_QSPI_EraseSector(uint32_t EraseStartAddress,
		uint32_t EraseEndAddress) {

	QSPI_CommandTypeDef sCommand;

	EraseStartAddress = EraseStartAddress
			- EraseStartAddress % MEMORY_SECTOR_SIZE;

	/* Erasing Sequence -------------------------------------------------- */
	sCommand.InstructionMode = QSPI_INSTRUCTION_1_LINE;
	sCommand.Instruction = SECTOR_ERASE_CMD;
	sCommand.AddressMode = QSPI_ADDRESS_1_LINE;
	sCommand.AddressSize = QSPI_ADDRESS_24_BITS;
	sCommand.AlternateByteMode = QSPI_ALTERNATE_BYTES_NONE;
	sCommand.DdrMode = QSPI_DDR_MODE_DISABLE;
	sCommand.DdrHoldHalfCycle = QSPI_DDR_HHC_ANALOG_DELAY;
	sCommand.SIOOMode = QSPI_SIOO_INST_EVERY_CMD;

	sCommand.DataMode = QSPI_DATA_NONE;
	sCommand.DummyCycles = 0;

	while (EraseEndAddress >= EraseStartAddress) {
		sCommand.Address = (EraseStartAddress & 0x0FFFFFFF);

		if (QSPI_WriteEnable() != HAL_OK) {
			return HAL_ERROR;
		}

		if (HAL_QSPI_Command(&hqspi, &sCommand, HAL_QPSI_TIMEOUT_DEFAULT_VALUE)
				!= HAL_OK) {
			return HAL_ERROR;
		}
		EraseStartAddress += MEMORY_SECTOR_SIZE;

		if (QSPI_AutoPollingMemReady() != HAL_OK) {
			return HAL_ERROR;
		}
	}

	return HAL_OK;
}

uint8_t CSP_QSPI_WriteMemory(uint8_t *buffer, uint32_t address,
		uint32_t buffer_size) {

	QSPI_CommandTypeDef sCommand;
	uint32_t end_addr, current_size, current_addr;

	/* Calculation of the size between the write address and the end of the page */
	current_addr = 0;

	//
	while (current_addr <= address) {
		current_addr += MEMORY_PAGE_SIZE;
	}
	current_size = current_addr - address;

	/* Check if the size of the data is less than the remaining place in the page */
	if (current_size > buffer_size) {
		current_size = buffer_size;
	}

	/* Initialize the adress variables */
	current_addr = address;
	end_addr = address + buffer_size;

	sCommand.InstructionMode = QSPI_INSTRUCTION_1_LINE;
	sCommand.Instruction = QUAD_IN_FAST_PROG_CMD;
	sCommand.AddressMode = QSPI_ADDRESS_1_LINE;
	sCommand.AddressSize = QSPI_ADDRESS_24_BITS;
	sCommand.AlternateByteMode = QSPI_ALTERNATE_BYTES_NONE;
	sCommand.DdrMode = QSPI_DDR_MODE_DISABLE;
	sCommand.DdrHoldHalfCycle = QSPI_DDR_HHC_ANALOG_DELAY;
	sCommand.SIOOMode = QSPI_SIOO_INST_EVERY_CMD;
	sCommand.DataMode = QSPI_DATA_4_LINES;
	sCommand.NbData = buffer_size;
	sCommand.Address = address;
	sCommand.DummyCycles = 0;

	/* Perform the write page by page */
	do {
		sCommand.Address = current_addr;
		sCommand.NbData = current_size;

		if (current_size == 0) {
			return HAL_OK;
		}

		/* Enable write operations */
		if (QSPI_WriteEnable() != HAL_OK) {
			return HAL_ERROR;
		}

		/* Configure the command */
		if (HAL_QSPI_Command(&hqspi, &sCommand, HAL_QPSI_TIMEOUT_DEFAULT_VALUE)
				!= HAL_OK) {

			return HAL_ERROR;
		}

		/* Transmission of the data */
		if (HAL_QSPI_Transmit(&hqspi, buffer, HAL_QPSI_TIMEOUT_DEFAULT_VALUE)
				!= HAL_OK) {

			return HAL_ERROR;
		}

		/* Configure automatic polling mode to wait for end of program */
		if (QSPI_AutoPollingMemReady() != HAL_OK) {
			return HAL_ERROR;
		}

		/* Update the address and size variables for next page programming */
		current_addr += current_size;
		buffer += current_size;
		current_size =
				((current_addr + MEMORY_PAGE_SIZE) > end_addr) ?
						(end_addr - current_addr) : MEMORY_PAGE_SIZE;
	} while (current_addr <= end_addr);

	return HAL_OK;

}


uint8_t CSP_QSPI_EnableMemoryMappedMode(void) {

	QSPI_CommandTypeDef sCommand;
	QSPI_MemoryMappedTypeDef sMemMappedCfg;

	/* Enable Memory-Mapped mode-------------------------------------------------- */

	sCommand.InstructionMode = QSPI_INSTRUCTION_1_LINE;
	sCommand.Instruction = QUAD_IN_OUT_FAST_READ_CMD;
	sCommand.AddressSize = QSPI_ADDRESS_24_BITS;
	sCommand.AddressMode = QSPI_ADDRESS_4_LINES;
	sCommand.Address = 0x00;
	sCommand.AlternateByteMode = QSPI_ALTERNATE_BYTES_NONE;
	sCommand.AlternateBytes = 0xFF;
	sCommand.AlternateBytesSize = 1;
	sCommand.DdrMode = QSPI_DDR_MODE_DISABLE;
	sCommand.DdrHoldHalfCycle = QSPI_DDR_HHC_ANALOG_DELAY;
	sCommand.SIOOMode = QSPI_SIOO_INST_EVERY_CMD;
	sCommand.DataMode = QSPI_DATA_4_LINES;
	sCommand.NbData = 0;
	sCommand.DummyCycles = 6;			//6 is true!

	sMemMappedCfg.TimeOutActivation = QSPI_TIMEOUT_COUNTER_DISABLE;
	sMemMappedCfg.TimeOutPeriod = 0;

	if (HAL_QSPI_MemoryMapped(&hqspi, &sCommand, &sMemMappedCfg) != HAL_OK) {
		return HAL_ERROR;
	}
	HAL_Delay(100);
	return HAL_OK;
}

uint8_t QSPI_ResetChip() {
	QSPI_CommandTypeDef sCommand = { 0 };
	uint32_t temp = 0;
	HAL_StatusTypeDef ret;

	/* Enable Reset --------------------------- */
	sCommand.InstructionMode = QSPI_INSTRUCTION_1_LINE;
	sCommand.Instruction = RESET_ENABLE_CMD;
	sCommand.AddressMode = QSPI_ADDRESS_NONE;
	sCommand.AlternateByteMode = QSPI_ALTERNATE_BYTES_NONE;
	sCommand.DataMode = QSPI_DATA_NONE;
	sCommand.DummyCycles = 0;
	sCommand.DdrMode = QSPI_DDR_MODE_DISABLE;
	sCommand.DdrHoldHalfCycle = QSPI_DDR_HHC_ANALOG_DELAY;
	sCommand.SIOOMode = QSPI_SIOO_INST_EVERY_CMD;

	if ((ret = HAL_QSPI_Command(&hqspi, &sCommand,
			HAL_QPSI_TIMEOUT_DEFAULT_VALUE)) != HAL_OK) {
		return ret;
	}

	/* Reset Device --------------------------- */
	sCommand.InstructionMode = QSPI_INSTRUCTION_1_LINE;
	sCommand.Instruction = RESET_EXECUTE_CMD;
	sCommand.AddressMode = QSPI_ADDRESS_NONE;
	sCommand.AlternateByteMode = QSPI_ALTERNATE_BYTES_NONE;
	sCommand.DataMode = QSPI_DATA_NONE;
	sCommand.DummyCycles = 0;
	sCommand.DdrMode = QSPI_DDR_MODE_DISABLE;
	sCommand.DdrHoldHalfCycle = QSPI_DDR_HHC_ANALOG_DELAY;
	sCommand.SIOOMode = QSPI_SIOO_INST_EVERY_CMD;

	if ((ret = HAL_QSPI_Command(&hqspi, &sCommand,
			HAL_QPSI_TIMEOUT_DEFAULT_VALUE)) != HAL_OK) {
		return ret;
	}

	for (temp = 0; temp < 500000; temp++) {
		__NOP();
	}

	return HAL_OK;
}

uint8_t CSP_QSPI_Read(uint8_t *pData, uint32_t ReadAddr, uint32_t Size) {
	QSPI_CommandTypeDef s_command;

	/* Initialize the read command */
	s_command.InstructionMode = QSPI_INSTRUCTION_1_LINE;
	s_command.Instruction = QUAD_IN_OUT_FAST_READ_CMD;
	s_command.AddressMode = QSPI_ADDRESS_4_LINES;
	s_command.AddressSize = QSPI_ADDRESS_24_BITS;
	s_command.Address = ReadAddr;
	s_command.AlternateByteMode = QSPI_ALTERNATE_BYTES_NONE;
	s_command.DataMode = QSPI_DATA_4_LINES;
	s_command.DummyCycles = 6U;
	s_command.NbData = Size;
	s_command.DdrMode = QSPI_DDR_MODE_DISABLE;
	s_command.DdrHoldHalfCycle = QSPI_DDR_HHC_ANALOG_DELAY;
	s_command.SIOOMode = QSPI_SIOO_INST_EVERY_CMD;

	/* Configure the command */
	if (HAL_QSPI_Command(&hqspi, &s_command, HAL_QPSI_TIMEOUT_DEFAULT_VALUE)
			!= HAL_OK) {
		return HAL_ERROR;
	}

	/* Set S# timing for Read command */
	MODIFY_REG(hqspi.Instance->DCR, QUADSPI_DCR_CSHT,
			QSPI_CS_HIGH_TIME_5_CYCLE);

	/* Reception of the data */
	if (HAL_QSPI_Receive(&hqspi, pData, HAL_QPSI_TIMEOUT_DEFAULT_VALUE)
			!= HAL_OK) {
		return HAL_ERROR;
	}

	/* Restore S# timing for nonRead commands */
	MODIFY_REG(hqspi.Instance->DCR, QUADSPI_DCR_CSHT,
			QSPI_CS_HIGH_TIME_6_CYCLE);

	return HAL_OK;
}


/* USER CODE END 1 */
