djgreeb/XDJ-X/Mixer assy/FW_BACKUP/XDJX_MIXER_ASSY/Inc/audio.h

/////////////////////////////////////////////////////////////////////////////////////////////////
// Audio processing variables
//	product: XDJ-X mixer assy
//
//
//
//
//	Author: Anatska Andrei
//
/////////////////////////////////////////////////////////////////////////////////////////////////

#include "stdint.h"

static int16_t MASTER_BUS[2];
static int16_t HP_BUS[2];
static float CH0IN[2];
static float CH1IN[2];
static float POSTEQCH0[2];
static float POSTEQCH1[2];
static float CUESUM[2];

//////////////////////////////Moog filter
float in1_0, in2_0, in3_0, in4_0, out1_0, out2_0, out3_0, out4_0;
//////////////////////////////Moog filter
float in1_1, in2_1, in3_1, in4_1, out1_1, out2_1, out3_1, out4_1;
//////////////////////////////Moog filter
float in1_2, in2_2, in3_2, in4_2, out1_2, out2_2, out3_2, out4_2;
//////////////////////////////Moog filter
float in1_3, in2_3, in3_3, in4_3, out1_3, out2_3, out3_3, out4_3;

float fcutoff_0, resonanse_0;
float fcutoff_1, resonanse_1;

//////////////////////////////Moog filter
float in1_0h, in2_0h, in3_0h, in4_0h, out1_0h, out2_0h, out3_0h, out4_0h;
//////////////////////////////Moog filter
float in1_1h, in2_1h, in3_1h, in4_1h, out1_1h, out2_1h, out3_1h, out4_1h;
//////////////////////////////Moog filter
float in1_2h, in2_2h, in3_2h, in4_2h, out1_2h, out2_2h, out3_2h, out4_2h;
//////////////////////////////Moog filter
float in1_3h, in2_3h, in3_3h, in4_3h, out1_3h, out2_3h, out3_3h, out4_3h;

float tmpin_0, tmpin_1, tmpin_2, tmpin_3;


float HPHN_ATT = 0.00000; 
float TRM0_ATT = 0.00000; 
float TRM1_ATT = 0.00000;
float CRSF0_ATT = 0.00000;
float CRSF1_ATT = 0.00000;
float FDR0_ATT = 0.00000; 
float FDR1_ATT = 0.00000;
float MIXN0_ATT = 0.00000;
float MIXN1_ATT = 0.00000;


/* RINGBUFFER and BFX ---------------------------------------------------------*/
#define rngmaxsize 130000
uint32_t rngsize = 11025;		// 1/2 for 120bpm 
int16_t RINGBUF[2][rngmaxsize] = {0};
uint32_t rngaddr = 0;
uint8_t rngdiv[8] = {3, 3, 3, 3, 3, 3, 3, 3};   //0 - 1/16 1 - 1/8 ...
float EFFATT, ORIGATT;
float BFXTMP[2];


/* LEVEL METER ---------------------------------------------------------*/
float lvl_ch0 = 0.00000;
float lvl_ch1 = 0.00000;
float lvl_tmp;
uint16_t lvl_ml = 0;
uint16_t lvl_mr = 0;
uint16_t lvl_tmpm;
uint8_t prev_lvl_ch0 = 0; 
uint8_t prev_lvl_ch1 = 0; 
uint8_t prev_lvl_ml = 0; 
uint8_t prev_lvl_mr = 0;
uint8_t prev_pk_ch0 = 0; 
uint8_t prev_pk_ch1 = 0; 
uint8_t prev_pk_ml = 0; 
uint8_t prev_pk_mr = 0;
uint8_t lvlc;
//DJM-900nxs: 15leds down per 933ms. 1 led per 62ms
// peak level stay status 2.0s
#define dwnlvl 3 //(5/75Hz sec) (66,6ms)
uint8_t tim_ch0, tim_ch1, tim_ml, tim_mr;
#define dwnpk 151 //(150/75Hz sec) (2000ms)
uint8_t timpk_ch0, timpk_ch1, timpk_ml, timpk_mr;

/* NOISE CFX ---------------------------------------------------------*/
uint16_t nsmpl;
//noise 8 bit data
const static uint8_t noise[65536] = {
	0x72, 0x7B, 0xE1, 0x7A, 0xD9, 0x4F, 0xCD, 0x3A, 0x74, 0xE5, 0x1C, 0xD3, 0xCE, 0x63, 0x18, 0x50, 
	0x22, 0xA5, 0x23, 0x54, 0x1B, 0xA9, 0x60, 0x59, 0xC7, 0x65, 0xE8, 0xAE, 0xE9, 0x46, 0x09, 0x05, 
	0xBF, 0x81, 0x27, 0x20, 0x19, 0xB9, 0x7C, 0x8C, 0x27, 0xC8, 0x70, 0x6A, 0x39, 0x36, 0x57, 0x21, 
	0x1D, 0x2A, 0x7A, 0xC5, 0x6A, 0xA8, 0x48, 0x84, 0x3F, 0x39, 0xAA, 0x3E, 0xA7, 0x1A, 0x45, 0xEF, 
	0xF9, 0x6D, 0x34, 0xC4, 0xF8, 0x4F, 0xD7, 0xE9, 0x1E, 0xE7, 0xE8, 0x1B, 0xC4, 0x27, 0x9C, 0x2B, 
	0x80, 0x0F, 0xD9, 0xC4, 0x6A, 0xB2, 0x8F, 0xE3, 0x0E, 0x35, 0x72, 0x61, 0xB5, 0xBA, 0xEC, 0x27, 
	0x4A, 0xA8, 0xEE, 0x1E, 0xDD, 0xFB, 0xE4, 0xDB, 0xDB, 0xE2, 0x0B, 0x9F, 0x5B, 0xF6, 0x91, 0xCC, 
	0x70, 0x46, 0x9A, 0x89, 0x8D, 0xAE, 0xD2, 0xEE, 0x10, 0xEC, 0xAD, 0x1D, 0x6D, 0x58, 0xCB, 0x47, 
	0xA6, 0xC9, 0x30, 0xE0, 0x66, 0x85, 0xD5, 0xBA, 0xAC, 0x4B, 0x1C, 0x3D, 0xC7, 0x3B, 0x25, 0x3F, 
	0x93, 0xD5, 0xED, 0xA7, 0x7A, 0x09, 0x15, 0xD3, 0xCC, 0x22, 0xA2, 0x9B, 0x5C, 0x94, 0x2C, 0xE7, 
	0xAC, 0x4B, 0x87, 0x73, 0x21, 0x13, 0x6E, 0xA3, 0x65, 0xC1, 0x7E, 0x41, 0x45, 0xB4, 0xD3, 0x74, 
	0x6A, 0xCC, 0xF5, 0xEB, 0xEC, 0xA8, 0xBD, 0xB2, 0x88, 0x50, 0xA6, 0x73, 0x26, 0xA7, 0x98, 0x80, 
	0x84, 0xAE, 0xAC, 0x31, 0xEB, 0x5E, 0xC8, 0x8A, 0x86, 0x10, 0x55, 0x4F, 0x07, 0x00, 0x70, 0x1B, 
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
1.00000,    
1.00000,    
1.00000,    
1.00000,    
1.00000,    
1.00000,    
1.00000,    
1.00000,    
1.00000,    
1.00000,    
1.00000,    
1.00000,    
1.00000,    
1.00000,    
1.00000,    
1.00000,    
1.00000,    
1.00000,    
1.00000,    
1.00000,    
1.00000,    
1.00000,    
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

	
	
	
////////////////////////////////////////////////////////////////////////////////////////////////////////////////////////
