djgreeb/XDJ-X/FW_BACKUP/XDJX/Src/fmc.c

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

/* Includes ------------------------------------------------------------------*/
#include "fmc.h"

SDRAM_HandleTypeDef hsdram1;

/* FMC initialization function */
void MX_FMC_Init(void)
{
  FMC_SDRAM_TimingTypeDef SdramTiming = {0};

  /** Perform the SDRAM1 memory initialization sequence
  */
  hsdram1.Instance = FMC_SDRAM_DEVICE;
  /* hsdram1.Init */
  hsdram1.Init.SDBank = FMC_SDRAM_BANK1;
  hsdram1.Init.ColumnBitsNumber = FMC_SDRAM_COLUMN_BITS_NUM_9;
  hsdram1.Init.RowBitsNumber = FMC_SDRAM_ROW_BITS_NUM_13;
  hsdram1.Init.MemoryDataWidth = FMC_SDRAM_MEM_BUS_WIDTH_16;
  hsdram1.Init.InternalBankNumber = FMC_SDRAM_INTERN_BANKS_NUM_4;
  hsdram1.Init.CASLatency = FMC_SDRAM_CAS_LATENCY_3;
  hsdram1.Init.WriteProtection = FMC_SDRAM_WRITE_PROTECTION_DISABLE;
  hsdram1.Init.SDClockPeriod = FMC_SDRAM_CLOCK_PERIOD_2;
  hsdram1.Init.ReadBurst = FMC_SDRAM_RBURST_ENABLE;
  hsdram1.Init.ReadPipeDelay = FMC_SDRAM_RPIPE_DELAY_1;
  /* SdramTiming */
  SdramTiming.LoadToActiveDelay = 2;
  SdramTiming.ExitSelfRefreshDelay = 7;
  SdramTiming.SelfRefreshTime = 4;
  SdramTiming.RowCycleDelay = 7;
  SdramTiming.WriteRecoveryTime = 4;
  SdramTiming.RPDelay = 2;
  SdramTiming.RCDDelay = 2;

  if (HAL_SDRAM_Init(&hsdram1, &SdramTiming) != HAL_OK)
  {
    Error_Handler( );
  }

  /* USER CODE BEGIN FMC_Init 2 */

	FMC_SDRAM_CommandTypeDef Cmd;
	Cmd.CommandMode= FMC_SDRAM_CMD_CLK_ENABLE;    //Step 3:  Configure a clock configuration enable command
	Cmd.CommandTarget= FMC_SDRAM_CMD_TARGET_BANK1;/////////// ----------------------------------
	Cmd.AutoRefreshNumber= 1;
	Cmd.ModeRegisterDefinition= 0;
	HAL_SDRAM_SendCommand(&hsdram1, &Cmd, 0x1000);    //Send the command
	HAL_Delay(100);    //Step 4: Insert 100 ms delay

	Cmd.CommandMode= FMC_SDRAM_CMD_PALL;    //Step 5: Configure a PALL (precharge all) command
	Cmd.CommandTarget= FMC_SDRAM_CMD_TARGET_BANK1;
	Cmd.AutoRefreshNumber= 1;
	Cmd.ModeRegisterDefinition= 0;
	HAL_SDRAM_SendCommand(&hsdram1, &Cmd, 0x1000); 

	Cmd.CommandMode= FMC_SDRAM_CMD_AUTOREFRESH_MODE;    //Step 6 : Configure a Auto-Refresh command
	Cmd.CommandTarget= FMC_SDRAM_CMD_TARGET_BANK1;
	Cmd.AutoRefreshNumber= 4;
	Cmd.ModeRegisterDefinition= 0;
	HAL_SDRAM_SendCommand(&hsdram1, &Cmd, 0x1000);

	Cmd.CommandMode= FMC_SDRAM_CMD_LOAD_MODE;
	Cmd.CommandTarget= FMC_SDRAM_CMD_TARGET_BANK1;
	Cmd.AutoRefreshNumber= 1;
	HAL_SDRAM_SendCommand(&hsdram1, &Cmd, 0x1000);

			/* Step 8: Set the refresh rate counter
	64msec / 4096 fresh = 15.62 us 
	refresh count= 15.62usec * 135.5MHz  - 20 = 2096 */
	HAL_SDRAM_ProgramRefreshRate(&hsdram1, 0x0830);     //refresh count
	
	
  /* USER CODE END FMC_Init 2 */
}

static uint32_t FMC_Initialized = 0;

static void HAL_FMC_MspInit(void){
  GPIO_InitTypeDef GPIO_InitStruct = {0};
  if (FMC_Initialized) {
    return;
  }
  FMC_Initialized = 1;

  /* Peripheral clock enable */
  __HAL_RCC_FMC_CLK_ENABLE();

  /** FMC GPIO Configuration
  PE1   ------> FMC_NBL1
  PE0   ------> FMC_NBL0
  PG15   ------> FMC_SDNCAS
  PD0   ------> FMC_D2
  PD1   ------> FMC_D3
  PG8   ------> FMC_SDCLK
  PF2   ------> FMC_A2
  PF1   ------> FMC_A1
  PF0   ------> FMC_A0
  PG5   ------> FMC_BA1
  PF3   ------> FMC_A3
  PG4   ------> FMC_BA0
  PG2   ------> FMC_A12
  PF5   ------> FMC_A5
  PF4   ------> FMC_A4
  PC2   ------> FMC_SDNE0
  PC3   ------> FMC_SDCKE0
  PE10   ------> FMC_D7
  PH5   ------> FMC_SDNWE
  PF13   ------> FMC_A7
  PF14   ------> FMC_A8
  PE9   ------> FMC_D6
  PE11   ------> FMC_D8
  PD15   ------> FMC_D1
  PD14   ------> FMC_D0
  PF12   ------> FMC_A6
  PF15   ------> FMC_A9
  PE12   ------> FMC_D9
  PE15   ------> FMC_D12
  PF11   ------> FMC_SDNRAS
  PG0   ------> FMC_A10
  PE8   ------> FMC_D5
  PE13   ------> FMC_D10
  PD10   ------> FMC_D15
  PD9   ------> FMC_D14
  PG1   ------> FMC_A11
  PE7   ------> FMC_D4
  PE14   ------> FMC_D11
  PD8   ------> FMC_D13
  */
  /* GPIO_InitStruct */
  GPIO_InitStruct.Pin = GPIO_PIN_1|GPIO_PIN_0|GPIO_PIN_10|GPIO_PIN_9
                          |GPIO_PIN_11|GPIO_PIN_12|GPIO_PIN_15|GPIO_PIN_8
                          |GPIO_PIN_13|GPIO_PIN_7|GPIO_PIN_14;
  GPIO_InitStruct.Mode = GPIO_MODE_AF_PP;
  GPIO_InitStruct.Pull = GPIO_NOPULL;
  GPIO_InitStruct.Speed = GPIO_SPEED_FREQ_VERY_HIGH;
  GPIO_InitStruct.Alternate = GPIO_AF12_FMC;

  HAL_GPIO_Init(GPIOE, &GPIO_InitStruct);

  /* GPIO_InitStruct */
  GPIO_InitStruct.Pin = GPIO_PIN_15|GPIO_PIN_8|GPIO_PIN_5|GPIO_PIN_4
                          |GPIO_PIN_2|GPIO_PIN_0|GPIO_PIN_1;
  GPIO_InitStruct.Mode = GPIO_MODE_AF_PP;
  GPIO_InitStruct.Pull = GPIO_NOPULL;
  GPIO_InitStruct.Speed = GPIO_SPEED_FREQ_VERY_HIGH;
  GPIO_InitStruct.Alternate = GPIO_AF12_FMC;

  HAL_GPIO_Init(GPIOG, &GPIO_InitStruct);

  /* GPIO_InitStruct */
  GPIO_InitStruct.Pin = GPIO_PIN_0|GPIO_PIN_1|GPIO_PIN_15|GPIO_PIN_14
                          |GPIO_PIN_10|GPIO_PIN_9|GPIO_PIN_8;
  GPIO_InitStruct.Mode = GPIO_MODE_AF_PP;
  GPIO_InitStruct.Pull = GPIO_NOPULL;
  GPIO_InitStruct.Speed = GPIO_SPEED_FREQ_VERY_HIGH;
  GPIO_InitStruct.Alternate = GPIO_AF12_FMC;

  HAL_GPIO_Init(GPIOD, &GPIO_InitStruct);

  /* GPIO_InitStruct */
  GPIO_InitStruct.Pin = GPIO_PIN_2|GPIO_PIN_1|GPIO_PIN_0|GPIO_PIN_3
                          |GPIO_PIN_5|GPIO_PIN_4|GPIO_PIN_13|GPIO_PIN_14
                          |GPIO_PIN_12|GPIO_PIN_15|GPIO_PIN_11;
  GPIO_InitStruct.Mode = GPIO_MODE_AF_PP;
  GPIO_InitStruct.Pull = GPIO_NOPULL;
  GPIO_InitStruct.Speed = GPIO_SPEED_FREQ_VERY_HIGH;
  GPIO_InitStruct.Alternate = GPIO_AF12_FMC;

  HAL_GPIO_Init(GPIOF, &GPIO_InitStruct);

  /* GPIO_InitStruct */
  GPIO_InitStruct.Pin = GPIO_PIN_2|GPIO_PIN_3;
  GPIO_InitStruct.Mode = GPIO_MODE_AF_PP;
  GPIO_InitStruct.Pull = GPIO_NOPULL;
  GPIO_InitStruct.Speed = GPIO_SPEED_FREQ_VERY_HIGH;
  GPIO_InitStruct.Alternate = GPIO_AF12_FMC;

  HAL_GPIO_Init(GPIOC, &GPIO_InitStruct);

  /* GPIO_InitStruct */
  GPIO_InitStruct.Pin = GPIO_PIN_5;
  GPIO_InitStruct.Mode = GPIO_MODE_AF_PP;
  GPIO_InitStruct.Pull = GPIO_NOPULL;
  GPIO_InitStruct.Speed = GPIO_SPEED_FREQ_VERY_HIGH;
  GPIO_InitStruct.Alternate = GPIO_AF12_FMC;

  HAL_GPIO_Init(GPIOH, &GPIO_InitStruct);

}

void HAL_SDRAM_MspInit(SDRAM_HandleTypeDef* sdramHandle){
  HAL_FMC_MspInit();
}

static uint32_t FMC_DeInitialized = 0;

static void HAL_FMC_MspDeInit(void){
  if (FMC_DeInitialized) {
    return;
  }
  FMC_DeInitialized = 1;
  /* Peripheral clock enable */
  __HAL_RCC_FMC_CLK_DISABLE();

  /** FMC GPIO Configuration
  PE1   ------> FMC_NBL1
  PE0   ------> FMC_NBL0
  PG15   ------> FMC_SDNCAS
  PD0   ------> FMC_D2
  PD1   ------> FMC_D3
  PG8   ------> FMC_SDCLK
  PF2   ------> FMC_A2
  PF1   ------> FMC_A1
  PF0   ------> FMC_A0
  PG5   ------> FMC_BA1
  PF3   ------> FMC_A3
  PG4   ------> FMC_BA0
  PG2   ------> FMC_A12
  PF5   ------> FMC_A5
  PF4   ------> FMC_A4
  PC2   ------> FMC_SDNE0
  PC3   ------> FMC_SDCKE0
  PE10   ------> FMC_D7
  PH5   ------> FMC_SDNWE
  PF13   ------> FMC_A7
  PF14   ------> FMC_A8
  PE9   ------> FMC_D6
  PE11   ------> FMC_D8
  PD15   ------> FMC_D1
  PD14   ------> FMC_D0
  PF12   ------> FMC_A6
  PF15   ------> FMC_A9
  PE12   ------> FMC_D9
  PE15   ------> FMC_D12
  PF11   ------> FMC_SDNRAS
  PG0   ------> FMC_A10
  PE8   ------> FMC_D5
  PE13   ------> FMC_D10
  PD10   ------> FMC_D15
  PD9   ------> FMC_D14
  PG1   ------> FMC_A11
  PE7   ------> FMC_D4
  PE14   ------> FMC_D11
  PD8   ------> FMC_D13
  */

  HAL_GPIO_DeInit(GPIOE, GPIO_PIN_1|GPIO_PIN_0|GPIO_PIN_10|GPIO_PIN_9
                          |GPIO_PIN_11|GPIO_PIN_12|GPIO_PIN_15|GPIO_PIN_8
                          |GPIO_PIN_13|GPIO_PIN_7|GPIO_PIN_14);

  HAL_GPIO_DeInit(GPIOG, GPIO_PIN_15|GPIO_PIN_8|GPIO_PIN_5|GPIO_PIN_4
                          |GPIO_PIN_2|GPIO_PIN_0|GPIO_PIN_1);

  HAL_GPIO_DeInit(GPIOD, GPIO_PIN_0|GPIO_PIN_1|GPIO_PIN_15|GPIO_PIN_14
                          |GPIO_PIN_10|GPIO_PIN_9|GPIO_PIN_8);

  HAL_GPIO_DeInit(GPIOF, GPIO_PIN_2|GPIO_PIN_1|GPIO_PIN_0|GPIO_PIN_3
                          |GPIO_PIN_5|GPIO_PIN_4|GPIO_PIN_13|GPIO_PIN_14
                          |GPIO_PIN_12|GPIO_PIN_15|GPIO_PIN_11);

  HAL_GPIO_DeInit(GPIOC, GPIO_PIN_2|GPIO_PIN_3);

  HAL_GPIO_DeInit(GPIOH, GPIO_PIN_5);

}

void HAL_SDRAM_MspDeInit(SDRAM_HandleTypeDef* sdramHandle){
  HAL_FMC_MspDeInit();
}
/**
  * @}
  */

/**
  * @}
  */
