djgreeb/XDJ-X/DECK_ASSY/FW_BACKUP/XDJ_DECK_UCOM/Inc/VFL_data.h

/////////////////////////////////////////////////////////////////////////////////////////////////
// 	VFL variables and static maps
//	product: XDJ-X deck ucom
//
//
//
//
//	Author: Anatska Andrei
//
/////////////////////////////////////////////////////////////////////////////////////////////////

#include "stdint.h"



const const uint8_t BITOFF[8] = {	0x7F,
																	0xBF,
																	0xDF,
																	0xEF,
																	0xF7,
																	0xFB,
																	0xFD,
																	0xFE };

																	
const const uint8_t BITON[8] = {	0x80,
																	0x40,
																	0x20,
																	0x10,
																	0x08,
																	0x04,
																	0x02,
																	0x01 };


//played segments circle
const const uint16_t PSEGM[135] = {
	125,
	124,
	123,
	378,
	377,
	376,
	375,
	374,
	373,
	372,

	371,
	370,
	369,
	368,
	365,
	362,
	359,
	357,
	355,
	353,

	351,
	349,
	347,
	345,
	343,
	341,
	339,
	337,
	335,
	333,

	331,
	329,
	327,
	325,
	323,
	321,
	319,
	317,
	315,
	313,

	311,
	309,
	307,
	305,
	303,
	301,
	299,
	297,
	295,
	293,

	291,
	289,
	287,
	283,
	279,
	278,
	277,
	276,
	275,
	274,

	273,
	272,
	271,
	270,
	269,
	12,
	11,
	10,
	9,
	8,

	7,
	141,
	142,
	143,
	144,
	145,
	146,
	147,
	148,
	149,

	150,
	151,
	155,
	159,
	161,
	163,
	165,
	167,
	169,
	171,

	173,
	175,
	177,
	179,
	181,
	183,
	185,
	187,
	189,
	191,

	193,
	195,
	197,
	199,
	201,
	203,
	205,
	207,
	209,
	211,

	213,
	215,
	217,
	219,
	221,
	223,
	225,
	227,
	229,
	231,

	234,
	237,
	240,
	241,
	242,
	243,
	244,
	245,
	246,
	247,

	248,
	249,
	250,
	127,
	126 };	



//cue segments circle
const const uint16_t CSEGM[85] = {
	108,
	107,
	105,
	360,
	358,
	356,
	354,
	352,
	350,
	348,

	346,
	344,
	342,
	340,
	338,
	336,
	334,
	332,
	330,
	328,

	326,
	324,
	322,
	320,
	318,
	316,
	314,
	312,
	310,
	308,

	306,
	304,
	302,
	300,
	298,
	296,
	294,
	292,
	290,
	288,

	30,
	29,
	28,
	26,
	25,
	24,
	160,
	162,
	164,
	166,

	168,
	170,
	172,
	174,
	176,
	178,
	180,
	182,
	184,
	186,

	188,
	190,
	192,
	194,
	196,
	198,
	200,
	202,
	204,
	206,

	208,
	210,
	212,
	214,
	216,
	218,
	220,
	222,
	224,
	226,

	228,
	230,
	232,
	111,
	110 };	


////////////////////////////////////////////////////////////////////////////////////////////////////////////////////////////////////////
