djgreeb/XDJ-X/FW_BACKUP/XDJX/Inc/mixer_uart.h

/////////////////////////////////////////////////////////////////////////////////////////////////
// 	mixer uart interrupt 
//	product: XDJ-X
//
//
//
//
//	Author: Anatska Andrei
//
/////////////////////////////////////////////////////////////////////////////////////////////////




	
		
	
////////////////////////////////////////////////////////////////////////////////////////////////////////////////////////
