djgreeb/XDJ-X/FW_BACKUP/XDJX/Inc/pm_uart.h

/////////////////////////////////////////////////////////////////////////////////////////////////
// 	Power manager uart interrupt
//	product: XDJ-X
//
//
//
//
//	Author: Anatska Andrei
//
/////////////////////////////////////////////////////////////////////////////////////////////////



	
		
	
////////////////////////////////////////////////////////////////////////////////////////////////////////////////////////
